bseverns/MOARkNOBS-42/firmware/include/DisplayManager/README.md

# DisplayManager

Part of the firmware `include` jungle. Check the [include README](../README.md) if you get lost in pixels, and the [main firmware README](../../README.md) for the grand tour.

Talks to the SSD1306 OLED and isn't afraid to shout.

## Where it fits

DisplayManager takes button-driven context and splashes it to the SSD1306 over I2C. ConfigManager tells it what to show.

```
[Button ctx] --> DisplayManager --> SSD1306
```

More backstory in the [main firmware README](../../README.md).

## Key Methods

| Call | What it paints |
| ---- | --- |
| `begin()` | Fire up the display hardware |
| `showText(line1, line2, line3)` | Scribble three lines and bail |
| `updateFromContext(ctx)` | Let button events drive the UI |
| `showFilterTuning(labelFreq, freqValue, labelQ, qValue)` | Visualize filter pot tweaks |
| `showArpSettings(lengthTicks, shapeName)` | Keep the arpeggiator honest |
| `showARGInfo(methodName, envA, envB)` | Flash the active ARG combo |

## Typical Use

```cpp
#include "DisplayManager.h"

DisplayManager screen(0x3C, 128, 64);

void setup() {
  screen.begin();
  screen.showText("MN42", "ready");
}

void loop() {
  screen.updateFromContext(ctx);
}
```

For more pixels see [DisplayManager.h](../DisplayManager.h).

## Build Toggle (A/B)

You can force full-frame OLED transfers at compile time:

- Add `-DMN42_OLED_PARTIAL_UPDATES=0` to `build_flags` in `platformio.ini`.
- Omit it (or set to `1`) to keep dirty-region partial updates enabled.
