bseverns/MOARkNOBS-42/docs/examples/max/README.md

# Max Listener Patch

`mn42_listener.maxpat` is a minimal monitor patch for bridge OSC output.

```mermaid
flowchart LR
  MaxPatch[mn42_listener.maxpat]
  Bridge[[MN42 Bridge]]
  Controller((MN42))
  MaxPatch -->|OSC 9000| Bridge
  Bridge -->|serial JSON| Controller
  Controller -->|slot/envelope dump| Bridge --> MaxPatch
```

## Run it

1. Start the bridge:
   ```bash
   node bridge/mn42_bridge.js --osc 9000 --osc-listen 9000
   ```
2. Open `mn42_listener.maxpat` in Max.
3. The patch's `udpreceive 9000` object receives `/mn42/slots` and `/mn42/envelopes`.

Use it as a starting point for mapping, visuals, or DAW control.
