bseverns/MOARkNOBS-42/docs/index.md

---
hide:
  - navigation
  - toc
---

<div class="mn42-landing-hero" markdown="1">

<p class="mn42-eyebrow">Small-batch MIDI/OSC performance instrument</p>

# MOARkNOBS-42

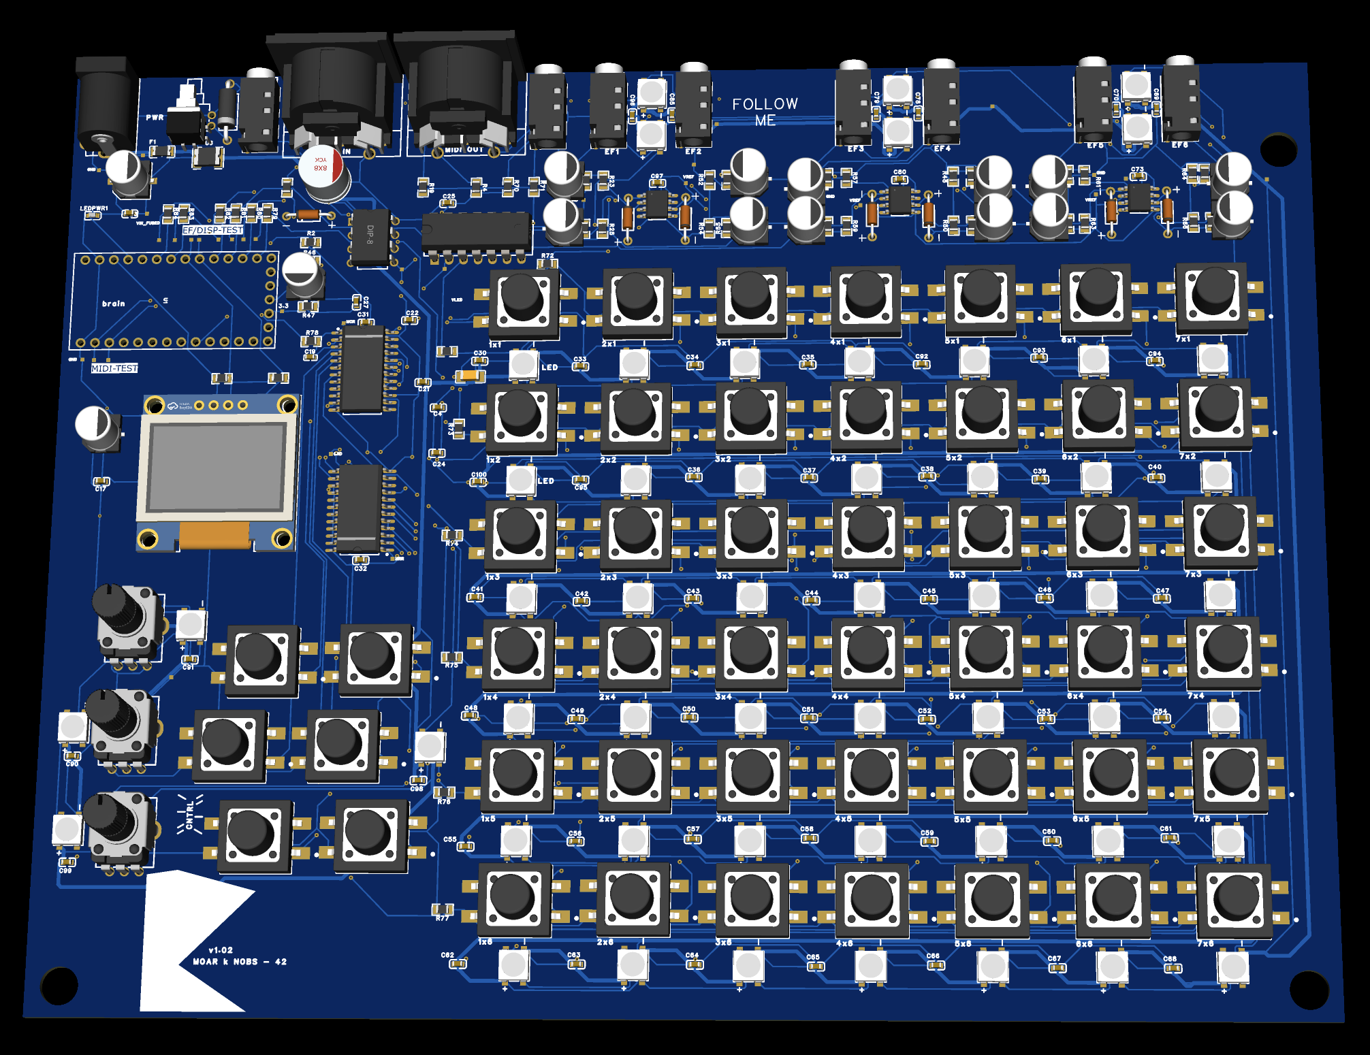
[picture p21: docs/assets/board/moarF.png]
Front view of the MOARkNOBS-42 board showing the full control surface, display area, and hardware layout.


MOARkNOBS-42 is a reactive performance instrument where a hand, a sound, time, or another MIDI device can move a configured destination. The musical work is deciding how those sources cooperate, replace one another, or hand control back to the performer.

Its open hardware, firmware, browser App, profiles, Bridge, and evidence trail keep those unusual relationships visible instead of sealing them inside a preset.

For the whole object-to-software picture in one glance, read the [System Map](getting-started/SystemMap.md).
Teaching a newcomer? Throw them into [Learner Paths](learn/LearnerPaths.md) so they can chase one signal at a time.

<div class="mn42-cta-row">
  <a class="md-button md-button--primary" href="https://bseverns.github.io/MN42/">Try the configurator</a>
  <a class="md-button" href="project/PilotRun/">Read pilot-run framing</a>
  <a class="md-button" href="#core-features">See features</a>
  <a class="md-button" href="getting-started/StartHere/">Start here / learn how it works</a>
</div>

</div>

## Control is the instrument

A knob can establish a baseline. Envelope followers and ARG can let the environment shape a reactive slot. An LFO can add time. On eligible direct CC slots, incoming MIDI can establish a remote value and soft pickup lets the performer physically cross it to take control back without a jump.

These are explicit, bounded behaviors rather than one vague “modulation” feature. [Who Controls This Slot?](learn/OneSignalPath.md) shows the reactive-composition and external-takeover paths side by side. [Why MN42](getting-started/WhyMN42.md) explains why that model matters musically.

## Validated host surfaces

<div class="mn42-callout mn42-callout-support" markdown="1">

The broad workflow story is real, but the compatibility claim should be read conservatively.

- strongest direct-browser evidence in this repo: Chromium-based configurator over WebSerial
- strongest desktop host evidence in this repo: Node 24 bridge with the browser console and `/app/` configurator path
- documented but still setup-specific: OSC hosts and DAW virtual MIDI workflows
- not claimed here as a verified production path: Firefox/Safari WebSerial and signed one-click bridge installers

See [Host Compatibility](reference/HostCompatibility.md) and [Connectivity Guide](getting-started/ConnectivityGuide.md) before treating the project like a universal host/browser promise.

If you want the repo's document tie-break rules before you go deeper, read [Documentation Truth Map](reference/DocumentationTruthMap.md).

</div>

## What it is

MOARkNOBS-42 is a small-batch MIDI/OSC performance instrument with a surrounding ecosystem, not just a bare controller board.

The object in your hands is only part of the story.

<div class="grid cards mn42-card-grid" markdown="1">

- **Surface**

  The hardware is a real performance surface with documented signal flow, MIDI I/O, reactive inputs, and a control layout meant to stay legible.

- **Configurator**

  The browser configurator handles setup, monitoring, staged edits, and profile management without hiding the device contract behind mystery software.

- **Bridge**

  The bridge path opens documented OSC and virtual MIDI workflows when direct browser connection is not the right fit for the host setup.

</div>

If you want the short outsider-friendly version first, read [Why MN42](getting-started/WhyMN42.md).

## Why it feels different

Many controllers are designed to disappear behind presets, hidden mappings, or sealed software stacks. MOARkNOBS-42 goes the other direction: it makes value ownership and contribution part of the performance.

- A physical baseline can be shaped by sound and time through documented route modes.
- Profile-owned incoming MIDI can control eligible destinations without the App or Bridge attached.
- Soft pickup lets the performer's hand resume control without snapping the value.
- The hardware, firmware, configurator, and bridge are documented as one legible system.
- The instrument is open enough to rebuild, audit, and remix rather than merely consume.
- The docs are part of the instrument, not a last-minute appendix.
- Validation, support boundaries, and unverified areas are called out directly instead of buried under marketing language.

The goal is not mass-market smoothness. The goal is an instrument whose control logic stays visible.

## Core features

<div class="grid cards mn42-card-grid" markdown="1">

- **42 virtual slots**

  The instrument centers around 42 virtual slots that can be mapped, recalled, and watched as part of the same runtime system.

- **Six envelope followers**

  Six reactive inputs let the rig respond to real signal activity instead of only static knob gestures.

- **Browser configurator**

  The configurator handles setup, monitoring, staged edits, and profile work in plain language over the documented device contract.

- **Profiles and recall**

  Profile slots `A` through `D` preserve working states, including reactive behavior and incoming MIDI bindings, instead of requiring a live rebuild.

- **Incoming MIDI takeover**

  Firmware-owned CC routes let other machines control supported destinations, with Continuous, Momentary, Toggle, range, and takeover behavior stored in the profile.

- **OSC / virtual MIDI bridge**

  The bridge exposes documented OSC and virtual MIDI paths, and now includes a browser-driven local console.

- **Dual MIDI hardware formats**

  Current repo docs describe both 5-pin DIN and 1/8" TRS Type-A MIDI hardware support.

</div>

## Who it's for

<div class="grid cards mn42-card-grid" markdown="1">

- **Experimental musicians**

  For performers who want the controller to be part of the instrument, not just a utility layer.

- **Sound and media artists**

  For people working across browser tools, OSC hosts, DAWs, installation contexts, or custom performance setups.

- **Advanced builders**

  For people comfortable with hardware reference files, flashing firmware, and validating real hardware behavior on the bench.

- **Educators and instrument hackers**

  For workshops, studios, and classrooms where openness, legibility, and rebuildability matter as much as the final sound.

</div>

This is best suited to people who are comfortable exploring systems rather than expecting every edge case to be hidden behind a wizard.

## Pilot Run / Artist Edition

The right frame for a first small-batch release is a pilot run: an artist-run instrument release with a documented ecosystem around it, not a generic consumer launch.

What that currently means in this project:

- the instrument hardware itself
- the current firmware and its documented behavior
- the browser configurator workflow
- the OSC / virtual MIDI bridge workflow
- the builder, performer, validation, and troubleshooting docs that explain how to use and verify it

What it does not mean:

- implied mass-market support coverage
- undocumented host compatibility guarantees
- invented timelines, pricing, or bundle promises that are not yet published

See [Pilot Run / Artist Edition](project/PilotRun.md) for the project-specific explanation.

## What it is not

<div class="mn42-callout mn42-callout-not" markdown="1">

This is not a generic plug-and-play controller for everyone.

It is not framed here as a sealed appliance, a beginner-friendly consumer gadget, or a promise that every host/workflow has already been validated. It is a particular kind of open, teachable performance instrument for people who value legibility, modification, and documented behavior.

</div>

## Support boundary

<div class="mn42-callout mn42-callout-support" markdown="1">

Support here is docs-first and artist-run.

The repo publishes workflows, validation guidance, and support boundaries clearly, but it does not promise consumer-style warranty handling, substitute-part approval, or universal one-on-one setup support. The practical boundary is described in [License and Support](project/LicenseAndSupport.md).

</div>

## Interested in the first batch?

<div class="mn42-callout mn42-callout-pilot" markdown="1">

If the instrument makes sense for your setup, the next useful step is not a vague preorder mindset. It is reading the pilot-run framing, checking the support boundary, and choosing the workflow path that matches how you actually work.

<div class="mn42-cta-row">
  <a class="md-button md-button--primary" href="project/PilotRun/">Read pilot run details</a>
  <a class="md-button" href="project/LicenseAndSupport/">Read support boundary</a>
  <a class="md-button" href="getting-started/QuickstartForPerformers/">See performer workflow</a>
</div>

</div>

## Choose your next step

<div class="grid cards mn42-card-grid" markdown="1">

- **Quickstart for Builders**

  Ordering parts, flashing firmware, and first bring-up: [Quickstart for Builders](getting-started/QuickstartForBuilders.md)

- **Quickstart for Performers**

  Connect the board, use the configurator, and work with profiles: [Quickstart for Performers](getting-started/QuickstartForPerformers.md)

- **Connectivity Guide**

  Decide between direct WebSerial and the bridge path: [Connectivity Guide](getting-started/ConnectivityGuide.md)

- **Validation Flow**

  Use the conservative go/no-go path from bring-up to demo-ready: [Validation Flow](validation/ValidationFlow.md)

- **Documentation Truth Map**

  See which pages define current truth versus plans, evidence, or historical context: [Documentation Truth Map](reference/DocumentationTruthMap.md)

- **Demo Test Punch List**

  Run a real-world prototype or rehearsal pass: [Demo Test Punch List](validation/DemoTestPunchList.md)

- **Guided Routes and deep docs**

  Choose a learning path or dive into the dense technical library: [Guided Routes](getting-started/GuidedRoutes.md) and [Docs Guide](project/DocsGuide.md)

</div>

## FAQ

<details markdown="1">
  <summary>Do I need to code?</summary>

Not necessarily. A performer can use the configurator and profile workflow without changing firmware. A builder or remixer will get much more out of the project if they are comfortable reading docs, flashing firmware, and following validation steps.

</details>

<details markdown="1">
  <summary>Is it open source?</summary>

Yes. The repo publishes firmware, software, hardware documentation, and supporting docs under the licenses described in [License and Support](project/LicenseAndSupport.md).

</details>

<details markdown="1">
  <summary>Is this a finished consumer product?</summary>

Not in the sense of a mass-market plug-and-play device with universal compatibility claims. The project is documented, real, and usable, but it is still framed honestly as a small-batch, artist-run instrument ecosystem with explicit validation and support boundaries.

</details>

<details markdown="1">
  <summary>What does the configurator do?</summary>

The browser configurator is the main setup and monitoring surface. It loads manifest/config data, stages edits safely, applies changes, and handles profile save/load workflows over the documented device contract.

</details>

<details markdown="1">
  <summary>What support is included?</summary>

The main support surface is the documentation itself: quickstarts, connectivity guidance, validation flow, troubleshooting, and license/support boundaries. Use [GitHub Issues](https://github.com/bseverns/MOARkNOBS-42/issues) for public questions or reproducible bugs. See [License and Support](project/LicenseAndSupport.md) and [Pilot Run](project/PilotRun.md) for the practical limits and private contact path.

</details>

<details markdown="1">
  <summary>Why would I choose this instead of a generic MIDI controller?</summary>

Because the value here is not just the control surface. It is the combination of hardware, firmware, configurator, bridge, and unusually explicit documentation. If that matters to you, read [Why MN42](getting-started/WhyMN42.md).

</details>
