bseverns/MOARkNOBS-42/wiki/Firmware.md

# Firmware

Firmware lives under `firmware/` and targets Teensy 4.0.
Canonical source: `firmware/README.md`

## Build commands

Run from repo root:

```bash
pio run -d firmware -e teensy40_main
pio run -d firmware -e teensy40_main -t upload
```

## Test environments

- `teensy40_full_system`
- `teensy40_unified_test`
- `teensy40_biquad_test`
- `teensy40_eeprom_persistence`
- `teensy40_slot_verify`
- `teensy40_unity` (Unity harness)

## Key modules

- `ButtonManager` - matrix scanning, gesture handling
- `PotentiometerManager` - analog sampling and smoothing
- `EnvelopeFollower` - modulation extraction and filter modes
- `MIDIHandler` - USB/DIN/TRS message handling
- `ConfigManager` - generation-backed LittleFS persistence, validation, and
  recovery
- `LEDManager` + `LedAnimator` - visual state
- `Arpeggiator`, `LFOManager`, `ARGMixer` - modulation engines

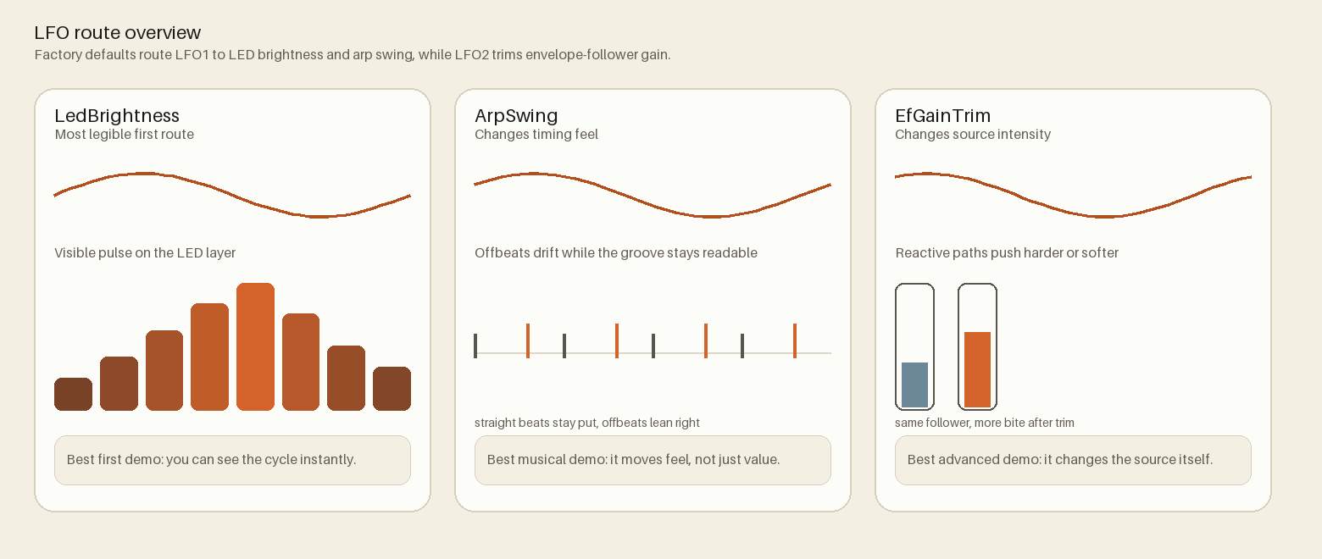
[picture p23: wiki/assets/signal-shapes/lfo-route-overview.png]
LFO routing overview showing two low-frequency oscillators feeding internal targets, MIDI CC and NRPN outputs, slot values, envelope gain trim, and LED brightness.


## Runtime and protocol highlights

- Command dispatch and queue processing are split for clearer ownership.
- JSON manifest/config handshake drives host UI compatibility.
- Scheduler separates high/mid/low priority tasks.

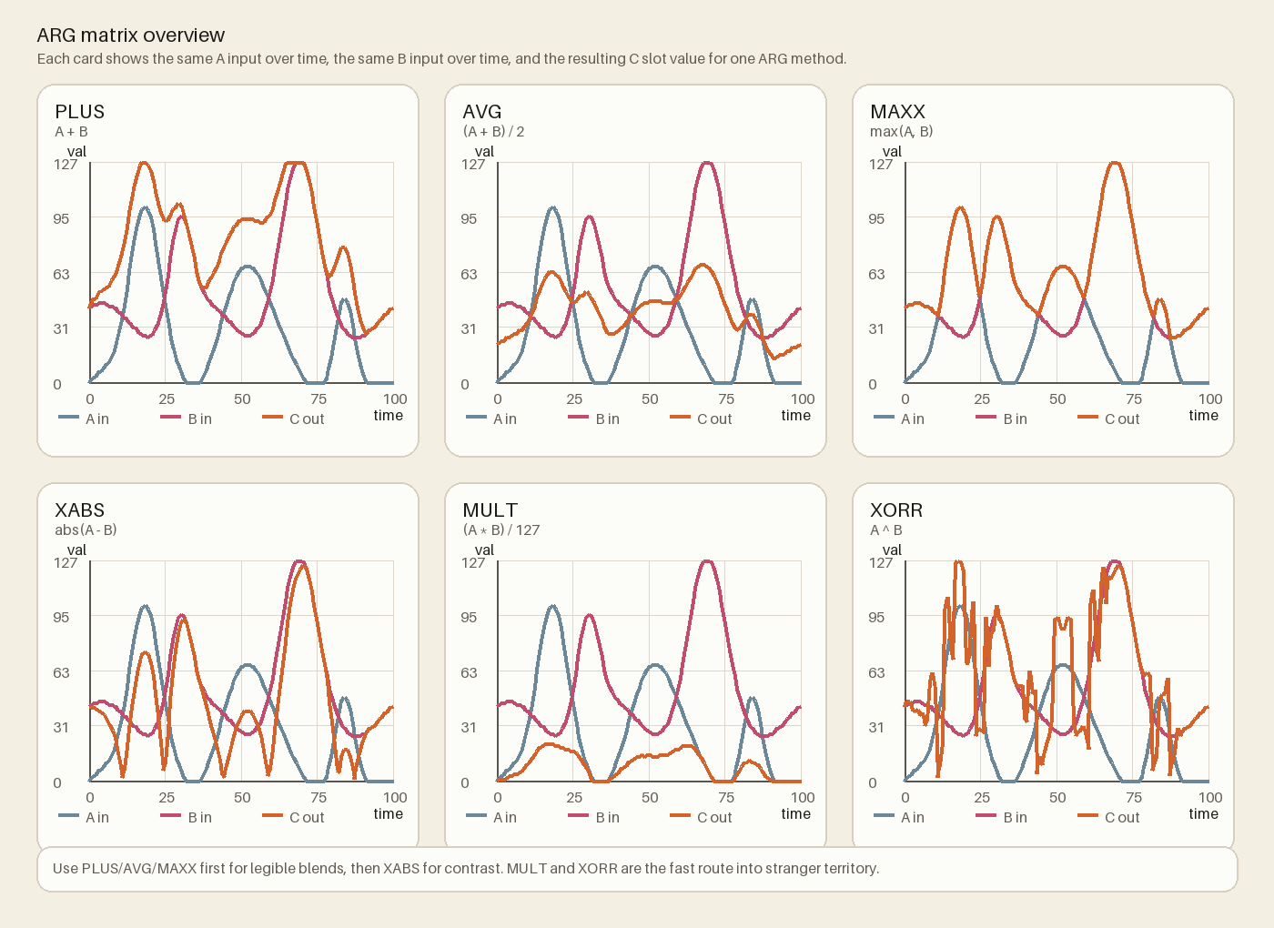
[picture p24: wiki/assets/signal-shapes/arg-matrix-overview.png]
ARG overview comparing two input envelopes with the resulting output for PLUS, average, maximum, absolute difference, multiplication, and XOR-style methods.


## Envelope shape quick look

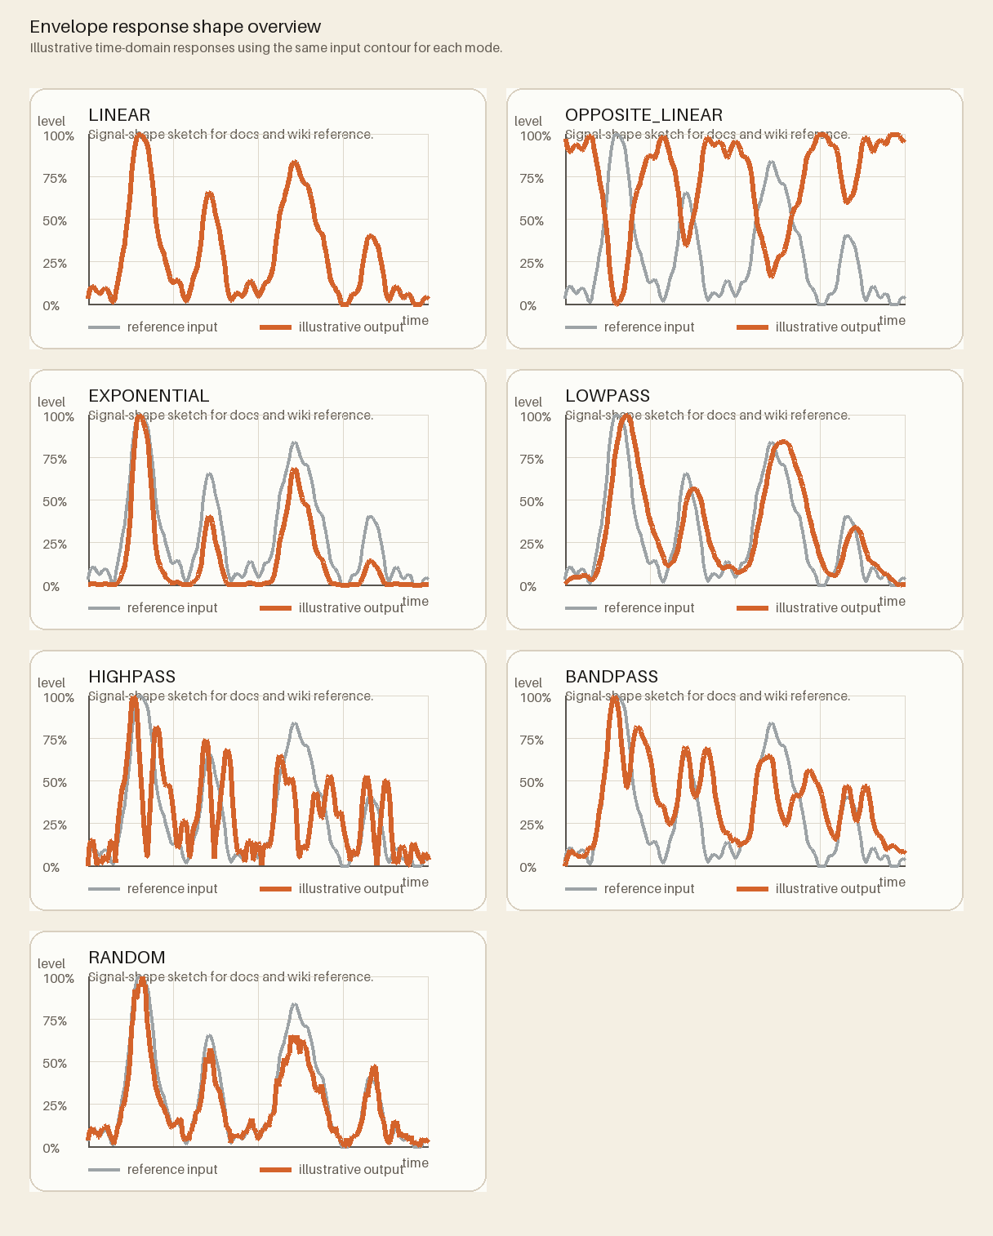
[picture p25: wiki/assets/signal-shapes/filter-shapes-overview.png]
Overview chart comparing one reference envelope against LINEAR, OPPOSITE_LINEAR, EXPONENTIAL, LOWPASS, HIGHPASS, BANDPASS, and RANDOM response modes so newcomers can see how the firmware's reactive-control shapes differ.


Use this as a fast visual map only. The deeper learner-facing explanations live in `docs/guides/FilterFeelGuide.md` and `docs/guides/ReactiveControlGuide.md`.

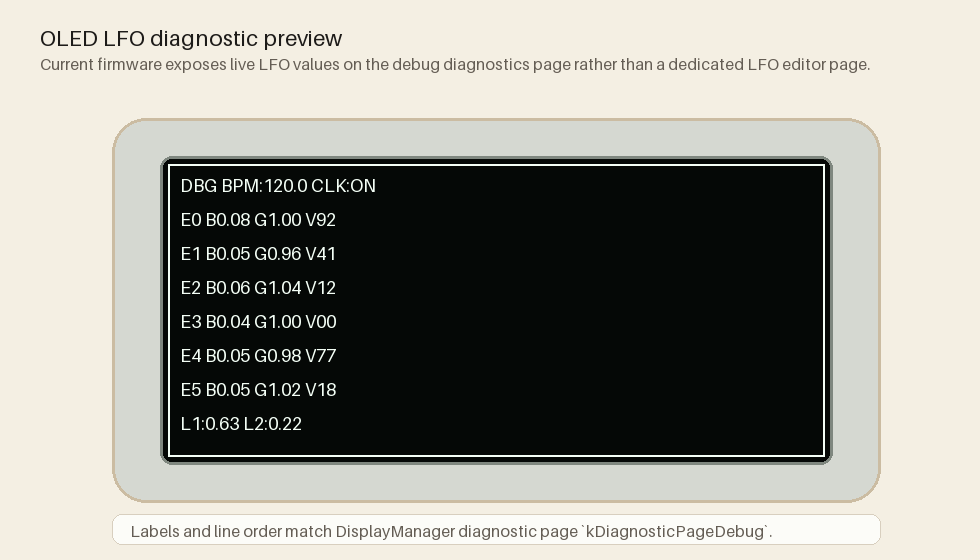
[picture p26: wiki/assets/signal-shapes/lfo-oled-preview.png]
Mock OLED diagnostics view showing BPM and clock status, six envelope baseline-gain-value rows, and two normalized LFO values.


## Reference docs

- `firmware/README.md`
- `firmware/include/*/README.md`
- `docs/guides/WebSerial.md`
- `docs/reference/PinMap.md`
- `docs/reference/PersistenceContract.md`
- `docs/reference/EEPROMLayout.md` (legacy schema-4 layout only)
