bseverns/MOARkNOBS-42/docs/app/AppBehaviorContract.md

# App Behavior Contract

> **Doc class:** Contract. This page defines browser-configurator behavior. The concise [App README](https://github.com/bseverns/MOARkNOBS-42/blob/main/App/README.md) is the operational entry point.

## Runtime ownership

- `App/runtime.js` is the runtime composition root. It wires transport, contract, configuration-session, telemetry, and
  live-control services, but does not define their schema, transaction, or device-policy rules.
- `App/views/benzknobz.js` is the view composition root. It assembles panels/controllers and binds operator controls to
  the public runtime API; device truth and write policy must remain behind those dependencies. `App/views/panels/lab_bench.js`
  owns the Bench's spatial composition and reparenting while preserving the DOM identities owned by its controllers.
- `App/runtime/` owns manifest/schema negotiation, state normalization, validation, staged diffs, checksummed Apply,
  uncertainty/resynchronization, telemetry coalescing, and transport-specific behavior.
- `App/config_schema.json` is the bundled schema 9 fallback. A compatible device-provided schema takes precedence.
- `App/benzknobz.css` defines shared visual tokens and mode presentation.

The view must not invent device truth. Identity, capabilities, configuration, persistence actions, and power-safety
metadata remain manifest-, schema-, command-, or telemetry-backed.

## Transport modes

The App supports direct WebSerial, structured Bridge session, raw Bridge compatibility, and simulator transports. Their
operator labels and truth boundaries are normative in [App Transport Truth Table](AppTransportTruthTable.md).

Direct WebSerial requires a secure context or localhost and a user gesture for port selection. The App may remember
USB identifiers and a staged snapshot, but it must not reopen a serial port without a user gesture.

## Handshake and compatibility

Connect remains busy until transport handlers and runtime subscriptions are bound. A successful device session obtains
identity, manifest, schema, and configuration before enabling authoritative editing. Before that handshake, bundled
fallback data must not be presented as attached-device truth.

A schema mismatch enters `migration-required` and blocks Apply. The App supports export and inspection in that state;
it must not advertise a migration transform until that transform, validation, diff, and operator confirmation flow is
implemented and tested.

## Draft and Apply semantics

The browser maintains live device state separately from a staged candidate. Edits, imported JSON, and recipe actions
update the candidate first. A write occurs only through an explicit action on the relevant write lane.

The primary configuration Apply sends a validated, checksummed candidate. A valid receipt plus authoritative readback
establishes device truth. Missing, malformed, or contradictory receipts enter uncertainty/resynchronization; they do not
prove rollback. The candidate stays visible until readback resolves the outcome.

Profile, scene, macro-recall, and transport actions use their native command paths rather than masquerading as config
diffs. Actions that can replace a dirty configuration draft must be blocked until the operator applies or discards it.
Schema-rendered controls stage browser intent synchronously and debounce only outbound live patches. Destroying or
rebuilding a rendered control must cancel its pending transmission without discarding the staged edit. Removing an
array item remains authoritative over timers owned by that item's former controls.

The complete state model is [Configuration Transaction Model](../reference/ConfigurationTransactionModel.md).

## UI modes

- **Stage** is the performance surface: connection, live profile/scene recall, power safety, slot activity, envelope
  levels, motion, and panic help.
- **Configure** is the default selected-slot workspace: Mapping, one Reactive path (EF source, ARG relationship, then EF character), and Motion/fixed LFO lanes. ARG constructs the Reactive input before EF shaping; it is not a peer output stage. Motion shows each shared generator’s shape and rate while generator edits remain in Lab.
  The signal strip displays device observations separately from staged settings.
- **Lab** exposes complete EF, ARG, fixed-LFO, filter, LED, scope, MIDI-monitor, import/export, and diagnostic controls.
  Every device-schema configuration root must have a marked Lab surface, and the hand-built selected-slot editor must
  account for every slot-schema leaf. Its full-width Bench separates Instrument, Profile, Observe, and Evidence
  workspaces while keeping each room's major tools named in the Bench navigation. Scope, MIDI Monitor, Device Monitor,
  Modulation Matrix, Staged Diff, Slot Inspector, and Debug Log must remain discoverable even when their room is closed.
  Instrument visually separates staged **Machine configuration** (Apply required) from immediate **Live device controls**
  (writes now), without splitting either into a separate Lab room. Lab uses a compact, consistent set of inline SVG
  landmarks for rooms and major tools: faders for Instrument, a saved card for Profile, a scope for Observe, and a
  document lens for Evidence. Major cards repeat their room's visual language or use a specific musical/control
  metaphor. The SVGs remain decorative and text labels remain authoritative; dense telemetry cells stay icon-free.

Lab presents profile-owned incoming MIDI routes as the **Incoming MIDI** tab in **Profile Performance**, beside the
profile arpeggiator and LFO/routes tabs. It must not place those routes inside **Selected Slot**: a route can target any
slot or a machine-level performance parameter and travels with its profile.

The selected-slot Mapping tab names `data1` according to the chosen outgoing message: **CC number**, **Note number**,
**Program number**, **NRPN parameter**, or **RPN parameter**. It omits that control for OFF, Pitch Bend, Aftertouch,
Mod Wheel, and SysEx; SysEx exposes its template instead. Hiding the control does not clear the staged `data1` value.

Envelope detection mode is slot-owned (`slots[].ef.mode`). Two slots may share one physical follower assignment while
keeping different Peak, RMS, Gate, or Follower settings. The top-level `envelopeMode` value is a legacy
compatibility/OLED label; changing it must not rewrite any slot's detector mode.

The persisted compatibility values remain `stage`, `basic`, and `advanced`. A mode may hide complexity, but it must not
change the authority or write semantics of the underlying state.

The State drawer groups presets, profile persistence, and file backups without merging their authority. Selected-slot
markers reflect exact staged diffs. Review focuses the matching Lab field; Customize/Return preserve slot and lane.
Continuous Lab slot controls support sliders and reset-to-confirmed staging, with logarithmic millisecond travel.
Signal contribution graphics require a coherent, recent measured snapshot; missing components remain unreported.

## Device-backed and browser-local state

Device-backed controls must be advertised by the manifest/schema or a documented live protocol lane. Browser-only slot
labels remain local metadata and must not be serialized as device configuration. Legacy browser-local MIDI-badge
metadata may still be read, but Configure does not expose it as instrument behavior. Optional display metadata sent to
the Bridge remains advisory and cannot affect routing authority.

Import stages configuration locally. Export saves the current candidate, including unsent edits. Profile A–D actions,
scene actions, macro actions, and live controls remain capability-gated so older firmware fails closed.

## Telemetry and visualization

The runtime coalesces telemetry into approximately 50 ms paint frames. Scope time is host-observed arrival time, not
firmware-source time or round-trip latency. EF and LFO traces, activity holds, and simulator traces are musical/operator
visualization; latency-grade claims require the [bench latency method](../bench/latency/method.md).

The simulator uses the same runtime API and deterministic synthetic telemetry. **Start Simulator** opens the
firmware-canonical reset fixture: Profile A, channel 1 / CC 0 pots, default EF payloads, disabled slots and ARG, and
no LFO routes. **Load Demo Rig** is an explicit simulator-only fixture with illustrative mappings, EF/ARG examples,
and active LFO routes. Session names the active fixture, and loading a fixture replaces the simulator's authoritative
configuration rather than staging browser intent. Its selected-slot contribution frames and Mod Matrix consume the same
active-profile LFO routing graph, including the firmware compatibility rule that a fixed slot lane shadows an older
SlotValue route for the same slot/LFO pair. Contribution frames honor confirmed ARG sources/methods and each fixed LFO
lane's enabled, amount, and combine settings so the causal signal strip can rehearse the device resolver accurately.
It is suitable for UI behavior, automation, screenshots, schema/migration rehearsal, and staged-transaction tests. It
is not analog calibration, electrical, physical-control, transport-latency, or hardware-validation evidence.

## Accessibility and input

Controls require visible labels, keyboard operation, logical focus order, and non-color status cues. The selected-slot
surface supports arrow-key navigation and documented coarse/fine adjustment. Dialogs and status announcements must
remain usable without relying on pointer interaction or color alone.

Because the current incoming route schema supports only 7-bit Control Change, the route editor labels the source group
**Incoming CC** and does not render a one-option message-type selector. If the negotiated schema advertises multiple
message types, that field becomes a selector. Takeover remains stored for each route but is disabled and unfocusable
unless Interaction is Continuous, because it has no runtime effect for Momentary or Toggle routes.

## Verification

Run:

```bash
npm --prefix App test
npm --prefix App run test:architecture
```

Playwright exercises the real runtime/view modules through the stable `benzknobz.html` harness, including simulator,
schema validation, staged diff, Apply/receipt failures, uncertainty recovery, migration blocking, profiles, and the
mode surfaces. A small approved snapshot set protects the top-level Configure, Lab, Stage, and open Incoming MIDI
hierarchies. Because the App deliberately uses native system UI and monospace font stacks, those approved images run on
the canonical macOS + pinned Playwright Chromium CI lane; other platforms skip only these four pixel assertions and
still run the remaining App suite. Routine screenshot artifacts remain diagnostic rather than approved baselines. `lab_config_coverage.spec.js`
derives its expected roots and slot leaves from the canonical schema, then checks that Lab marks every one and preserves
independent slot EF modes through Apply/readback. The architecture guard
rejects coordinator imports that bypass the public layers and policy-shaped code that would pull schema constraints,
transaction semantics, or device capability decisions back into the two composition roots. Operator-facing hardware
claims additionally require receipts under `docs/bench/app/`.
