bseverns/MOARkNOBS-42/docs/bridge/BridgeConsoleTour.md

# Bridge Console Tour

The Bridge console is the operator-facing desktop view for `MN42 Bridge`. Use it when you need desktop OSC/MIDI routing, a cached device session, or an App-over-bridge path that does not depend on browser WebSerial support.

For the full Bridge doc split, see [Bridge Docs Map](BridgeDocsMap.md).
For transport and support-boundary tie-breaks, see [Bridge README](https://github.com/bseverns/MOARkNOBS-42/blob/main/bridge/README.md), [Bridge Transport Contract](./BridgeTransportContract.md), and [Bridge Write Lanes](./BridgeWriteLanes.md).

## Before You Start

- Start the console with `npm --prefix bridge start`.
- Open `http://127.0.0.1:8787/`.
- Use Node `24.x` only; the Bridge package still pins `>=24 <25`.

Screenshot note: the images below were captured on 2026-08-03 from the local Bridge console against the repository's MN42 device simulator. They preserve a complete cached-session example but predate the visible label change from `Mappings / Stage / Advanced` to `Routing / Monitor / Diagnostics`; they also predate the September patchbay redesign. They are historical UI documentation, not hardware validation evidence.

Simulator session example from this capture:

- serial path: `/dev/simulated-mn42`
- firmware identity: `MOARkNOBS-42` / schema `8` / git `simulated`
- power boundary: `POWER_CHOKED_V1`
- LED cap: `26`
- rail state: `unverified`

## Setup Mode

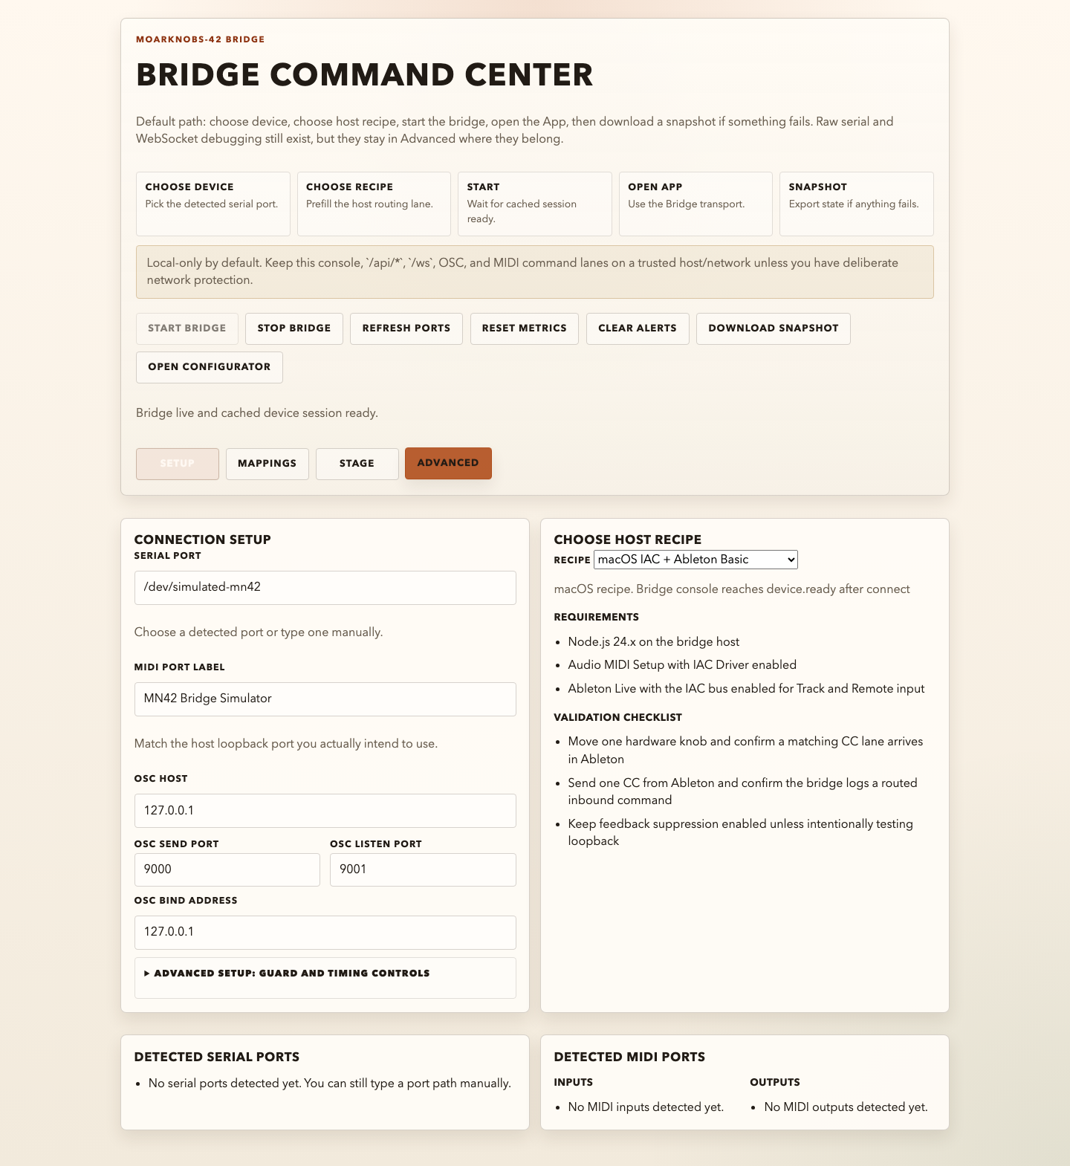
[picture p27: docs/images/bridge-setup-mode.png]
Bridge console Setup mode with serial port entry, recipe picker, and start controls


Setup mode is where a non-developer operator should start.

This capture shows a complete setup path, including the simulator serial path, a simulator MIDI label, and the top-line `Bridge live and cached device session ready.` status after the operator has started the Bridge.

- `Serial port` is the firmware USB path. Pick a detected entry from the list or type it manually if the detector missed it.
- `Host recipe` prefills documented host settings and shows the resolved MIDI and OSC destinations. It is the fastest safe path for an operator who is not debugging custom routing.
- `Edit routing details` reveals the MIDI port and raw OSC address/port fields when this computer differs from the recipe. Its nested guard and timing controls should stay at their defaults unless a host recipe or bench note says otherwise.
- `My Performance Setups` saves named copies of computer/rig routing, destination names, routes, optional notes, and an advisory MN42 profile in this browser. Loading a setup only fills the form; it never starts or restarts routing or changes firmware state. Use JSON export/import to back up the collection or move it to another browser.
- `Start current setup` launches the desktop runtime from the manual workbench. `Stop bridge` remains available in every mode, is visually marked as destructive, and asks for confirmation before disconnecting the serial/MIDI/OSC runtime. `Refresh ports` rescans serial and MIDI devices.

When saved setups exist, Setup leads with a rig recall card showing exact ports, destination names, the advisory profile, notes, and last-used time. **Start this setup** explicitly loads and starts that saved host configuration, preserving its ports even if another device is detected. It is disabled while routing runs. **Edit** and **New setup** reveal the collapsed manual workbench; Edit loads the selected rig into its editor. Last-used time is recorded after a successful start and survives JSON export/import; older version 1 files remain compatible.

Performance Setups are personal operator convenience, not known-good recipes or host-validation evidence. When routing is already running, stop and start the Bridge deliberately after loading a setup whose MIDI or OSC transport values should take effect.

### Serial Port Selection

The serial chooser is intentionally simple:

- Prefer the detected list first.
- If the board appears as `/dev/tty.*` on macOS, the console will prefer the matching `/dev/cu.*` path for you.
- If nothing is detected, you can still type the port path manually and start the Bridge.

## Routing Mode

Routing mode provides a guided, passive MIDI-learn path for custom MIDI CC → OSC routing:

1. Start the Bridge and select `Listen for MIDI CC`.
2. Move one knob, fader, or pedal. The console captures its channel and CC number from the inbound route trace; feedback-suppressed echoes are ignored.
3. Choose a recently observed custom outbound OSC address or type the destination required by your host patch. The learner excludes the reserved `/mn42/*` namespace because those addresses have documented payload contracts.
4. Review the inline route summary and select `Confirm and add route`.

Learning does not emit MIDI, OSC, or device writes. The **Live now** badge marks MIDI → OSC custom routes because adding or removing a confirmed route updates live Bridge routing without restarting transports. Routes loaded into the Setup form from a Performance Setup are pending setup changes until the Bridge is deliberately started with that setup. A custom route is additive: its inbound CC still follows the existing typed OSC and device-control lanes. Custom routes remain intentionally limited to MIDI CC input and OSC output; use the Diagnostics route trace when you need to verify a more complex typed-event path.

### Device telemetry → MIDI

The **Next start** badge marks Device → MIDI routes. Add a route by choosing Slot or EF, a source number starting at 1, MIDI CC 0–127, and channel 1–16. Cards show pending routes and offer Remove. Sources absent from telemetry produce no output. Choose **Configured routes** to use the cards on the next Bridge start; legacy mode retains automatic CC assignments. These changes do not update running transports.

**Advanced / Edit raw route definition** retains JSON access with zero-based source indices. Invalid JSON, invalid entries, duplicate IDs, and more than 128 routes are rejected; correct the definition before starting or saving a setup.

## Monitor Mode

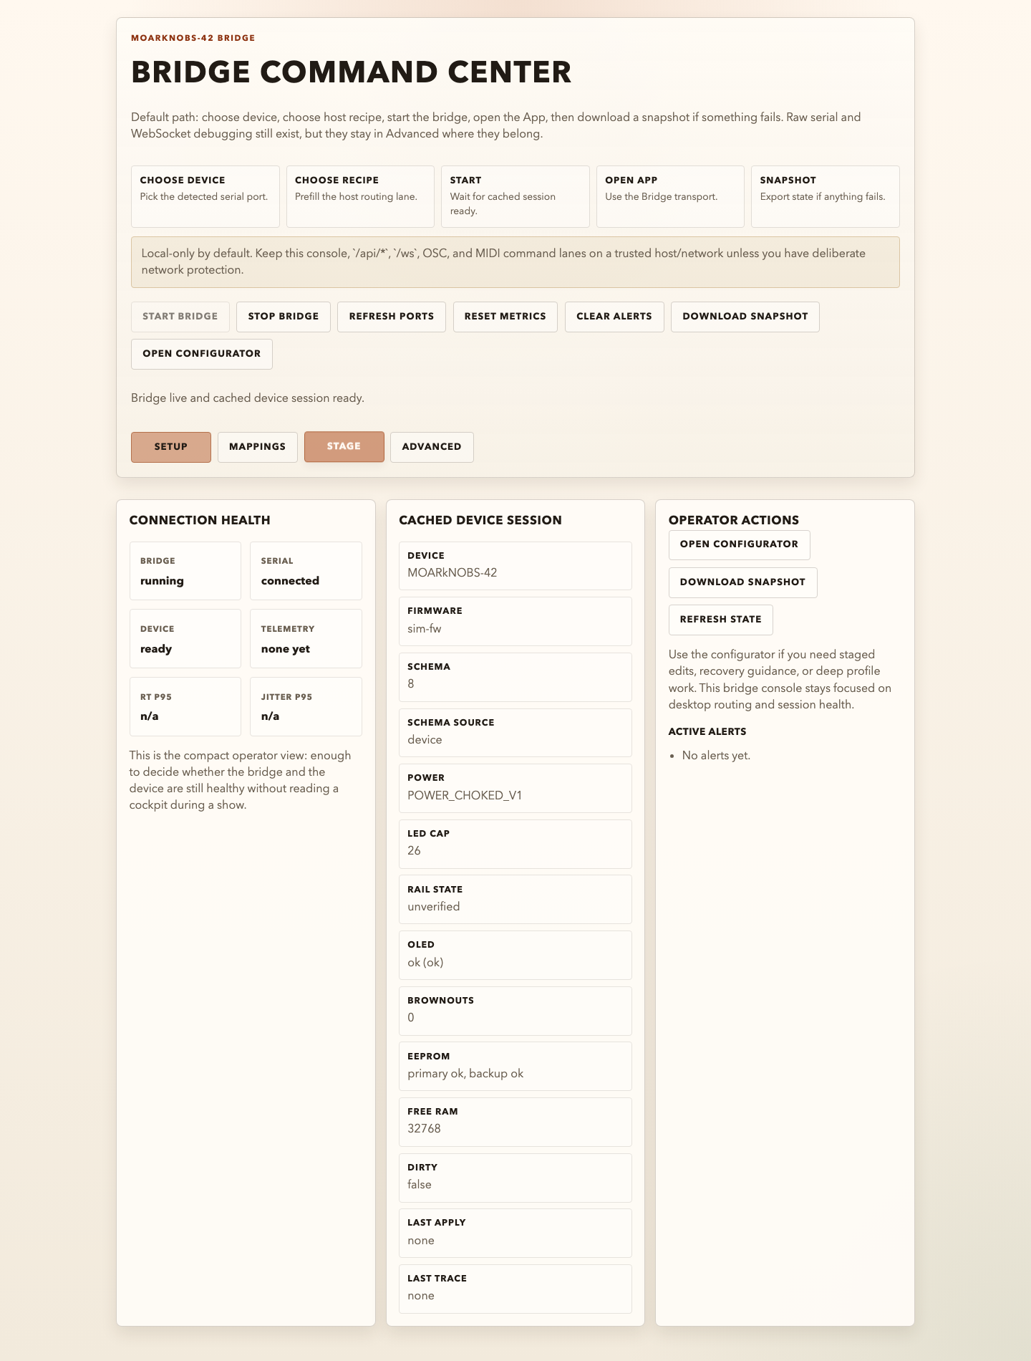
[picture p28: docs/images/bridge-stage-mode.png]
Bridge console Monitor mode with connection-health cards, cached device session, and operator actions


Monitor is the compact operator view. It is meant to answer “is the Bridge healthy?” without exposing raw debugging detail.

In the screenshot above, the simulated device is connected, `Device` is `ready`, and the cached session shows the simulator's `POWER_CHOKED_V1` boundary with `LED cap 26` and `rail state unverified`.

- `Bridge`, `Serial`, and `Device` show whether the desktop runtime is running, whether the serial link is up, and whether the device session is actually ready.
- `Telemetry` reports `live`, `delayed`, `stale`, or the relevant stopped/disconnected state instead of presenting an old timestamp as current activity. `RT p95` and `Jitter p95` summarize whether round-trip timing is staying inside configured targets.
- **Live patchbay** connects MN42, USB, Bridge, and the Device → OSC, Device → MIDI, OSC → Device, and MIDI → Device lanes. Destination labels describe configured intent; lane text and line styling show observed activity. Older traffic stays neutral, and dropped routes do not light a successful path. USB loss is explicit. Host application receipt is not confirmed.
- **Device verdict** keeps readiness, configuration attention, and the reported power profile visible. **Device details** discloses firmware identity, schema version/source, LED cap, rail state, config-export validation, device truth, draft state, and last apply result. A reported power profile is not a blanket safety verdict.
- `Operator actions` keeps only the show-safe actions visible:
  - `Open configurator`
  - `Download snapshot`
  - `Refresh state`

When validation fails, a device configuration draft is staged, or device authority differs from the candidate, Monitor changes the App action to `Open App to resolve` and explains why the cached state needs attention. This `Draft state` is intentional: unlike host-route form changes, it represents the real staged device-configuration lane shared with the App.

### Passive Soundcheck

`Start passive soundcheck` is write-free. It captures a live slot-telemetry baseline, asks the performer to move one stable, unmodulated hardware control, detects the next slot-value change, and checks for Bridge output traces alongside that movement. OSC is expected; MIDI is expected in legacy mode or when a configured MIDI slot route matches a changed slot. EF-only mappings do not require MIDI output during this slot check. Trace IDs correlate telemetry when available; otherwise the check uses a short time window, which cannot establish control-specific delivery. It does not generate MIDI notes, OSC commands, slot writes, or synthetic device movement. LFO or envelope modulation can also change slot telemetry, so use a stable slot when you want the result to correspond to a deliberate physical move.

The result reports OSC and MIDI independently and marks unmatched MIDI slots as not configured. A connection or routing change interrupts the check. The performer must confirm sound or visuals in the destination app; Bridge output is not a delivery acknowledgement. A missing lane means only that the Bridge did not observe that route during the check; confirm the selected host recipe, destination availability, and Diagnostics route trace before treating it as a hardware fault.

Alerts link to the relevant runtime, serial, or route evidence. Diagnostics also provides Problems, Routes, Serial, Logs, and Raw state navigation with keyboard focus at the destination.

### What “Session Ready” Means

The console reports the session as ready only after the Bridge has cached all of the following:

- `HELLO`
- `GET_MANIFEST`
- `GET_SCHEMA`
- `GET_CONFIG`

Until then, Monitor may show `awaiting HELLO`, `awaiting handshake`, or empty cached-session fields. That is expected during startup or after a reconnect.

In the screenshots for this tour, `ready` means the Bridge has already cached device identity, schema authority, a live config snapshot, and conservative power-boundary fields. Confirm those values on attached hardware before relying on them for a release or performance decision.

### App Launch

`Open configurator` launches `/app/` through the Bridge server, not through direct browser WebSerial.

That means:

- the App prefers the structured Bridge session when available
- the App can still fall back to raw Bridge `/ws` compatibility if structured session setup fails
- desktop OSC/MIDI routing can stay active while the operator uses the configurator

## Diagnostics Mode

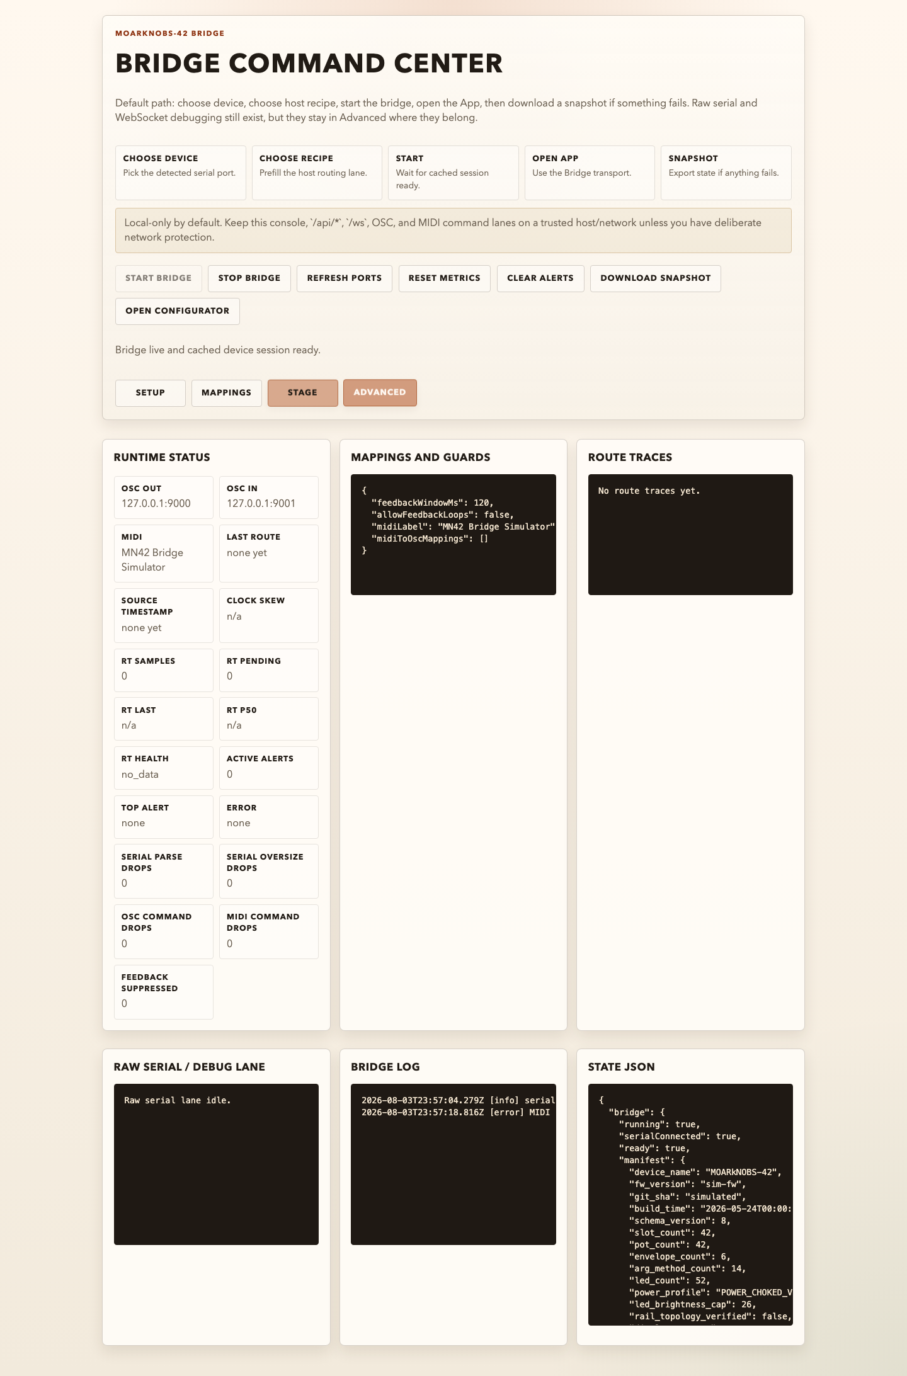
[picture p29: docs/images/bridge-advanced-mode.png]
Bridge console Diagnostics mode with runtime status, raw serial output, logs, route traces, and state JSON


Diagnostics is the evidence view. It is still operator-usable, but it assumes you need traces and details rather than a quiet status board.

This simulator capture shows three useful student-facing examples at once:

- the runtime and cached session are present
- the raw serial/debug lane and route trace surfaces are available for diagnosis
- the state JSON includes the same cached power and firmware identity fields shown in Monitor

- `Runtime status` expands the performance and error counters: OSC/MIDI endpoints, last route, source timestamp/skew, round-trip samples, parse drops, command drops, and feedback suppression counts.
- `Active routes and guards` shows the active MIDI-to-OSC route snapshot and guard settings.
- `Route traces` shows recent routed events at a human-readable level.
- `Raw serial / debug lane` is the direct line-oriented device feed. Use it only when you need to confirm exactly what the firmware emitted.
- `Bridge log` is the console/service log stream.
- `State JSON` is the most complete machine-readable snapshot of what the Bridge currently believes.

## Student Demo Path

For a classroom walk-through, use the same order the console uses:

1. Start in `Setup` and point out the exact serial port and MIDI label the host will use.
2. Switch to `Monitor` and wait for `Device` to become `ready`.
3. Call out the cached session facts that matter most:
   - firmware identity
   - schema version/source
   - power profile / LED cap / rail state
   - dirty state and last apply result
4. Open `Diagnostics` only after the students understand that `Monitor` is the operator truth surface and `Diagnostics` is the evidence/debug surface.

That sequence keeps the lesson anchored on operator decisions first, then on lower-level traces.

## Warnings And Alerts

Warnings surface in two places:

- the top summary line and status cards
- the `Active alerts` list in Monitor, which contains only unresolved alerts rather than cleared alert history

Use Diagnostics' `Clear alerts` when you intentionally want a fresh operator slate after acknowledging an issue. It asks for confirmation and warns that unresolved conditions may raise again. Do not clear alerts just to hide an unresolved fault.

Typical meanings:

- `awaiting handshake` or `awaiting HELLO`: serial link exists, but the device session is not ready yet
- `Draft state: draft staged`: staged Bridge config differs from live config and has not been promoted by a verified ACK
- `Config export: invalid`: the normalized device export failed the bundled App schema and was not accepted as live truth
- `Device truth: device differs from draft` or `apply outcome uncertain`: the operator must not infer that the candidate became live state
- `RT health` degraded or alert count rising: route timing or command health is outside the configured target window

## Snapshot, Disconnect, And Recovery Actions

The Bridge console exposes these operator actions today:

- `Stop bridge`: the practical disconnect action for the desktop runtime; it remains visible in all modes and requires confirmation
- `Download snapshot`: saves the current Bridge/session state for evidence or support review; Monitor provides its own contextual copy
- `Refresh state`: re-reads current Bridge state into the console
- `Reset metrics`: a Diagnostics-only action that clears accumulated round-trip metrics so you can measure a fresh run
- `Clear alerts`: a Diagnostics-only acknowledgement action that requires confirmation

There is no dedicated Bridge-console `panic` button today. If you need deeper recovery guidance or staged-config recovery tools, use `Open configurator` and work from the App’s recovery surfaces.

## Raw Serial / Debug Lane Boundary

The raw serial pane is useful, but it is not the primary operator lane.

- Use `Monitor` first for health decisions.
- Use `Diagnostics` only when you need evidence, traces, or direct line-level confirmation.
- Do not infer staged-config success from raw lines alone when the cached session/apply state is available; the Bridge’s structured session is the authoritative operator surface for staged/live/apply state.
