bseverns/MOARkNOBS-42/docs/bridge/BridgeTransportContract.md

# Bridge Transport Contract

> **Doc class:** Contract doc. This page defines the Bridge HTTP/WebSocket surfaces and App-facing session transport behavior.

This document describes the desktop-side transport surfaces exposed by `bridge/` after the bridge runtime upgrade. It is intentionally conservative: it documents what the repo now exposes, not a promise that every external tool should depend on every field forever.

## Surfaces

- `Contract negotiation`
  `/api/contract`
  Version and capability metadata for every structured HTTP and event client.
- `Raw debug transport`
  `/ws`
  Newline-delimited firmware lines. This is the compatibility/debug lane and the fallback App-over-bridge path.
- `Structured event transport`
  `/ws/events`
  Newline-delimited JSON event envelopes for session-aware consumers.
- `Structured device/session API`
  `/api/device/session`
  Cached session snapshot.
- `Structured staged-config API`
  `/api/device/stage`, `/api/device/apply`, `/api/device/rollback`
  Bridge-side staging, validation, apply, and rollback discipline.

The App now prefers `/api/device/session` plus `/ws/events` when it is opened from the bridge. Raw `/ws` remains available both for compatibility and for the current live-control RPC lane.
For the App-side meaning of `Direct USB`, `Bridge session`, `Bridge raw`, and `Simulator`, see [App Transport Truth Table](../app/AppTransportTruthTable.md).

## Contract negotiation

Clients must read `GET /api/contract` before using the structured session API
or `/ws/events`. The current response is:

```json
{
  "contract": {
    "bridge_api_version": 1,
    "event_contract_version": 1,
    "bridge_version": "1.0.0",
    "bridge_source_sha": null,
    "supported_schema_versions": [9],
    "verified_apply": true,
    "structured_session": true
  }
}
```

`bridge_source_sha` comes from `MN42_BRIDGE_SOURCE_SHA` or `GITHUB_SHA` when
the launch/build environment supplies one; otherwise it is `null` rather than
claiming unknown provenance. The App accepts only API/event version `1`,
requires its current schema version to appear in `supported_schema_versions`,
and requires both advertised capabilities. A failed negotiation disables the
structured session lane; the existing raw Bridge transport remains the
compatibility fallback.

The unprefixed HTTP routes are the version-1 compatibility routes. A future
major contract may add version-prefixed routes, but version negotiation does
not require renaming the current surface. `/api/state`, `/api/device/session`,
and downloadable state snapshots also carry the same contract metadata so
diagnostics remain self-identifying.

## Structured event envelope

Every `/ws/events` frame is one JSON object with this shape:

```json
{
  "version": 1,
  "event": "device.ready",
  "at": "2026-05-24T12:00:00.000Z",
  "payload": {}
}
```

Rules:

- `version`
  Integer. Current value is `1`.
- `event`
  Stable event name string.
- `at`
  ISO-8601 timestamp generated by the bridge host.
- `payload`
  Object. Event-specific body.

## Event names

### `device.ready`

Emitted when the bridge has a complete cached device session: `HELLO`, manifest, schema, and config.

Payload:

```json
{
  "manifest": {},
  "schemaSource": "device",
  "firmwareIdentity": {},
  "powerSafety": {},
  "hardwareHealth": {}
}
```

### `device.telemetry`

Emitted when the bridge sees telemetry-like device frames.

Payload:

```json
{
  "telemetry": {},
  "traceId": "serial-abc",
  "hostTimestampMs": 123456,
  "sourceTimestampMs": 123455
}
```

`hostTimestampMs` is the Bridge's receipt time for the device frame. The App
propagates it as `observedTimestampMs` and uses the assembled frame's
`receivedAt` for musical visualization. It is host-observed arrival time, not
firmware-source time and not a latency-grade measurement.

### `device.config.live`

Payload:

```json
{
  "config": {},
  "deviceAuthority": "verified",
  "draftState": "clean",
  "clientApplyId": "browser-attempt-id",
  "stagedRevision": 12,
  "stagedDigest": "sha256...",
  "lastApplyResult": {}
}
```

### `device.config.staged`

Payload:

```json
{
  "config": {},
  "deviceAuthority": "verified",
  "draftState": "clean",
  "clientApplyId": "browser-attempt-id",
  "stagedRevision": 12,
  "stagedDigest": "sha256..."
}
```

### `device.config.dirty`

Payload:

```json
{
  "dirty": true,
  "deviceAuthority": "verified",
  "draftState": "dirty",
  "clientApplyId": "browser-attempt-id",
  "stagedRevision": 12,
  "stagedDigest": "sha256..."
}
```

### `device.apply.ack`

Payload:

```json
{
  "checksum": "sha256...",
  "seq": 7,
  "clientApplyId": "browser-attempt-id",
  "stagedRevision": 12,
  "stagedDigest": "sha256...",
  "appliedAt": "2026-05-24T12:00:01.000Z"
}
```

### `device.apply.pending`

Emitted when the dedicated serial Apply writer takes ownership, immediately
before it begins writing the captured candidate. This is the boundary between
App `preflighting` and `applying`.

Payload:

```json
{
  "checksum": "sha256...",
  "seq": 7,
  "clientApplyId": "browser-attempt-id",
  "stagedRevision": 12,
  "stagedDigest": "sha256...",
  "lastApplyResult": {
    "status": "pending"
  }
}
```

### `device.apply.rollback`

Payload:

```json
{
  "reason": "device_error",
  "lastApplyResult": {
    "status": "rollback",
    "reason": "device_error",
    "clientApplyId": "browser-attempt-id",
    "stagedRevision": 12,
    "stagedDigest": "sha256...",
    "deviceError": {}
  }
}
```

Receipt corruption such as `checksum_mismatch` does not prove rollback. It
enters `uncertain` and is resolved by authoritative readback.

### `bridge.alert`

Machine-readable warning/error surfaced by the bridge runtime itself.

Payload:

```json
{
  "code": "malformed_device_response",
  "severity": "warn",
  "message": "Device returned malformed JSON",
  "details": {}
}
```

### `bridge.performance`

Payload:

```json
{
  "performance": {}
}
```

## Session API

### Device config hydration and readback

The Bridge uses the bounded single-line `GET_CONFIG` response for initial
session hydration, authoritative Apply readback, and uncertain-outcome
resynchronization. It does not automatically select `GET_CONFIG_CHUNKED` from
the device capability flag: a live device may advertise that capability while
an incomplete chunk stream is still capable of occupying the serial lane and
hiding a later Apply ACK.

Chunked config reads remain an explicit device-session opt-in. When enabled,
an incomplete `GET_CONFIG_CHUNKED` handshake falls back once to `GET_CONFIG`
and emits a `bridge.alert` with code `chunked_config_fallback`. The normal
Bridge service keeps the opt-in disabled until the chunk stream is separately
verified on the target firmware and hardware.

### `GET /api/device/session`

Response:

```json
{
  "session": {
    "connected": true,
    "helloSeen": true,
    "ready": true,
    "schemaSource": "device",
    "manifest": {},
    "schema": {},
    "liveConfig": {},
    "stagedConfig": {},
    "dirty": false,
    "deviceAuthority": "verified",
    "draftState": "clean",
    "clientApplyId": "browser-attempt-id",
    "stagedRevision": 12,
    "stagedDigest": "sha256...",
    "sessionRevision": 34,
    "lastApplyResult": {},
    "powerSafety": {},
    "hardwareHealth": {},
    "firmwareIdentity": {},
    "lastError": null
  }
}
```

`hardwareHealth` mirrors the manifest-backed physical-board health fields when the firmware reports them: OLED presence
and driver status, brownout count, EEPROM primary/backup validity, last EEPROM load source, and memory headroom. Unknown
fields remain `null`; display degraded mode is not treated as a bridge-transport failure by itself.

`GET /api/device/session?warm=1` may be used before a device is connected to load the Bridge's bundled App schema
authority. That response reports `schemaSource: "bundled"` and supplies the schema, but does not invent a manifest, live
configuration, firmware identity, or `ready` session. Packaged-artifact smoke coverage uses this path to prove that every
App runtime dependency required for schema validation is self-contained; it is independent of a firmware build SHA.

### `POST /api/device/stage`

Request body:

```json
{
  "config": {},
  "expectedSessionRevision": 33,
  "clientApplyId": "browser-attempt-id",
  "stagedRevision": 12,
  "stagedDigest": "sha256..."
}
```

Success response:

```json
{
  "result": {
    "staged": {},
    "dirty": true,
    "sessionRevision": 34,
    "clientApplyId": "browser-attempt-id",
    "stagedRevision": 12,
    "stagedDigest": "sha256..."
  },
  "state": {}
}
```

Validation failure response:

```json
{
  "error": {
    "code": "schema_validation_failed",
    "message": "Staged config failed schema validation",
    "failureClass": "preflight-rejected",
    "details": {
      "errors": []
    }
  },
  "state": {}
}
```

### `POST /api/device/apply`

Request body:

```json
{
  "expectedSessionRevision": 34,
  "clientApplyId": "browser-attempt-id",
  "stagedRevision": 12,
  "stagedDigest": "sha256..."
}
```

Success response:

```json
{
  "result": {
    "applied": true,
    "checksum": "sha256...",
    "seq": 7
  },
  "state": {}
}
```

Possible error codes:

- `stale_session_revision`
- `staged_apply_identity_mismatch`
- `staged_digest_mismatch`
- `apply_in_progress`
- `device_not_connected`
- `device_not_ready`
- `schema_validation_failed`
- `apply_timeout`
- `apply_checksum_mismatch`
- `apply_transport_error`
- `device_<firmware error code>`

Structured stage/apply error bodies include a server-owned `failureClass`:

- `preflight-rejected`: serial Apply transmission did not begin; device
  authority remains verified and the browser draft may be corrected and retried.
- `device-rejected-before-commit`: firmware definitively rejected the correlated
  candidate and kept the previous device configuration.
- `transmission-unknown`: transmission may have begun, so the result must be
  treated as uncertain until authoritative readback resolves it.

Clients may infer a class from legacy error codes only when talking to an older
Bridge that omits `failureClass`.

### `POST /api/device/rollback`

Request body:

```json
{
  "reason": "operator_request"
}
```

Success response:

```json
{
  "result": {
    "rolledBack": true,
    "reason": "operator_request",
    "state": {}
  },
  "state": {}
}
```

## OSC telemetry mirrors

The bridge forwards firmware telemetry to OSC using stable legacy addresses plus richer scoped addresses for current
firmware packets.

| Firmware field / scope | OSC address |
| --- | --- |
| Slot values from `state_slots` or legacy `slots` | `/mn42/slots`, `/mn42/telemetry/slots` |
| Current slot from `state_slots` | `/mn42/current-slot`, `/mn42/telemetry/current-slot` |
| Envelope levels from `state_envelopes`, `scope_envelopes`, or legacy `envelopes` | `/mn42/envelopes`, `/mn42/telemetry/envelopes` |
| LFO values | `/mn42/lfos`, `/mn42/telemetry/lfos` |
| EF active flags | `/mn42/ef/status`, `/mn42/telemetry/ef-status` |
| LFO config array | `/mn42/lfo/config`, `/mn42/telemetry/lfo-config` as JSON string |
| ARG slot chunks | `/mn42/arg/slots`, `/mn42/telemetry/slot-args` as JSON string |
| Global ARG pair / enable / method | `/mn42/arg/pair`, `/mn42/arg/enabled`, `/mn42/arg/method` |
| Active profile | `/mn42/profile/active`, `/mn42/telemetry/active-profile` |
| Runtime diagnostics | `/mn42/diagnostics`, `/mn42/telemetry/diagnostics` as JSON string |
| Clock state | `/mn42/clock`, `/mn42/telemetry/clock` as JSON string |
| Note dynamics and jitter | `/mn42/note-dynamics`, `/mn42/jitter` as JSON string |

MIDI telemetry remains intentionally narrow: slot values are mirrored as channel 1 CCs and envelope values as channel 2
CCs. Richer machine state stays on OSC and the structured bridge event/session surfaces.

## Compatibility note

The raw `/ws` line transport remains intentionally unchanged for back-compat and deep debugging. The App-over-bridge path now prefers the structured session surfaces (`/api/device/*` plus `/ws/events`) and keeps raw `/ws` as a compatibility fallback plus the current live-control lane.
