bseverns/MOARkNOBS-42/docs/reference/SerialProtocol.md

# MN42 Line Protocol

> **Doc class:** Contract doc. This page mirrors the host-facing serial command and response contract for firmware.

This is the host-facing serial contract for MOARkNOBS-42 firmware. The transport is newline-delimited UTF-8 text over USB serial at `115200` baud. Commands are one line each. Responses are one JSON object per line unless the command is explicitly documented as a legacy text diagnostic.

## Transport Rules

| Rule | Contract |
| --- | --- |
| Line ending | Host sends `\n`; firmware trims whitespace before dispatch. |
| Command buffer  | Non-bulk command lines must fit `SERIAL_BUFFER_SIZE = 128` bytes including terminator. |
| Parser cadence  | Serial input polling and command queue dispatch run every `10 ms` by default from the mid-priority scheduler. |
| Hot-path policy | Timer ISR only drops a MIDI service token. JSON parsing, command dispatch, EEPROM writes, profile loads, and telemetry emission stay out of interrupt context. |
| Streaming gate  | Telemetry and config patch events are silent until `HELLO` sets `webSerialStreaming = true`. |
| Response format | Current commands return JSON. Deprecated commands may return `{"type":"response","message":"... deprecated"}` or no payload when logging is disabled. |
| Error format | Most validation errors return `{"type":"response","status":"error"}`. Bulk and JSON commands return `{"type":"error","code":"..."}`. Unknown commands log `Unknown command: <line>`. |

## Host Timeouts

These are host-side support boundaries used by the App runtime.

| Flow | Timeout |
| --- | ---: |
| Standard RPC, including `HELLO`, `GET_MANIFEST`, `GET_CONFIG`, `GET_SCHEMA` | `3000 ms` |
| Full apply via chunked `SET_ALL` | `30000 ms` |
| Profile macro commands | `6000 ms` |
| Scene commands | `6000 ms` |
| Native `SET_ALL` line pacing | `4 ms` between chunks |

## Chunking Rules

`SET_ALL` is the only intentionally chunked command. The App sends the final JSON frame in repeated lines:

```text
SET_ALL <chunk>
SET_ALL <chunk>
...
```

Firmware strips the `SET_ALL ` prefix and appends each chunk to `Utility::BulkConfigAssembler`.
An incomplete frame expires after five seconds even if no later command arrives. A host that
abandons an upload may release it immediately with `ABORT_SET_ALL`.

| Limit | Value |
| --- | ---: |
| App chunk payload | `96` bytes after `SET_ALL ` |
| Firmware bulk payload cap | `32768` bytes |
| Firmware completion rule  | One balanced top-level JSON object, respecting strings and escapes |
| Required bulk identity | `config_id` or `checksum` in the top-level frame |
| Incomplete-frame timeout  | `5000 ms` |
| Idempotency key |  `seq` plus `config_id`/`checksum`; duplicate last ACK is replayed |

Bulk frame shape:

```json
{
  "seq": 7,
  "config_id": "sha256-or-build-id",
  "config": {
    "slots": []
  }
}
```

Successful ACK:

```json
{
  "type": "ack",
  "checksum": "sha256-or-build-id",
  "seq": 7,
  "applied_checksum": "device-state-fnv1a",
  "storage_generation": 12
}
```

`applied_checksum` covers the applied semantic configuration, including each slot's ARG settings and both fixed LFO lanes. It changes when an LFO lane's enable state, mode, or signed amount changes; storage CRC fields and compiler padding are not part of the digest.

Bulk errors include `overflow`, `orphan`, `timeout`, `ingest`, `parse`, `checksum`, `config_missing`, `slots_missing`, `slots_size`, `slot_null`, `slot_type`, and `sysex_template`.

## Commands

| Command | Request | Response | Notes |
| --- | --- | --- | --- |
| `HELLO` | `HELLO` | `{"hello":"mn42"}` | Enables telemetry/config patch streaming. |
| `GET_MANIFEST` | `GET_MANIFEST` | Manifest JSON | See [Manifest Contract](ManifestContract.md). |
| `GET_DIAGNOSTICS` | `GET_DIAGNOSTICS` | Persistent or volatile diagnostics JSON | Black-box style boot/apply/error summary. Unknown fields must be tolerated. |
| `GET_SCHEMA` | `GET_SCHEMA` | JSON schema | Built by the protocol-owned `ConfigSchema` module. |
| `GET_CONFIG` | `GET_CONFIG` | Full config JSON | Includes pots, slots, EF routing, ARG, filter, LED state. |
| `GET_MOD_MATRIX` | `GET_MOD_MATRIX` | Current modulation routes and conflicts | Fixed-lane `last_value` follows the lane mode's polarity and scaling semantics.  |
| `GET_ARP` | `GET_ARP` | Live arpeggiator JSON | Includes the persisted `pattern_length` value. |
| `SET_ARP` | `SET_ARP,<ticks>,<shape>,<swing>,<gate>,<octave>[,<pattern>]` | Live arpeggiator JSON | Optional pattern length is clamped to `2..16`; five-value requests remain valid. |
| `GET_PROFILE` | `GET_PROFILE` or `GET_PROFILE,<id>` | Profile JSON | `id` is `0..3`; profile arp includes zero-based `assigned_slots`. |
| `SET_PROFILE` | `SET_PROFILE,<id>,<json>` | `{"type":"response","status":"ok"}` | Sparse profile patch; `arp.assigned_slots` replaces the hardware-toggle assignment set. Recall arms assignments but never starts notes. |
| `SAVE_PROFILE` | `SAVE_PROFILE,<id>` | `{"profile":<id>,"profile_saved":true}` | Saves live deck to profile `0..3`. |
| `LOAD_PROFILE` | `LOAD_PROFILE,<id>` | `{"profile":<id>,"profile_loaded":true}` | Loads profile `0..3`. Empty profiles get baseline defaults. |
| `RESET_PROFILE` | `RESET_PROFILE,<id>` | `{"profile":<id>,"profile_reset":true}` | Resets profile `0..3` to baseline. |
| `SAVE_MACRO_SLOT` | `SAVE_MACRO_SLOT` | `{"macro_saved":true,"macro_available":true}` | Stores current macro snapshot. |
| `RECALL_MACRO_SLOT` | `RECALL_MACRO_SLOT` | `{"macro_recalled":true,"macro_available":true}` | Restores stored macro snapshot. |
| `SET_ALL` | Chunked bulk JSON | ACK or bulk error | See chunking rules above. |
| `ABORT_SET_ALL` | `ABORT_SET_ALL` | `{"type":"response","status":"ok","command":"ABORT_SET_ALL","aborted":<bool>}` | Discards an incomplete bulk frame; safe and idempotent when no frame is active.  |
| `SET_SLOT_VALUE` | `SET_SLOT_VALUE,<slot>,<value>` | `{"type":"response","status":"ok"}` | Injects MIDI value `0..127` for slot `0..41`. |
| `SET_POT` | `SET_POT,<pot>,<channel>,<cc>` | OK or error JSON | `pot 0..41`, `channel 1..16`, `cc 0..127`. |
| `SET_LED` | `SET_LED,<brightness>,<r>,<g>,<b>` | OK or error JSON | Firmware clamps brightness to board profile cap. RGB fields are `0..255`. |
| `SET_EF` | `SET_EF,<slot>,<ef>` | OK or error JSON | Assigns slot to envelope follower. |
| `SET_EF_IDLE_FLOOR` | `SET_EF_IDLE_FLOOR,<value>` | `{"type":"response","status":"ok","command":"SET_EF_IDLE_FLOOR","idle_floor":<value>}` | Clamped `0..127`. |
| `SET_ARGMETHOD` | `SET_ARGMETHOD<method>` | OK or error JSON | Legacy parser reads from character offset 14; prefer bulk config for new tools.  |

| `ENTER_CONFIG_MODE` | `ENTER_CONFIG_MODE`                                           | `{"type":"response","status":"ok","command":"ENTER_CONFIG_MODE","rebooting":true}`     | Requests one-shot USB configurator boot then reboots outside unit tests.         |
| JSON `GET_SCENES`   | `{"cmd":"GET_SCENES"}`                                        | `{"cmd":"GET_SCENES","scenes":[...]}`                                                  | JSON scene commands short-circuit before legacy dispatch.                        |
| JSON `SAVE_SCENE`   | `{"cmd":"SAVE_SCENE","slot":0,"name":"Verse"}`                | Scene result JSON                                                                      | Scene slot range is firmware-defined by `SceneStorage::kSceneSlotCount`.         |
| JSON `RECALL_SCENE` | `{"cmd":"RECALL_SCENE","slot":0}`                             | Scene result JSON                                                                      | Applies stored scene if available.                                               |

In `GET_MOD_MATRIX`, an unshadowed persisted global `SlotValue` route reports
`mode: "legacy_replace"`: its mapped `0..127` result is the complete slot
output, independent of the physical pot baseline. A corresponding enabled
fixed lane reports that global route as `legacy_shadowed`.

The response also includes a `transport` object describing aggregate slot
admission: a `slot_token_bucket` with a 3-byte/ms DIN-derived refill, 15
initial and 64 maximum bytes, Note On priority, and `latest_per_slot`
continuous-value coalescing. Note Offs remain on their independent
high-priority release queue.

## Deprecated Commands

These remain accepted for older tools but should not be used for new App or Bridge work.

| Command | Current behavior |
| --- | --- |
| `GET_ALL` | Logs `GET_ALL deprecated, use GET_CONFIG` when serial logging is enabled. |
| `GET_ARGMETHOD` | Logs `get_arg_method deprecated`. |
| `GET_BROWNOUTS` | Logs `get_brownouts deprecated`. |
| `GET_EF` | Logs `get_ef deprecated` or error for invalid slot. |
| `GET_LED` | Logs `get_led deprecated` when serial logging is enabled. |
| `CAL_ENVS` | Calibrates all envelope followers and returns OK. |
| `GET_FILTER` | Logs `GET_FILTER deprecated`. |
| `SET_FILTER` | Seeds slot envelope payloads and returns OK. Prefer `SET_ALL`. |
| `GET_SLOT_FILTER` | Logs `GET_SLOT_FILTER deprecated` or error for invalid slot. |
| `SET_SLOT_FILTER` | Updates one slot filter payload and returns OK. Prefer `SET_ALL`. |
| `GET_ARGPAIR` | Logs `GET_ARGPAIR deprecated`. |
| `SET_ARGPAIR` | Updates global ARG enable/source pair and every slot ARG source. Prefer `SET_ALL`. |

## Telemetry

Telemetry starts after `HELLO` and runs from the low-priority scheduler while streaming is enabled. Scope frames run every `50 ms`; the larger state snapshot runs every `500 ms`.

Each state snapshot uses one shared `timestamp`, `timestampMs`, and `traceId`, then emits nine JSON lines:

| Scope | Contents | JSON document capacity |
| --- | --- | ---: |
| `state_slots` | 42 raw `slots`, 42 resolved `slotOutputs`, and `currentSlot` | `2048` bytes |
| `state_modulation_0_13` | Applied resolver contributions for slots 0-13 | `3072` bytes |
| `state_modulation_14_27` | Applied resolver contributions for slots 14-27 | `3072` bytes |
| `state_modulation_28_41` | Applied resolver contributions for slots 28-41 | `3072` bytes |
| `state_args_0_13` | ARG config for slots 0-13 | `2048` bytes |
| `state_args_14_27` | ARG config for slots 14-27 | `2048` bytes |
| `state_args_28_41` | ARG config for slots 28-41 | `2048` bytes |
| `state_diagnostics` | Global ARG settings and diagnostic counters | `768` bytes |
| `state_envelopes` | Six EF levels, two LFO values, EF active flags | `1024` bytes |

`slotContributions` contains only slots whose EF or LFO lane was applied in that control-rate frame. Each record is `{index, baseline, ef, lfos:[lfo1,lfo2], output, activeMask}`. Mask bits `1`, `2`, and `4` mean EF, LFO1, and LFO2 respectively. Deltas are measured after each ordered operation and clamp, so this invariant also holds for replace, scale, centered, and clipped modes:

```text
baseline + ef + lfos[0] + lfos[1] == output
```

These values describe the resolver result before MIDI transport token admission and coalescing. They are exact modulation-stage attribution, not a claim that every resolved sample was emitted on the wire. `slots` remains the raw mapped-pot baseline for compatibility; consumers that display the performed value should prefer `slotOutputs`.

Worst-case scheduled flow is two nine-line state snapshots plus twenty one-line scope snapshots per second. By JSON document capacity that is `38` lines/s and `64000` serialized bytes/s before USB framing. Typical payloads—especially sparse contribution chunks—are smaller.

Patch events are event-driven and separate from the 100 ms telemetry stream:

| Event | Trigger | Notes |
| --- | --- | --- |
| `slot_patch` plus legacy `config-patch` | Slot edit from hardware UI | Modern payload max document is `896` bytes. |
| `envelope_assignment` plus legacy `config-patch` | EF assignment changes | Compact assignment payload. |
| `filter_patch` plus legacy `config-patch` | Filter tuning changes | Compact filter payload. |
| `arg_patch` plus legacy `config-patch` | ARG method/source changes  | Compact ARG payload. |

## Examples

Handshake and manifest:

```text
> HELLO
< {"hello":"mn42"}
> GET_MANIFEST
< {"device_name":"MOARkNOBS-42","schema_version":9,"slot_count":42,"pot_count":42,"envelope_count":6,"arg_method_count":14,"led_count":52,"power_profile":"POWER_CHOKED_V1","led_brightness_cap":26,"rail_topology_verified":false}
```

Set one live value:

```text
> SET_SLOT_VALUE,2,77
< {"type":"response","status":"ok"}
```

Set LED color under the active board cap:

```text
> SET_LED,26,0,255,128
< {"type":"response","status":"ok"}
```

Save and recall a scene:

```text
> {"cmd":"SAVE_SCENE","slot":0,"name":"Verse"}
< {"cmd":"SAVE_SCENE","scene_saved":true,"scene_slot":0,"scene_name":"Verse","scene_available":true}
> {"cmd":"RECALL_SCENE","slot":0}
< {"cmd":"RECALL_SCENE","scene_slot":0,"scene_name":"Verse","scene_available":true,"scene_recalled":true}
```

Diagnostics snapshot:

```text
> GET_DIAGNOSTICS
< {"type":"diagnostics","storage_mode":"persistent","last_reset_reason_raw":3,"last_reset_reason_hex":"0x00000003","last_boot_mode":"standalone_runtime","last_config_load_source":"primary","last_config_apply_status":"acked","last_config_apply_checksum":"abc123","last_protocol_error_code":"checksum","brownout_count":0,"display_init_failures":1,"max_loop_overrun_us":3100,"watchdog_reset_marker_available":false}
```

`GET_DIAGNOSTICS` is intentionally additive. Bridge/App consumers should ignore unknown fields until they explicitly adopt a richer diagnostics UI.
