bseverns/MOARkNOBS-42/docs/project/lineage.md

# Lineage: Computer-Vision & Control Sketches → MOARkNOBS-42

- 2019–2021 — Attention & parallax tests (rolling shutter, wheel-mount; DS200801).
- 2021 — Signal/noise overlays (ds10.mov series).
- 2022 — Interface and kiosk UX prototypes (consent gates, overlay UX).
- 2023–2024 — Arduino/MCU controller studies; mapping curves and rate-limit patterns.
- 2025 — **MOARkNOBS-42**: critical instrument; reproducible hardware + firmware; parameter-map formalized.

Each step logs apparatus, thresholds, failure cases, and “what changed.”
