bseverns/MOARkNOBS-42/docs/sketchbook/index.md

# Sketchbook Index

This folder aggregates notes, scans, and short clips that informed **MOARkNOBS-42**.

- **2025-09-13** — Placeholder: add latest bench notes, wiring tweaks, and mapping decisions.
- 2025-09-05 — Backlight miss & overlay latency (faceTimes lineage).
- 2024-05-03 — Encoder acceleration experiments.
- 2023-11-12 — Accidental parallax and rolling-shutter tests.

> Tip: keep one entry per change with apparatus, variables, observation, decision, and assets.
