bseverns/MOARkNOBS-42/docs/bench/firmware/TEMPLATE_modulation-matrix-summary.md

# Modulation Matrix Bench Summary

- Date:
- Commit:
- Firmware env:
- Board revision:
- Serial port:

## GET_MOD_MATRIX Result

- Command/type observed:
- Contract version:
- Sources reported:
- Limits reported:
- JSON parse status:

## Route Fixture Used

- Active slots:
- EF mappings:
- LFO routes:
- Expected destinations:

## Conflict Cases Tested

- Shared MIDI CC writers:
- Shared slot-value writers:
- Other collisions checked:

## App And Bridge Compatibility Notes

- Configurator App behavior:
- Bridge behavior:
- Any contract mismatches:

## Caveats

- Hardware anomalies:
- Truncation or overflow notes:
- Follow-up evidence needed:
