bseverns/MOARkNOBS-42/docs/bench/bridge/TEMPLATE_bridge-session-summary.md

# Bridge Bench Summary: Structured Session

Date: unknown/not captured
Commit: unknown/not captured
Firmware git_sha: unknown/not captured
Firmware version: unknown/not captured
Schema version: unknown/not captured
Board revision: unknown/not captured
Board rework state: unknown/not captured
Serial port: unknown/not captured
Host: unknown/not captured
Node: unknown/not captured
Bridge mode: source
Firmware env: unknown/not captured
Runner: firmware/system_test/mn42_bridge_session_runner.js
Artifact / report path: unknown/not captured

## Result

PASS or FAIL

## Proven

- Replace with the exact hardware/runtime facts this run proved.

## Caveats

- Replace with any board, host, packaging, or evidence limits that still apply.

## PASS output

```text
Paste the exact runner output here.
```
