bseverns/MOARkNOBS-42/docs/bench/bridge/TEMPLATE_packaged-console-hil-summary.md

# Bridge Bench Summary: Packaged Console HIL

Date: unknown/not captured
Commit: unknown/not captured
Firmware git_sha: unknown/not captured
Firmware version: unknown/not captured
Schema version: unknown/not captured
Board revision: unknown/not captured
Board rework state: unknown/not captured
Serial port: unknown/not captured
Host: unknown/not captured
Node: unknown/not captured
Bridge mode: packaged
Packaged artifact: unknown/not captured
Package platform: unknown/not captured
Signing state: unknown/not captured
Firmware env: unknown/not captured
Runner: unknown/not captured
Artifact / report path: unknown/not captured

## Result

PASS or FAIL

## Proven

- Replace with the exact packaged-console behavior this run proved.

## Caveats

- State whether the artifact was unsigned and do not imply public-installer readiness without separate evidence.
- Replace with any board, host, or runtime limits that still apply.

## PASS output

```text
Paste the exact runner output here.
```
