bseverns/MOARkNOBS-42/docs/bench/firmware/0526_boot-contract-summary.md

## Result

PASS with hardware caveats.

Historical note: this receipt predates the newer structured display diagnostics now exposed by `GET_MANIFEST` and WebSerial telemetry. The raw boot output below is preserved as captured.

## Proven

- Production firmware starts in standalone_runtime.
- ENTER_CONFIG_MODE command is accepted.
- Device reboots into usb_configurator.
- HELLO, GET_MANIFEST, GET_SCHEMA, GET_CONFIG succeed.
- SET_ALL chunked apply returns checksum ACK.
- GET_CONFIG readback confirms applied mutation.

## Observed warnings

- Historical standalone-boot warning: `{"warning":"display_init_failed"}`.

## Caveats

- Manifest reported SPLIT_RAIL_REWORK / rail_topology_verified=true, but current Rev A hardware inspection suggests the LED fuse branch is downstream of the 0.5 A fuse.
- Current firmware now reports display degraded mode with explicit `display_present`, `display_ok`, `display_init_failures`, and `display_status` fields. This historical receipt does not include those manifest fields because it was captured before that contract update.
- Existing config contained UNKNOWN/255 slot values before apply; SET_ALL path normalized many of these to OFF/channel 16/data1 127.

[boot-contract:host] HELLO
[boot-contract:serial] 0729D7500100B200420002
[boot-contract:serial] Reset 0x00000001 Brownouts 0
[boot-contract:serial] {"type":"boot*mode","mode":"standalone_runtime"}
[boot-contract:serial] {"warning":"display_init_failed"}
[boot-contract:serial] {"type":"info","message":"Loading potentiometer settings from EEPROM..."}
[boot-contract:serial] {"hello":"mn42"}
[boot-contract:host] ENTER_CONFIG_MODE
[boot-contract:serial] {"type":"response","status":"ok","command":"ENTER_CONFIG_MODE","rebooting":true}
[boot-contract:serial] MN42 FW 0.0.0 8113ff6
[boot-contract:serial] MN42 FW 0.0.0 schema 0006 UID 6D5C45542C0729D7500100B200420002
[boot-contract:serial] Reset 0x00000003 Brownouts 0
[boot-contract:serial] {"type":"boot_mode","mode":"usb_configurator"}
[boot-contract:host] HELLO
[boot-contract:serial] {"hello":"mn42"}
[boot-contract:host] GET_MANIFEST
[boot-contract:serial] {"device_name":"MOARkNOBS-42","fw_version":"0.0.0","git_sha":"8113ff6","build_time":"May 25 2026 18:06:23","schema_version":6,"slot_count":42,"pot_count":42,"envelope_count":6,"arg_method_count":14,"led_count":52,"power_profile":"SPLIT_RAIL_REWORK","led_brightness_cap":255,"rail_topology_verified":true,"free_ram":17212,"free_flash":1660928,"brownout_count":0,"eeprom_primary_valid":true,"eeprom_backup_valid":true,"eeprom_last_load":"unknown","capabilities":{"profile_save":true,"profile_load":true,"profile_reset":true,"macro_snapshot":true,"scenes":true,"clock_live":true,"note_dynamics_live":true,"jitter_live":true,"usb_midi_toggle":true,"device_schema":true,"bulk_config":true,"one_shot_config_boot":true},"host_roles":{"configurator":"convenience","bridge":"transport_required"}}
[boot-contract:host] GET_SCHEMA
[boot-contract:serial] {"$schema":"https://json-schema.org/draft/2020-12/schema","schema_version":6,"title":"MOARkNOBS Runtime Configuration","type":"object","x_mn42":{"authority":"device","configurator":"convenience editor for staged user input","bridge":"required when USB/WebSerial transport is unavailable or host integration needs it"},"required":["slots","efSlots","filter","arg","led"],"properties":{"slots":{"type":"array","title":"Slot Configuration","description":"Primary knob-to-MIDI mapping for each slot.","minItems":42,"maxItems":42,"items":{"type":"object","required":["type","midiChannel","data1","efIndex","active"],"properties":{"type":{"type":"string","title":"Knob -> MIDI message","enum":["OFF","CC","Note","PitchBend","ProgramChange","Aftertouch","ModWheel","NRPN","RPN","SysEx"]},"midiChannel":{"type":"integer","title":"MIDI channel","minimum":1,"maximum":16},"data1":{"type":"integer","title":"CC/Note number","minimum":0,"maximum":127},"arpNote":{"type":"integer","title":"Arp root note","minimum":0,"maximum":127},"efIndex":{"type":"integer","title":"Envelope follower index","minimum":-1,"maximum":5},"ef":{"type":"object","title":"Envelope Follower (EF)","required":["index","filter_index","filter_name","frequency","q","oversample","smoothing","baseline","gain"],"properties":{"index":{"type":"integer","minimum":-1,"maximum":5},"filter_index":{"type":"integer","minimum":0,"maximum":6},"filter_name":{"type":"string","enum":["LINEAR","OPPOSITE_LINEAR","EXPONENTIAL","RANDOM","LOWPASS","HIGHPASS","BANDPASS"]},"frequency":{"type":"number","minimum":20.0,"maximum":5000.0},"q":{"type":"number","minimum":0.50,"maximum":4.0},"oversample":{"type":"integer","minimum":1,"maximum":32},"smoothing":{"type":"number","minimum":0,"maximum":1},"baseline":{"type":"number"},"gain":{"type":"number"},"mode":{"type":"integer","minimum":0,"maximum":3},"autoBaseline":{"type":"boolean"},"autoGain":{"type":"boolean"},"attackMs":{"type":"integer","minimum":1,"maximum":60000},"releaseMs":{"type":"integer","minimum":1,"maximum":60000},"rmsWindowMs":{"type":"integer","minimum":1,"maximum":60000},"baselineTauMs":{"type":"integer","minimum":1,"maximum":60000},"gainTauMs":{"type":"integer","minimum":1,"maximum":60000},"gateThreshold":{"type":"integer","minimum":0,"maximum":127},"gateHysteresis":{"type":"integer","minimum":0,"maximum":127},"activityThreshold":{"type":"integer","minimum":0,"maximum":127},"gainTarget":{"type":"integer","minimum":0,"maximum":127}},"additionalProperties":false},"active":{"type":"boolean","title":"Enabled"},"sysexTemplate":{"type":"string","title":"SysEx template","maxLength":128},"arg":{"type":"object","title":"Follower Combiner (ARG)","required":["enabled","method","method_name","sourceA","sourceB"],"properties":{"enabled":{"type":"boolean"},"method":{"type":"integer","minimum":0,"maximum":13},"method_name":{"type":"string","enum":["PLUS","MIN","PECK","SHAV","SQAR","BABS","TABS","MULT","DIVI","AVG","XABS","MAXX","MINN","XORR"]},"sourceA":{"type":"integer","minimum":0,"maximum":5},"sourceB":{"type":"integer","minimum":0,"maximum":5}},"additionalProperties":false}},"additionalProperties":false}},"efSlots":{"type":"array","title":"Envelope Assignments","minItems":6,"maxItems":6,"items":{"type":"object","properties":{"slot":{"type":"integer","minimum":-1,"maximum":41},"slots":{"type":"array","items":{"type":"integer","minimum":0,"maximum":41},"uniqueItems":true}},"anyOf":[{"required":["slot"]},{"required":["slots"]}],"additionalProperties":false}},"filter":{"type":"object","title":"Follower Filter","required":["type","freq","q"],"properties":{"type":{"type":"string","enum":["LINEAR","OPPOSITE_LINEAR","EXPONENTIAL","RANDOM","LOWPASS","HIGHPASS","BANDPASS"]},"freq":{"type":"number","minimum":20.0,"maximum":5000.0},"q":{"type":"number","minimum":0.50,"maximum":4.0},"idle_floor":{"type":"integer","title":"EF idle floor","description":"Envelope levels at or below this MIDI value are clamped to zero.","minimum":0,"maximum":127,"default":24}},"additionalProperties":false},"arg":{"type":"object","title":"Follower Combiner (ARG)","required":["method","a","b"],"properties":{"method":{"type":"string","enum":["PLUS","MIN","PECK","SHAV","SQAR","BABS","TABS","MULT","DIVI","AVG","XABS","MAXX","MINN","XORR"]},"a":{"type":"number","minimum":0,"maximum":5},"b":{"type":"number","minimum":0,"maximum":5},"enable":{"type":"boolean"}},"additionalProperties":false},"led":{"type":"object","title":"LED Colors","required":["brightness","color"],"properties":{"brightness":{"type":"integer","minimum":0,"maximum":255},"color":{"type":"string","pattern":"^#([0-9a-fA-F]{6})$"},"mode":{"type":"string","enum":["STATIC","PEAK_HOLD","TRAIL","CLOCK_PULSE"],"default":"STATIC"}},"additionalProperties":false},"envelopeMode":{"type":"string","enum":["LINEAR","EXPONENTIAL","LOG"],"default":"LINEAR"}},"additionalProperties":false}
[boot-contract:host] GET_CONFIG
[boot-contract:serial] {"fw_version":"0.0.0","schema_version":6,"pots":[{"index":0,"channel":0,"cc":0},{"index":1,"channel":0,"cc":0},{"index":2,"channel":0,"cc":0},{"index":3,"channel":0,"cc":0},{"index":4,"channel":0,"cc":0},{"index":5,"channel":0,"cc":0},{"index":6,"channel":0,"cc":0},{"index":7,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
[boot-contract:host] SET_ALL {"seq":1,"checksum":"4c7d241eb7217d3c96d25692583cc9ede41cce1577a0118caa46b27688300269","config":
[boot-contract:host] SET_ALL {"slots":[{"type":"OFF","channel":1,"data1":48,"arpNote":87,"active":true,"ef_index":0},{"type":
[boot-contract:host] SET_ALL "CC","channel":2,"data1":3,"arpNote":0,"active":true,"ef_index":1},{"type":"CC","channel":3,"dat
[boot-contract:host] SET_ALL a1":6,"arpNote":0,"active":true,"ef_index":2},{"type":"CC","channel":4,"data1":9,"arpNote":0,"ac
[boot-contract:host] SET_ALL tive":true,"ef_index":3},{"type":"OFF","channel":5,"data1":52,"arpNote":126,"active":true,"ef_in
[boot-contract:host] SET_ALL dex":4},{"type":"CC","channel":1,"data1":15,"arpNote":0,"active":true,"ef_index":5},{"type":"CC"
[boot-contract:host] SET_ALL ,"channel":2,"data1":18,"arpNote":126,"active":true,"ef_index":0},{"type":"CC","channel":3,"data
[boot-contract:host] SET_ALL 1":21,"arpNote":0,"active":true,"ef_index":1},{"type":"OFF","channel":4,"data1":56,"arpNote":56,
[boot-contract:host] SET_ALL "active":true,"ef_index":-1},{"type":"OFF","channel":16,"data1":127,"arpNote":127,"active":true,
[boot-contract:host] SET_ALL "ef_index":-1},{"type":"OFF","channel":16,"data1":127,"arpNote":127,"active":true,"ef_index":-1}
[boot-contract:host] SET_ALL ,{"type":"OFF","channel":16,"data1":127,"arpNote":127,"active":true,"ef_index":-1},{"type":"OFF"
[boot-contract:host] SET_ALL ,"channel":16,"data1":127,"arpNote":127,"active":true,"ef_index":-1},{"type":"OFF","channel":16,
[boot-contract:host] SET_ALL "data1":127,"arpNote":127,"active":true,"ef_index":-1},{"type":"OFF","channel":16,"data1":127,"a
[boot-contract:host] SET_ALL rpNote":127,"active":true,"ef_index":-1},{"type":"OFF","channel":16,"data1":127,"arpNote":127,"a
[boot-contract:host] SET_ALL ctive":true,"ef_index":-1},{"type":"OFF","channel":16,"data1":127,"arpNote":127,"active":true,"e
[boot-contract:host] SET_ALL f_index":-1},{"type":"OFF","channel":16,"data1":127,"arpNote":127,"active":true,"ef_index":-1},{
[boot-contract:host] SET_ALL "type":"OFF","channel":16,"data1":127,"arpNote":127,"active":true,"ef_index":-1},{"type":"OFF","
[boot-contract:host] SET_ALL channel":16,"data1":127,"arpNote":127,"active":true,"ef_index":-1},{"type":"OFF","channel":16,"d
[boot-contract:host] SET_ALL ata1":127,"arpNote":127,"active":true,"ef_index":-1},{"type":"OFF","channel":16,"data1":127,"arp
[boot-contract:host] SET_ALL Note":127,"active":true,"ef_index":-1},{"type":"OFF","channel":16,"data1":127,"arpNote":127,"act
[boot-contract:host] SET_ALL ive":true,"ef_index":-1},{"type":"OFF","channel":16,"data1":127,"arpNote":127,"active":true,"ef*
[boot-contract:host] SET*ALL index":-1},{"type":"OFF","channel":16,"data1":127,"arpNote":127,"active":true,"ef_index":-1},{"t
[boot-contract:host] SET_ALL ype":"OFF","channel":16,"data1":127,"arpNote":127,"active":true,"ef_index":-1},{"type":"OFF","ch
[boot-contract:host] SET_ALL annel":16,"data1":127,"arpNote":127,"active":true,"ef_index":-1},{"type":"OFF","channel":16,"dat
[boot-contract:host] SET_ALL a1":127,"arpNote":127,"active":true,"ef_index":-1},{"type":"OFF","channel":16,"data1":127,"arpNo
[boot-contract:host] SET_ALL te":127,"active":true,"ef_index":-1},{"type":"OFF","channel":16,"data1":127,"arpNote":127,"activ
[boot-contract:host] SET_ALL e":true,"ef_index":-1},{"type":"OFF","channel":16,"data1":127,"arpNote":127,"active":true,"ef_in
[boot-contract:host] SET_ALL dex":-1},{"type":"OFF","channel":16,"data1":127,"arpNote":127,"active":true,"ef_index":-1},{"typ
[boot-contract:host] SET_ALL e":"OFF","channel":16,"data1":127,"arpNote":127,"active":true,"ef_index":-1},{"type":"OFF","chan
[boot-contract:host] SET_ALL nel":16,"data1":127,"arpNote":127,"active":true,"ef_index":-1},{"type":"OFF","channel":16,"data1
[boot-contract:host] SET_ALL ":127,"arpNote":127,"active":true,"ef_index":-1},{"type":"OFF","channel":16,"data1":127,"arpNote
[boot-contract:host] SET_ALL ":127,"active":true,"ef_index":-1},{"type":"OFF","channel":16,"data1":127,"arpNote":127,"active"
[boot-contract:host] SET_ALL :true,"ef_index":-1},{"type":"OFF","channel":16,"data1":127,"arpNote":127,"active":true,"ef_inde
[boot-contract:host] SET_ALL x":-1},{"type":"OFF","channel":16,"data1":127,"arpNote":127,"active":true,"ef_index":-1},{"type"
[boot-contract:host] SET_ALL :"OFF","channel":16,"data1":127,"arpNote":127,"active":true,"ef_index":-1},{"type":"OFF","channe
[boot-contract:host] SET_ALL l":16,"data1":127,"arpNote":127,"active":true,"ef_index":-1},{"type":"OFF","channel":16,"data1":
[boot-contract:host] SET_ALL 127,"arpNote":127,"active":true,"ef_index":-1}],"filter":{"freq":20,"q":0.5,"idle_floor":25,"typ
[boot-contract:host] SET_ALL e":"LINEAR"}}}
[boot-contract:serial] {"type":"ack","seq":1,"checksum":"4c7d241eb7217d3c96d25692583cc9ede41cce1577a0118caa46b27688300269"}
[boot-contract:host] GET_CONFIG
[boot-contract:serial] {"fw_version":"0.0.0","schema_version":6,"pots":[{"index":0,"channel":1,"cc":48},{"index":1,"channel":2,"cc":3},{"index":2,"channel":3,"cc":6},{"index":3,"channel":4,"cc":9},{"index":4,"channel":5,"cc":52},{"index":5,"channel":1,"cc":15},{"index":6,"channel":2,"cc":18},{"index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
[boot-contract:host] SET_ALL {"seq":2,"checksum":"54ec8994d5f543bfc68ed61966c7e8a9328aab0b2bae762d8d5fdf3ecbf3626f","config":
[boot-contract:host] SET_ALL {"slots":[{"type":"OFF","channel":1,"data1":48,"arpNote":87,"active":true,"ef_index":0,"ef":{"in
[boot-contract:host] SET_ALL dex":0,"filter_index":5,"filter_name":"HIGHPASS","frequency":1680,"q":1.100000024,"oversample":4
[boot-contract:host] SET_ALL ,"smoothing":0.200000003,"baseline":0,"gain":8,"mode":0,"autoBaseline":true,"autoGain":true,"att
[boot-contract:host] SET_ALL ackMs":5,"releaseMs":20,"rmsWindowMs":50,"baselineTauMs":2000,"gainTauMs":3000,"gateThreshold":1
[boot-contract:host] SET_ALL 6,"gateHysteresis":4,"activityThreshold":4,"gainTarget":102}},{"type":"CC","channel":2,"data1":3
[boot-contract:host] SET_ALL ,"arpNote":0,"active":true,"ef_index":1,"ef":{"index":1,"filter_index":5,"filter_name":"HIGHPASS
[boot-contract:host] SET_ALL ","frequency":1680,"q":1.100000024,"oversample":4,"smoothing":0.200000003,"baseline":0,"gain":1,
[boot-contract:host] SET_ALL "mode":0,"autoBaseline":true,"autoGain":true,"attackMs":5,"releaseMs":20,"rmsWindowMs":50,"basel
[boot-contract:host] SET_ALL ineTauMs":2000,"gainTauMs":3000,"gateThreshold":16,"gateHysteresis":4,"activityThreshold":4,"gai
[boot-contract:host] SET_ALL nTarget":102}},{"type":"CC","channel":3,"data1":6,"arpNote":0,"active":true,"ef_index":2,"ef":{"
[boot-contract:host] SET_ALL index":2,"filter_index":5,"filter_name":"HIGHPASS","frequency":1680,"q":1.100000024,"oversample"
[boot-contract:host] SET_ALL :4,"smoothing":0.200000003,"baseline":0,"gain":1,"mode":0,"autoBaseline":true,"autoGain":true,"a
[boot-contract:host] SET_ALL ttackMs":5,"releaseMs":20,"rmsWindowMs":50,"baselineTauMs":2000,"gainTauMs":3000,"gateThreshold"
[boot-contract:host] SET_ALL :16,"gateHysteresis":4,"activityThreshold":4,"gainTarget":102}},{"type":"CC","channel":4,"data1"
[boot-contract:host] SET_ALL :9,"arpNote":0,"active":true,"ef_index":3,"ef":{"index":3,"filter_index":5,"filter_name":"HIGHPA
[boot-contract:host] SET_ALL SS","frequency":1680,"q":1.100000024,"oversample":4,"smoothing":0.200000003,"baseline":0,"gain":
[boot-contract:host] SET_ALL 1,"mode":0,"autoBaseline":true,"autoGain":true,"attackMs":5,"releaseMs":20,"rmsWindowMs":50,"bas
[boot-contract:host] SET_ALL elineTauMs":2000,"gainTauMs":3000,"gateThreshold":16,"gateHysteresis":4,"activityThreshold":4,"g
[boot-contract:host] SET_ALL ainTarget":102}},{"type":"OFF","channel":5,"data1":52,"arpNote":126,"active":true,"ef_index":4,"
[boot-contract:host] SET_ALL ef":{"index":4,"filter_index":5,"filter_name":"HIGHPASS","frequency":1680,"q":1.100000024,"overs
[boot-contract:host] SET_ALL ample":4,"smoothing":0.200000003,"baseline":0,"gain":1,"mode":0,"autoBaseline":true,"autoGain":t
[boot-contract:host] SET_ALL rue,"attackMs":5,"releaseMs":20,"rmsWindowMs":50,"baselineTauMs":2000,"gainTauMs":3000,"gateThre
[boot-contract:host] SET_ALL shold":16,"gateHysteresis":4,"activityThreshold":4,"gainTarget":102}},{"type":"CC","channel":1,"
[boot-contract:host] SET_ALL data1":15,"arpNote":0,"active":true,"ef_index":5,"ef":{"index":5,"filter_index":5,"filter_name":
[boot-contract:host] SET_ALL "HIGHPASS","frequency":1680,"q":1.100000024,"oversample":4,"smoothing":0.200000003,"baseline":0,
[boot-contract:host] SET_ALL "gain":1,"mode":0,"autoBaseline":true,"autoGain":true,"attackMs":5,"releaseMs":20,"rmsWindowMs":
[boot-contract:host] SET_ALL 50,"baselineTauMs":2000,"gainTauMs":3000,"gateThreshold":16,"gateHysteresis":4,"activityThreshol
[boot-contract:host] SET_ALL d":4,"gainTarget":102}},{"type":"CC","channel":2,"data1":18,"arpNote":126,"active":true,"ef_inde
[boot-contract:host] SET_ALL x":0,"ef":{"index":0,"filter_index":5,"filter_name":"HIGHPASS","frequency":1680,"q":1.100000024,
[boot-contract:host] SET_ALL "oversample":4,"smoothing":0.200000003,"baseline":0,"gain":1,"mode":0,"autoBaseline":true,"autoG
[boot-contract:host] SET_ALL ain":true,"attackMs":5,"releaseMs":20,"rmsWindowMs":50,"baselineTauMs":2000,"gainTauMs":3000,"ga
[boot-contract:host] SET_ALL teThreshold":16,"gateHysteresis":4,"activityThreshold":4,"gainTarget":102}},{"type":"CC","channe
[boot-contract:host] SET_ALL l":3,"data1":21,"arpNote":0,"active":true,"ef_index":1,"ef":{"index":1,"filter_index":5,"filter*
[boot-contract:host] SET*ALL name":"HIGHPASS","frequency":1680,"q":1.100000024,"oversample":4,"smoothing":0.200000003,"baseli
[boot-contract:host] SET_ALL ne":0,"gain":1,"mode":0,"autoBaseline":true,"autoGain":true,"attackMs":5,"releaseMs":20,"rmsWind
[boot-contract:host] SET_ALL owMs":50,"baselineTauMs":2000,"gainTauMs":3000,"gateThreshold":16,"gateHysteresis":4,"activityTh
[boot-contract:host] SET_ALL reshold":4,"gainTarget":102}},{"type":"OFF","channel":4,"data1":56,"arpNote":56,"active":true,"e
[boot-contract:host] SET_ALL f_index":-1},{"type":"OFF","channel":16,"data1":127,"arpNote":127,"active":true,"ef_index":-1},{
[boot-contract:host] SET_ALL "type":"OFF","channel":16,"data1":127,"arpNote":127,"active":true,"ef_index":-1},{"type":"OFF","
[boot-contract:host] SET_ALL channel":16,"data1":127,"arpNote":127,"active":true,"ef_index":-1},{"type":"OFF","channel":16,"d
[boot-contract:host] SET_ALL ata1":127,"arpNote":127,"active":true,"ef_index":-1},{"type":"OFF","channel":16,"data1":127,"arp
[boot-contract:host] SET_ALL Note":127,"active":true,"ef_index":-1},{"type":"OFF","channel":16,"data1":127,"arpNote":127,"act
[boot-contract:host] SET_ALL ive":true,"ef_index":-1},{"type":"OFF","channel":16,"data1":127,"arpNote":127,"active":true,"ef*
[boot-contract:host] SET_ALL index":-1},{"type":"OFF","channel":16,"data1":127,"arpNote":127,"active":true,"ef_index":-1},{"t
[boot-contract:host] SET_ALL ype":"OFF","channel":16,"data1":127,"arpNote":127,"active":true,"ef_index":-1},{"type":"OFF","ch
[boot-contract:host] SET_ALL annel":16,"data1":127,"arpNote":127,"active":true,"ef_index":-1},{"type":"OFF","channel":16,"dat
[boot-contract:host] SET_ALL a1":127,"arpNote":127,"active":true,"ef_index":-1},{"type":"OFF","channel":16,"data1":127,"arpNo
[boot-contract:host] SET_ALL te":127,"active":true,"ef_index":-1},{"type":"OFF","channel":16,"data1":127,"arpNote":127,"activ
[boot-contract:host] SET_ALL e":true,"ef_index":-1},{"type":"OFF","channel":16,"data1":127,"arpNote":127,"active":true,"ef_in
[boot-contract:host] SET_ALL dex":-1},{"type":"OFF","channel":16,"data1":127,"arpNote":127,"active":true,"ef_index":-1},{"typ
[boot-contract:host] SET_ALL e":"OFF","channel":16,"data1":127,"arpNote":127,"active":true,"ef_index":-1},{"type":"OFF","chan
[boot-contract:host] SET_ALL nel":16,"data1":127,"arpNote":127,"active":true,"ef_index":-1},{"type":"OFF","channel":16,"data1
[boot-contract:host] SET_ALL ":127,"arpNote":127,"active":true,"ef_index":-1},{"type":"OFF","channel":16,"data1":127,"arpNote
[boot-contract:host] SET_ALL ":127,"active":true,"ef_index":-1},{"type":"OFF","channel":16,"data1":127,"arpNote":127,"active"
[boot-contract:host] SET_ALL :true,"ef_index":-1},{"type":"OFF","channel":16,"data1":127,"arpNote":127,"active":true,"ef_inde
[boot-contract:host] SET_ALL x":-1},{"type":"OFF","channel":16,"data1":127,"arpNote":127,"active":true,"ef_index":-1},{"type"
[boot-contract:host] SET_ALL :"OFF","channel":16,"data1":127,"arpNote":127,"active":true,"ef_index":-1},{"type":"OFF","channe
[boot-contract:host] SET_ALL l":16,"data1":127,"arpNote":127,"active":true,"ef_index":-1},{"type":"OFF","channel":16,"data1":
[boot-contract:host] SET_ALL 127,"arpNote":127,"active":true,"ef_index":-1},{"type":"OFF","channel":16,"data1":127,"arpNote":
[boot-contract:host] SET_ALL 127,"active":true,"ef_index":-1},{"type":"OFF","channel":16,"data1":127,"arpNote":127,"active":t
[boot-contract:host] SET_ALL rue,"ef_index":-1},{"type":"OFF","channel":16,"data1":127,"arpNote":127,"active":true,"ef_index"
[boot-contract:host] SET_ALL :-1},{"type":"OFF","channel":16,"data1":127,"arpNote":127,"active":true,"ef_index":-1},{"type":"
[boot-contract:host] SET_ALL OFF","channel":16,"data1":127,"arpNote":127,"active":true,"ef_index":-1},{"type":"OFF","channel"
[boot-contract:host] SET_ALL :16,"data1":127,"arpNote":127,"active":true,"ef_index":-1},{"type":"OFF","channel":16,"data1":12
[boot-contract:host] SET_ALL 7,"arpNote":127,"active":true,"ef_index":-1},{"type":"OFF","channel":16,"data1":127,"arpNote":12
[boot-contract:host] SET_ALL 7,"active":true,"ef_index":-1}],"filter":{"freq":20,"q":0.5,"idle_floor":24,"type":"LINEAR"}}}
[boot-contract:serial] {"type":"ack","seq":2,"checksum":"54ec8994d5f543bfc68ed61966c7e8a9328aab0b2bae762d8d5fdf3ecbf3626f"}
[boot-contract:host] GET_CONFIG
[boot-contract:serial] {"fw_version":"0.0.0","schema_version":6,"pots":[{"index":0,"channel":1,"cc":48},{"index":1,"channel":2,"cc":3},{"index":2,"channel":3,"cc":6},{"index":3,"channel":4,"cc":9},{"index":4,"channel":5,"cc":52},{"index":5,"channel":1,"cc":15},{"index":6,"channel":2,"cc":18},{"index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
