bseverns/MOARkNOBS-42/docs/sketch/systemFlow/hw/led&midiOut.md

One AHCT245 channel kicks 3 V3 logic up to 5 V for a rowdy WS2812B LED strip, while another shoves MIDI bits out both a DIN jack and a 1/8" TRS Type‑A socket.
Teensy pin 6 drives the LED chain; pin 1 handles MIDI through a 220 Ω resistor.
The AHCT245 wants 5 V on VCC—starve it and your colors go full anarchy.

**References**

- [LED schematic](../../MainLEDPool.png)
- [MIDI schematic](../../MIDI.png)
- [74AHCT245 datasheet](https://www.ti.com/lit/ds/symlink/sn74ahct245.pdf)
- [WS2812B datasheet](https://cdn-shop.adafruit.com/datasheets/WS2812B.pdf)
- Snapshots [MainLEDPool.png](../../MainLEDPool.png) and [MIDI.png](../../MIDI.png)

Tiny but mighty LED drivers and MIDI outlines! The related schematic snapshots live in [MainLEDPool.png](../../MainLEDPool.png) and [MIDI.png](../../MIDI.png).

```mermaid
flowchart LR
  subgraph LevelShiftLED["Level-Shift & LED Out"]
    U1[Teensy 4.0] -->|pin6| LS1[AHCT245_CH1]
    LS1 --> R33[Res33_Ω]
    R33 --> LEDStrip[WS2812B_Chain]
  end

  subgraph MIDIOut["MIDI Out"]
    U1 -->|pin1| LS2[AHCT245_CH2]
    LS2 --> R220[Res220_Ω]
    R220 --> DINOut[DIN_Out]
    R220 --> TRSOut[TRS_Type-A_Out]
  end
```
