bseverns/MOARkNOBS-42/docs/project/PilotRun.md

# Pilot Run / Artist Edition

This page explains what a pilot run means in the context of MOARkNOBS-42.

It is not a pricing page or a promise of public order timing. To express interest or ask whether a setup fits the pilot-run boundary, email [severns3@gmail.com](mailto:severns3@gmail.com). No payment or preorder is requested through this page.

## What a pilot run means here

In this project, a pilot run means a first small-batch release of a real instrument with a real support ecosystem around it, but with honest limits.

That support ecosystem currently includes:

- the hardware instrument itself
- current firmware and repo-documented behavior
- the browser configurator workflow
- the OSC / virtual MIDI bridge workflow
- builder, performer, validation, and troubleshooting docs

It does not imply a mass-market launch or universal compatibility claims.

## Who it is for

A pilot-run unit is best suited to people who are comfortable with one or more of these:

- experimental performance setups
- browser or bridge-based workflow choices
- reading documentation before assuming behavior
- validating a real instrument on a real host setup

That includes:

- experimental musicians
- sound and media artists
- advanced builders
- educators and instrument hackers

## What support is included

The primary support layer is the documentation in this repo.

That includes:

- quickstarts for builders and performers
- connectivity guidance for configurator vs bridge use
- validation flow and demo-test guidance
- troubleshooting and support-boundary docs

See:

- [Quickstart for Performers](../getting-started/QuickstartForPerformers.md)
- [Quickstart for Builders](../getting-started/QuickstartForBuilders.md)
- [Connectivity Guide](../getting-started/ConnectivityGuide.md)
- [Validation Flow](../validation/ValidationFlow.md)
- [License and Support](LicenseAndSupport.md)

## What support is not included

This project does not currently promise:

- consumer-style warranty language beyond the actual licenses
- guaranteed response times
- undocumented browser, DAW, or host compatibility
- guaranteed approval of substitute hardware parts
- an assumption that every buyer wants or needs the same workflow

## What early buyers should expect

Early buyers should expect a real instrument with a rich documentation trail, not a sealed consumer appliance.

In practice that means:

- you should expect to choose the right path for your setup: configurator or bridge
- you should expect to validate your actual host environment rather than infer support from generic assumptions
- you should expect the docs to tell you what is current, what is verified, and what still needs bench validation
- you should expect the project's small-batch and artist-run character to remain visible rather than hidden behind generic marketing

## The honest release frame

If you want a controller that behaves like a generic plug-and-play utility surface, this may not be the right fit.

If you want an instrument you can understand, modify, and situate inside a documented ecosystem, the pilot-run framing is the right way to read this project.
