bseverns/MOARkNOBS-42/docs/bench/bridge-host-recipes/TEMPLATE_host-recipe-receipt.md

# Bridge Host Recipe Receipt: RECIPE_NAME

Date/time: unknown/not captured
Git commit/tag: unknown/not captured
Host OS: unknown/not captured
Bridge mode: source or packaged
Node version or artifact name: unknown/not captured
DAW/app/version: unknown/not captured
OSC ports: unknown/not captured
MIDI port label: unknown/not captured
Serial device or simulator: unknown/not captured
Artifact paths: unknown/not captured

## Actions tested

1. Start the Bridge and record the mode and URL or artifact name.
2. Record the host recipe or preset used.
3. Record the serial device or simulator lane used.
4. Record the exact OSC host/listen ports and MIDI port label.
5. Record the exact DAW/app actions tested.
6. Record the exact Bridge evidence observed.
7. Record the exact DAW/app evidence observed.

## Result

PASS, PARTIAL, or FAIL

## Proven

- State only what this receipt directly proves.
- If the Bridge reached `ready`, say that.
- If DAW/app MIDI or OSC ingress was directly observed, say exactly how.
- If return traffic back into the Bridge was directly observed, say exactly how.

## Caveats

- State what was not observed.
- If the DAW/app was open but ingest/return proof was not completed, mark that explicitly.
- Do not claim broad certification from one host/app/version receipt.

## Supporting evidence

- Recipe definition: unknown/not captured
- Supporting bridge receipt: unknown/not captured
- Supporting firmware receipt: unknown/not captured

## Artifact notes

- Screenshots, screen recordings, Bridge logs, route traces, DAW project files, or exported state JSON: unknown/not captured
