bseverns/MOARkNOBS-42/hardware/archive/README.md

# Hardware Photo Archive

`T-3D5W706139A/` contains raw historical assembly photographs retained for project provenance. The filenames came from the source archive and are not a current assembly sequence, fabrication package, or release claim.

Use `docs/assets/board/` for optimized reader-facing photographs and `hardware/CurrentBuild.md` for current hardware status.
