bseverns/MOARkNOBS-42/docs/assets/board/brdF.png

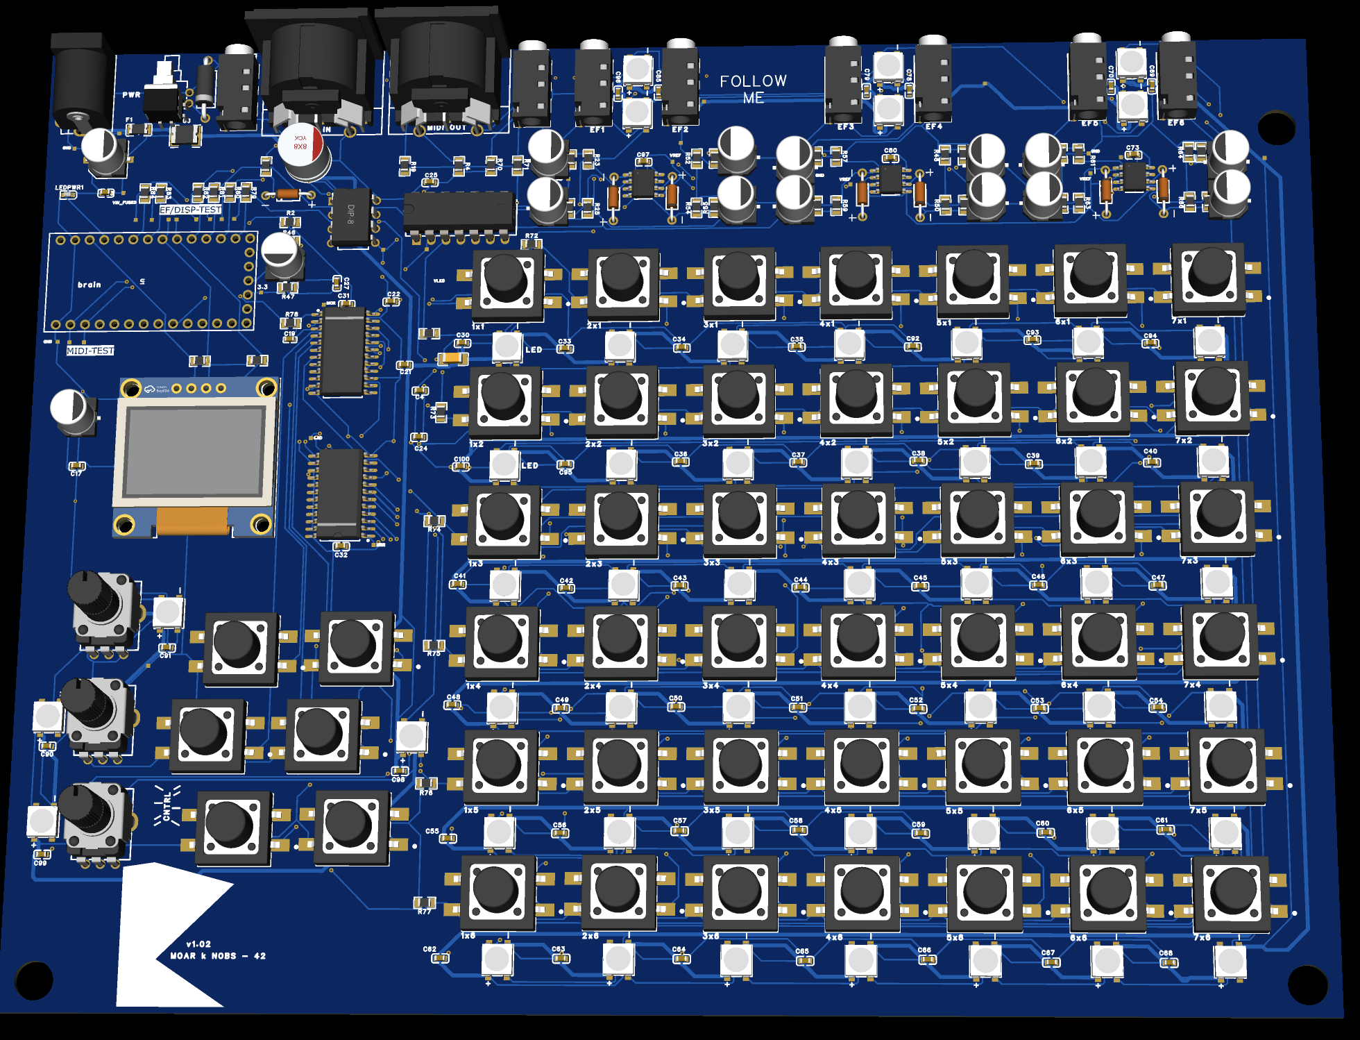
docs/assets/board/brdF.png
