bseverns/MOARkNOBS-42/docs/assets/board/brdR.png

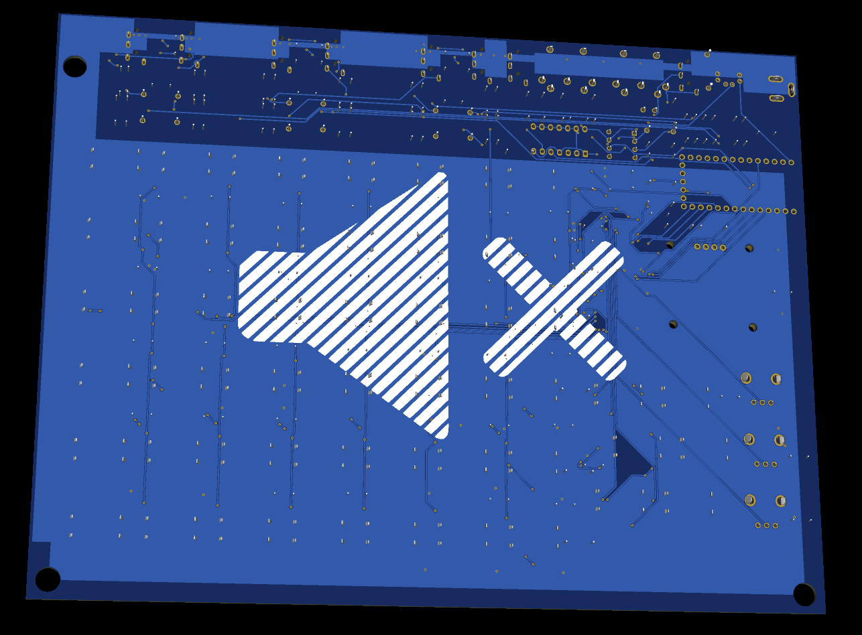
docs/assets/board/brdR.png
