bseverns/MOARkNOBS-42/docs/assets/board/land.png

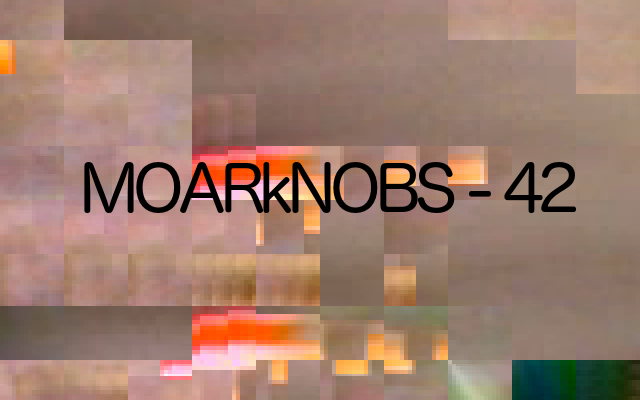
docs/assets/board/land.png
