bseverns/MOARkNOBS-42/docs/assets/board/moarB.png

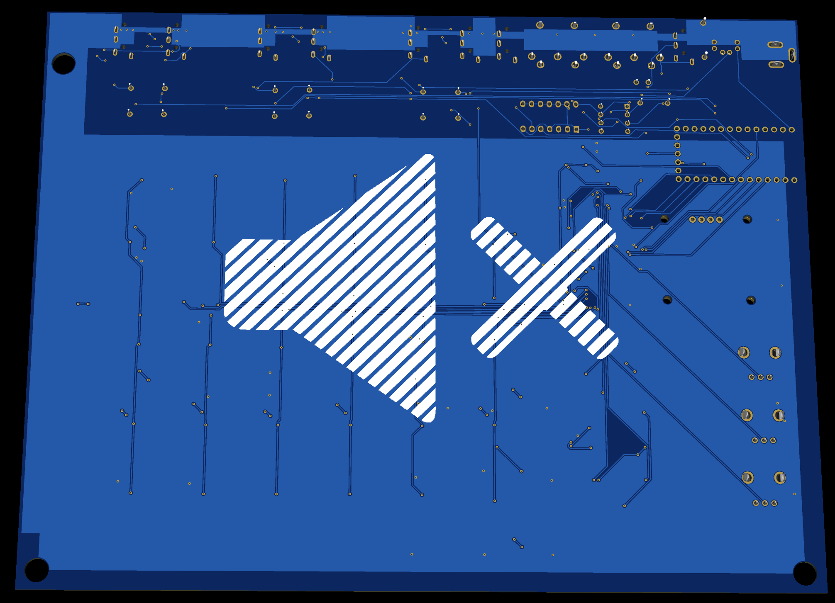
docs/assets/board/moarB.png
