bseverns/MOARkNOBS-42/docs/assets/signal-shapes/bandpass.png

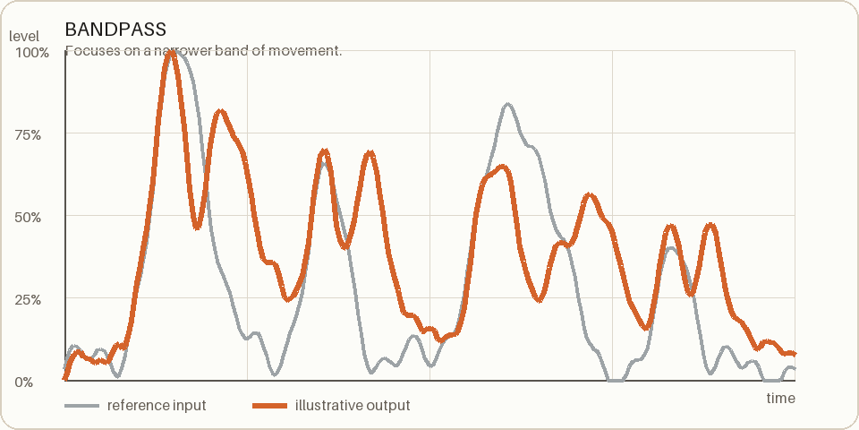
docs/assets/signal-shapes/bandpass.png
