bseverns/MOARkNOBS-42/docs/assets/signal-shapes/exponential.png

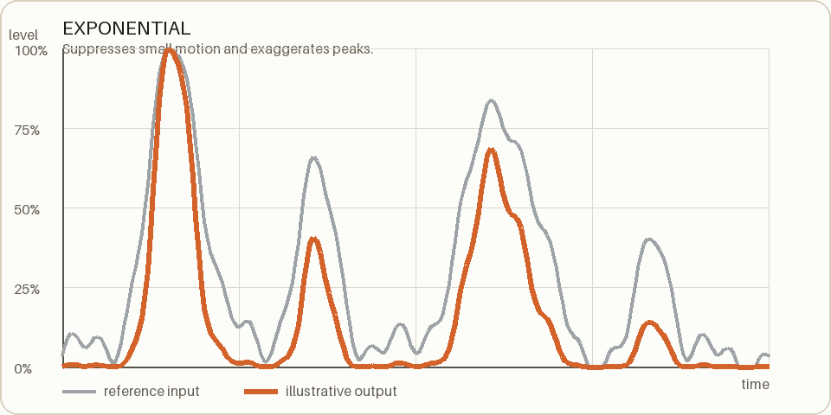
docs/assets/signal-shapes/exponential.png
