bseverns/MOARkNOBS-42/docs/assets/signal-shapes/highpass.png

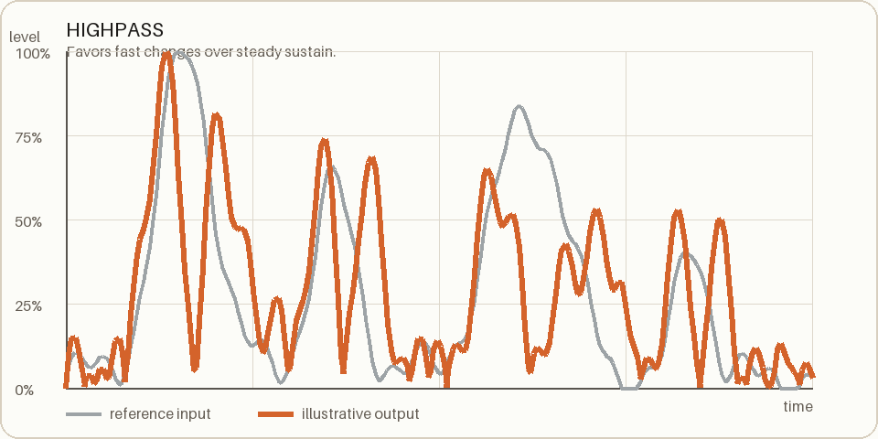
docs/assets/signal-shapes/highpass.png
