bseverns/MOARkNOBS-42/docs/assets/signal-shapes/linear.png

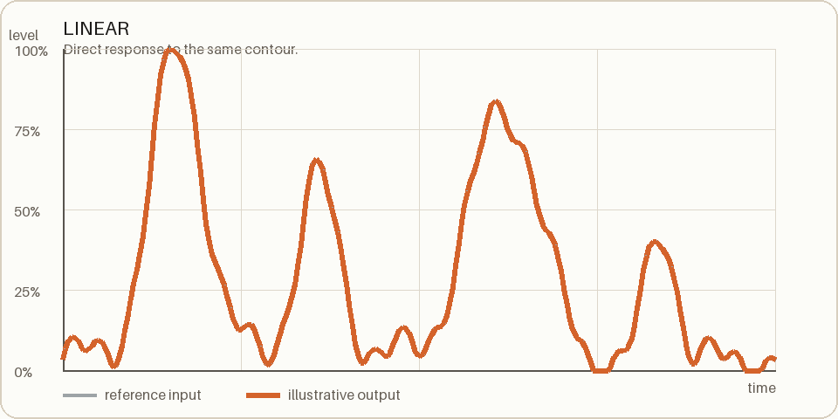
docs/assets/signal-shapes/linear.png
