bseverns/MOARkNOBS-42/docs/assets/signal-shapes/lowpass.png

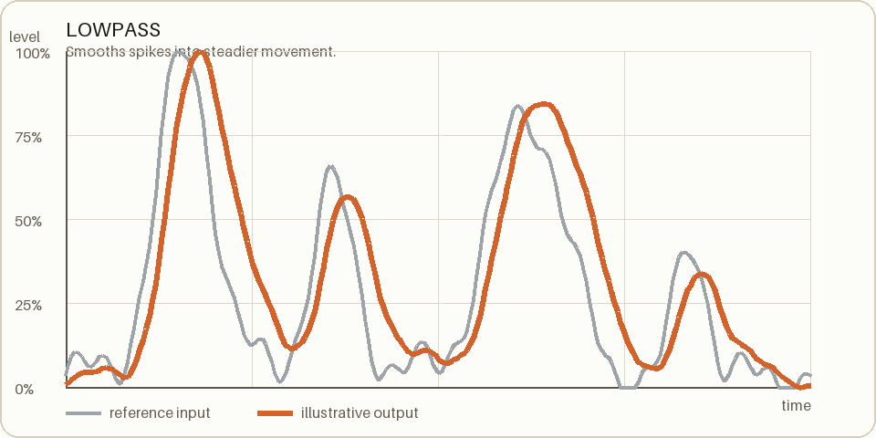
docs/assets/signal-shapes/lowpass.png
