bseverns/MOARkNOBS-42/docs/assets/signal-shapes/opposite_linear.png

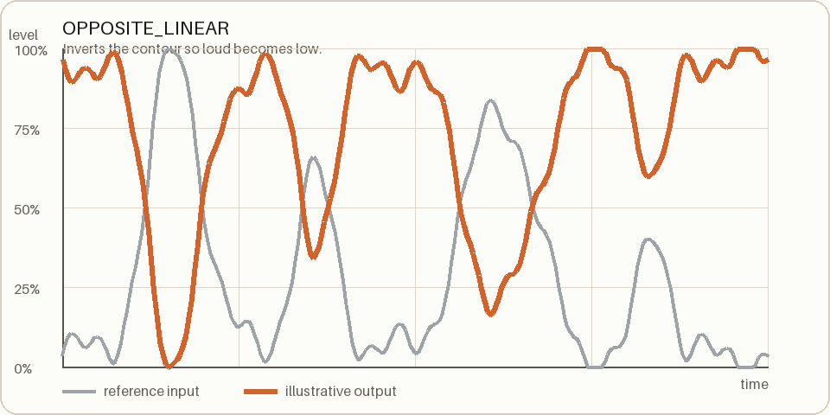
docs/assets/signal-shapes/opposite_linear.png
