bseverns/MOARkNOBS-42/docs/sketch/Interface&Cntrl.png

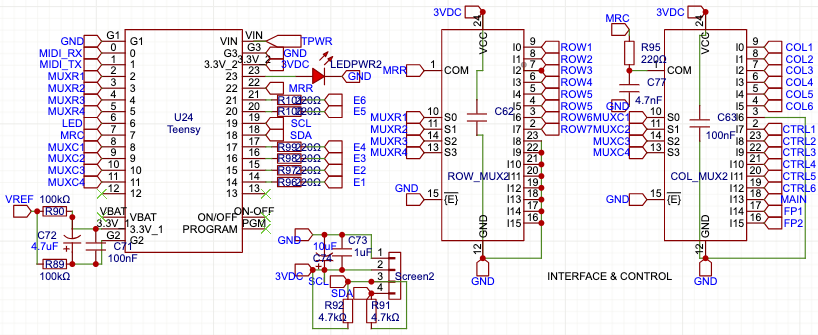
docs/sketch/Interface&Cntrl.png
