bseverns/MOARkNOBS-42/docs/sketch/Power-Reg.png

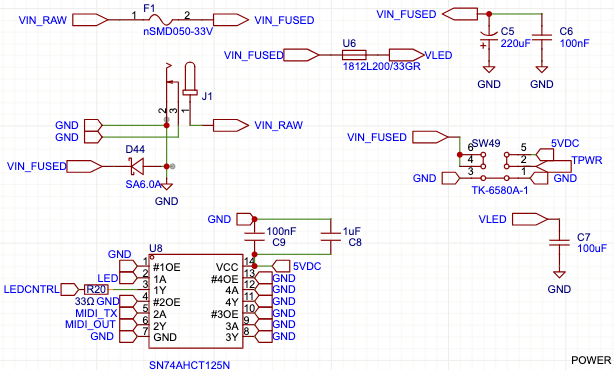
docs/sketch/Power-Reg.png
