bseverns/MOARkNOBS-42/docs/sketch/T-3D5W706139A/0ce41d7c40958f2d3d69cfa9ba016e89.jpg

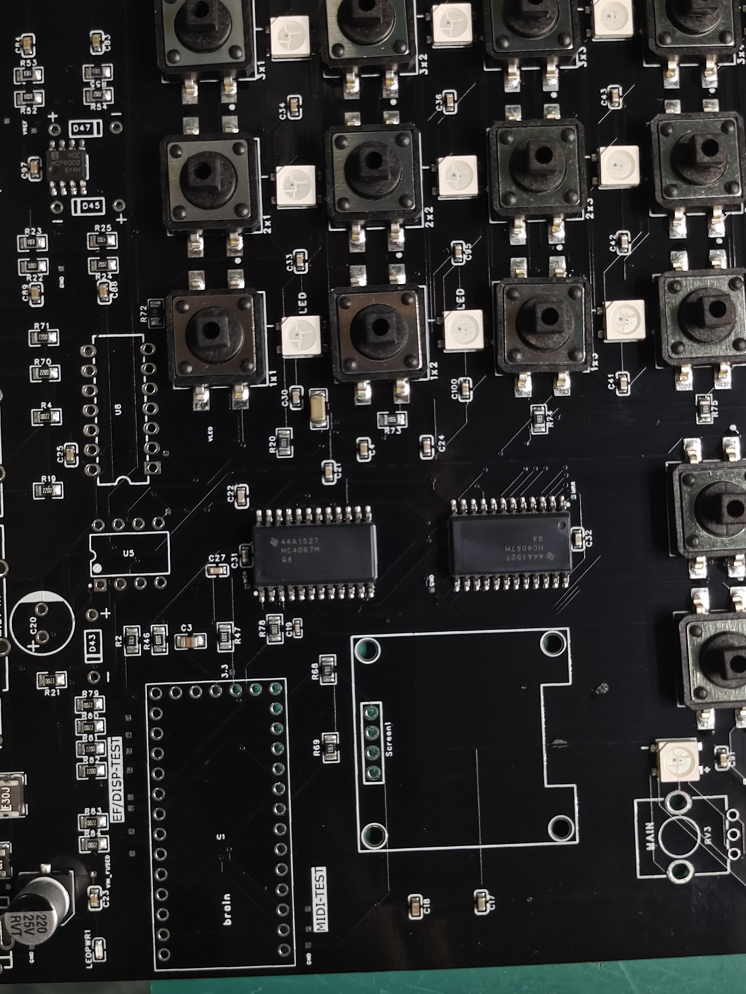
docs/sketch/T-3D5W706139A/0ce41d7c40958f2d3d69cfa9ba016e89.jpg
