bseverns/MOARkNOBS-42/docs/sketch/T-3D5W706139A/5ca78f7f64a5ae205a25a15a012c0280.jpg

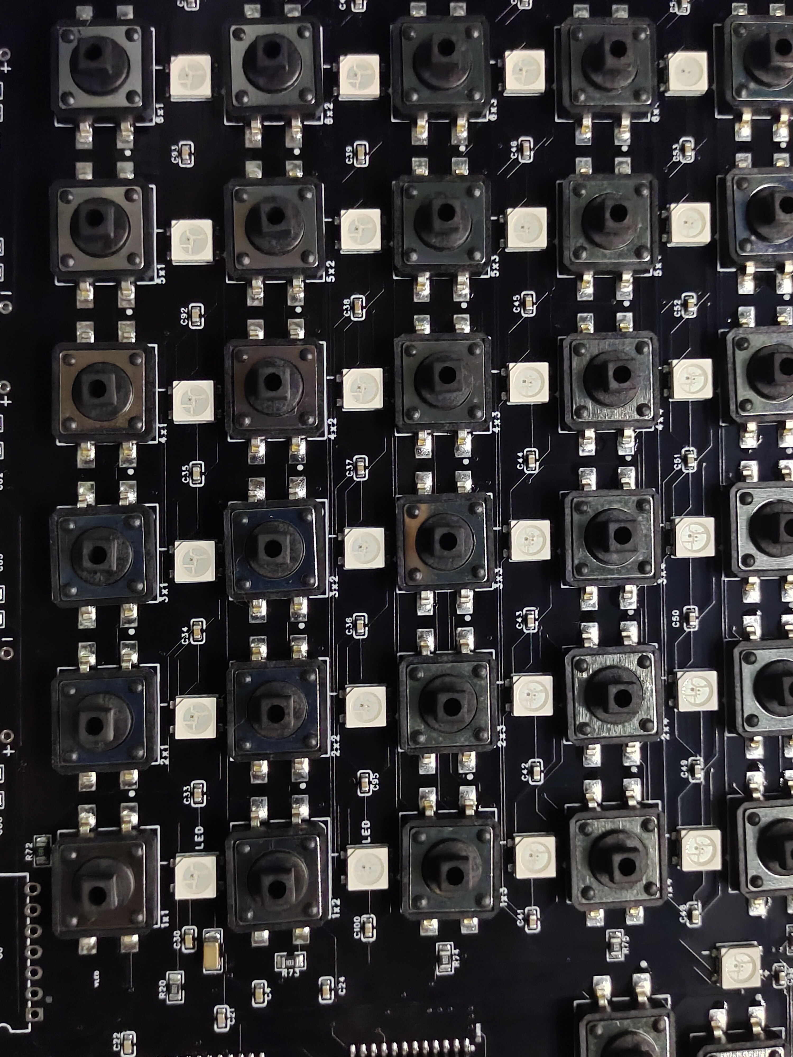
docs/sketch/T-3D5W706139A/5ca78f7f64a5ae205a25a15a012c0280.jpg
