bseverns/MOARkNOBS-42/docs/sketch/T-3D5W706139A/07f777c57aa990516baf06bcd4414bbb.jpg

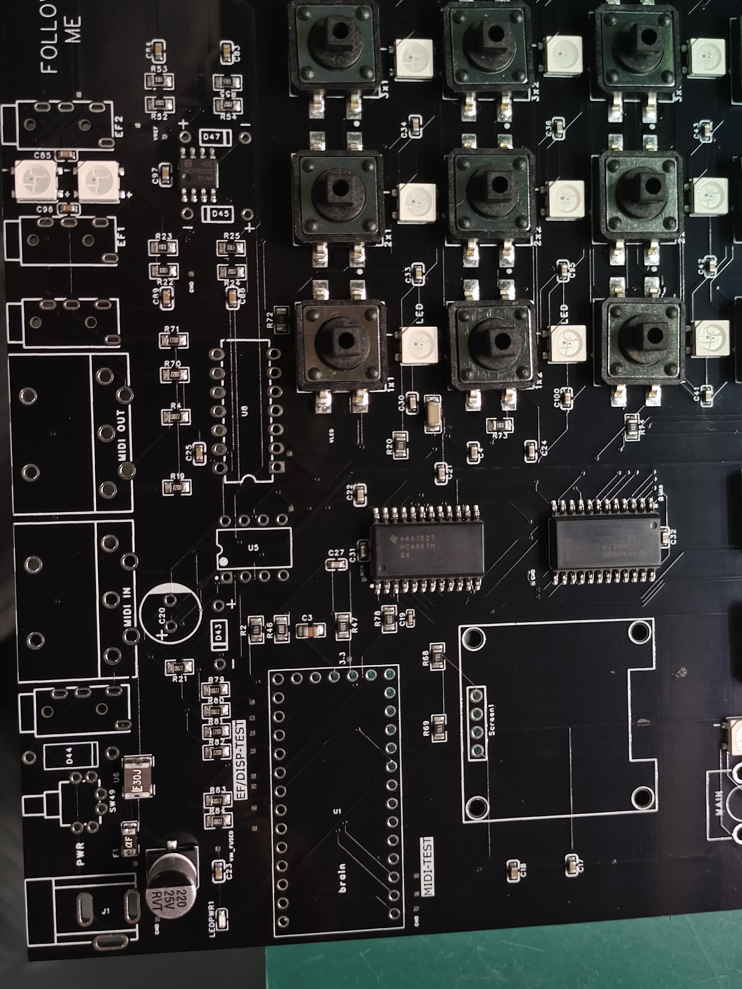
docs/sketch/T-3D5W706139A/07f777c57aa990516baf06bcd4414bbb.jpg
