bseverns/MOARkNOBS-42/docs/sketch/T-3D5W706139A/8e1e0dce52fd3a631518eacc81225a61.jpg

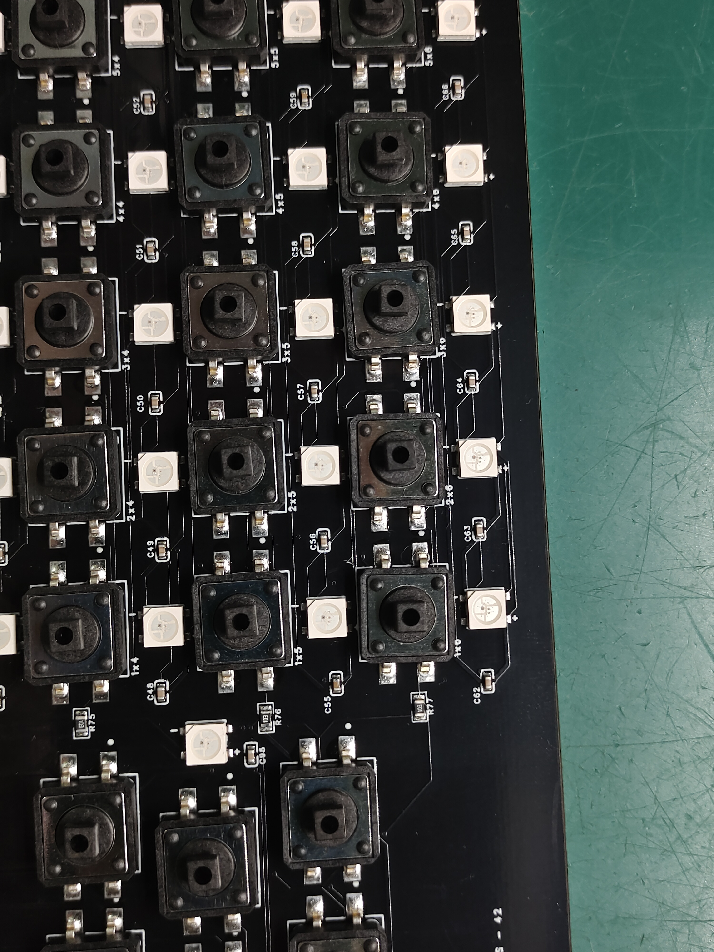
docs/sketch/T-3D5W706139A/8e1e0dce52fd3a631518eacc81225a61.jpg
