bseverns/MOARkNOBS-42/docs/sketch/T-3D5W706139A/47fe4ad2c3bd3f0e1658a6497c9ed50b.jpg

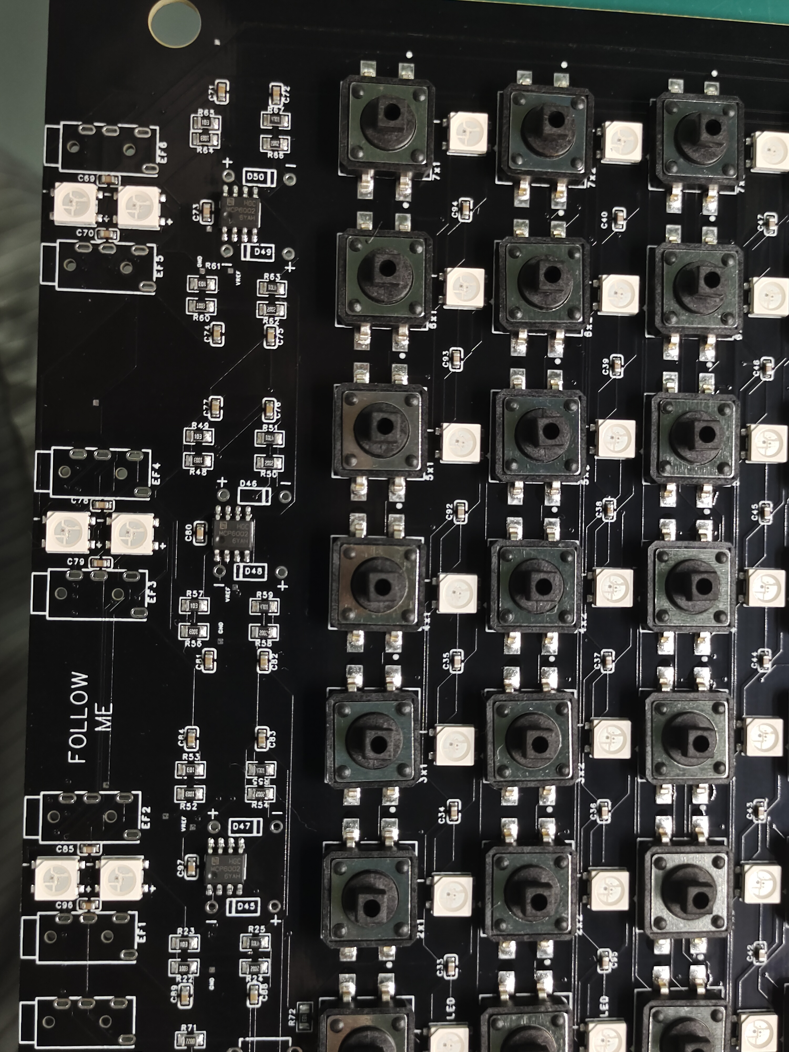
docs/sketch/T-3D5W706139A/47fe4ad2c3bd3f0e1658a6497c9ed50b.jpg
