bseverns/MOARkNOBS-42/docs/sketch/T-3D5W706139A/78880a4b465c2dc8e506313f1d6a85d5.jpg

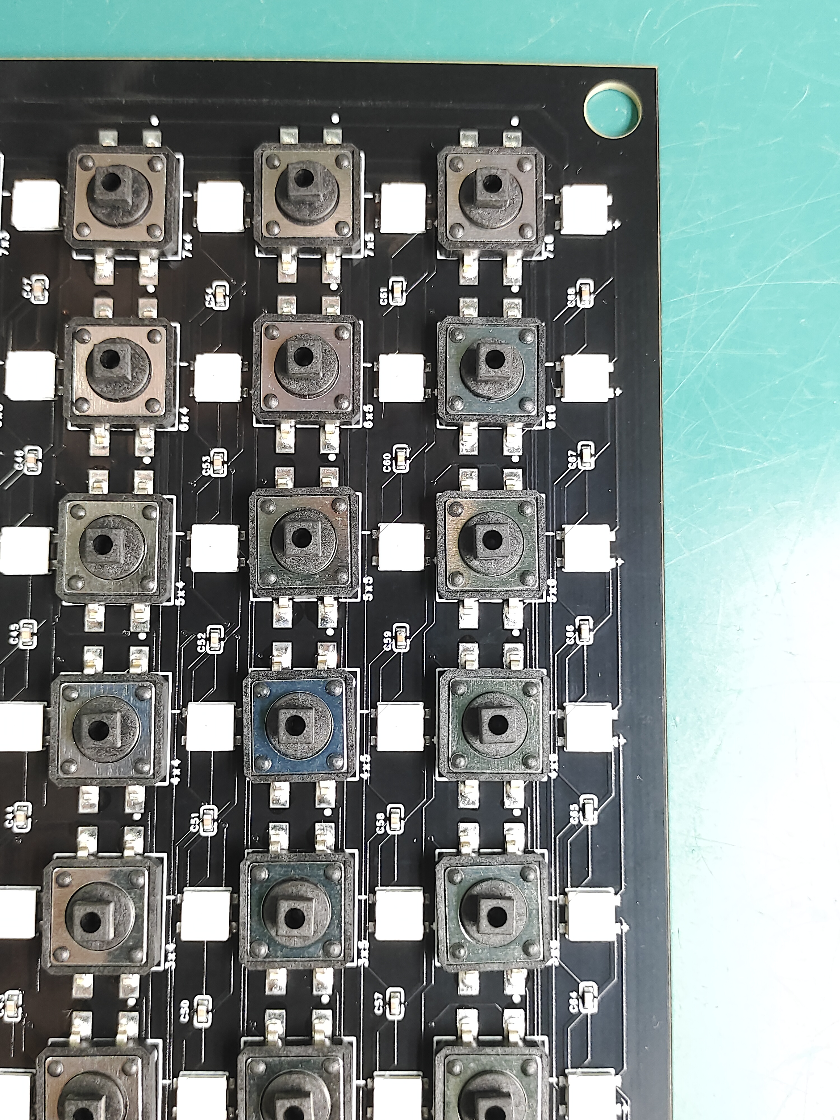
docs/sketch/T-3D5W706139A/78880a4b465c2dc8e506313f1d6a85d5.jpg
