bseverns/MOARkNOBS-42/docs/sketch/T-3D5W706139A/256810d17fca38f6c7abfe4b21114cba.jpg

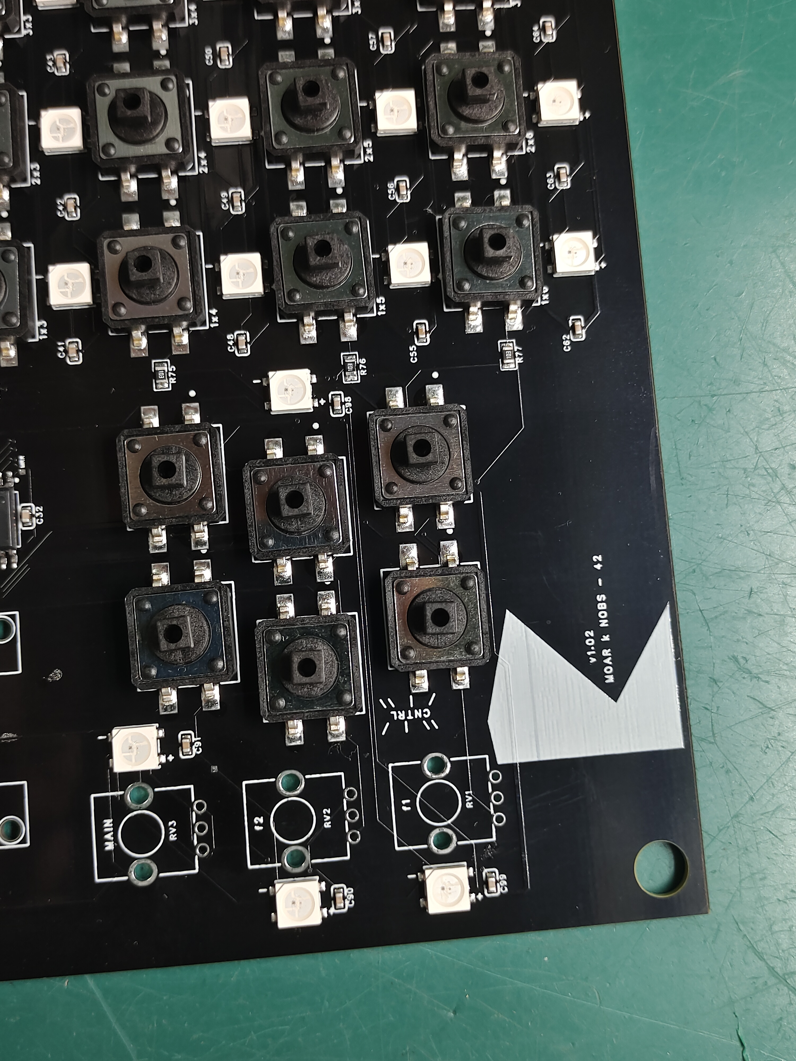
docs/sketch/T-3D5W706139A/256810d17fca38f6c7abfe4b21114cba.jpg
