bseverns/MOARkNOBS-42/docs/sketch/T-3D5W706139A/1122399b50725b229eef99579e961d21.jpg

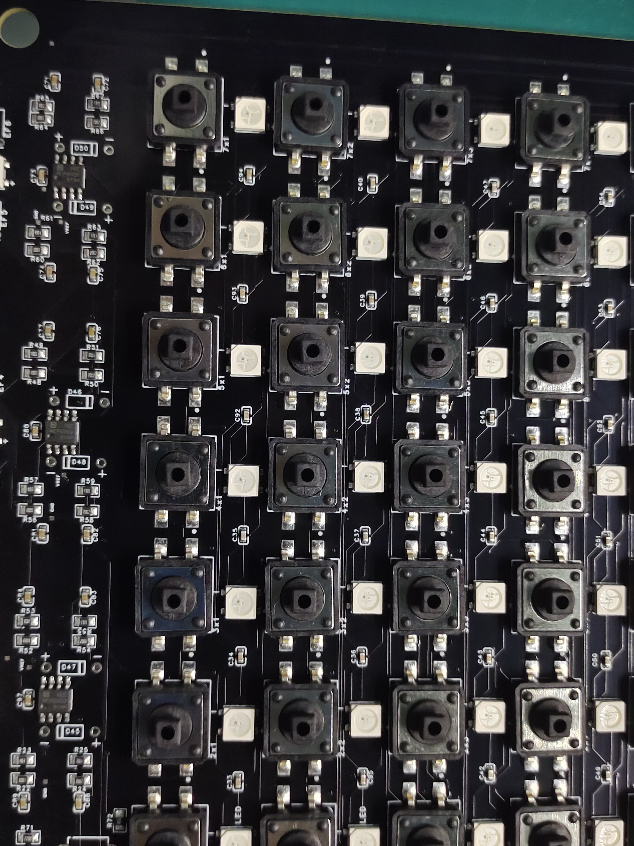
docs/sketch/T-3D5W706139A/1122399b50725b229eef99579e961d21.jpg
