bseverns/MOARkNOBS-42/docs/sketch/T-3D5W706139A/c3f57a14d89240ee652f2c90f77bc39f.jpg

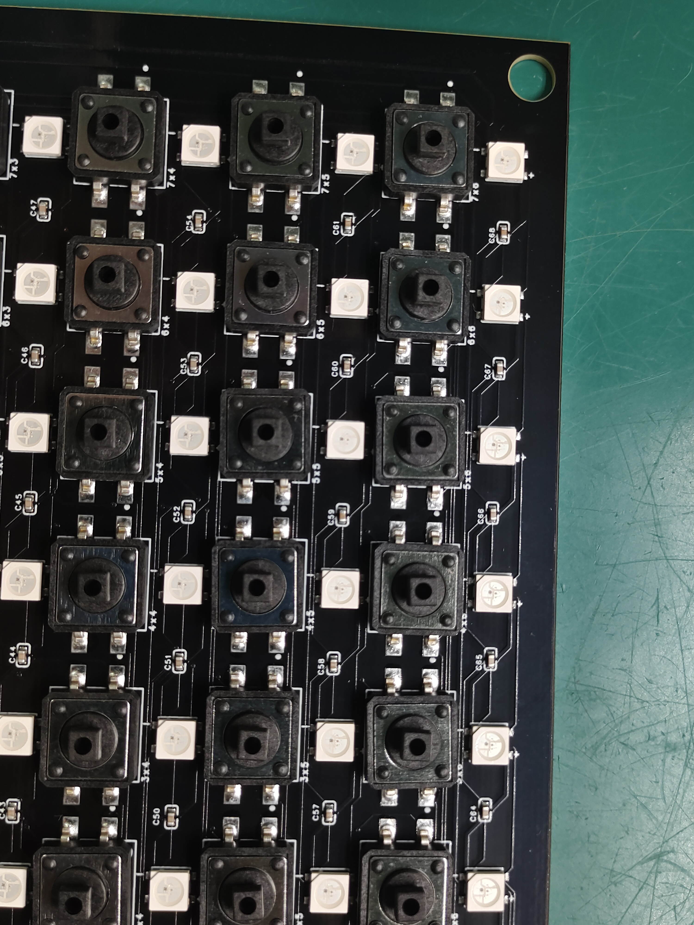
docs/sketch/T-3D5W706139A/c3f57a14d89240ee652f2c90f77bc39f.jpg
