bseverns/MOARkNOBS-42/docs/sketch/T-3D5W706139A/D1–D60 Arrow points to notch. Confirm orientation.png

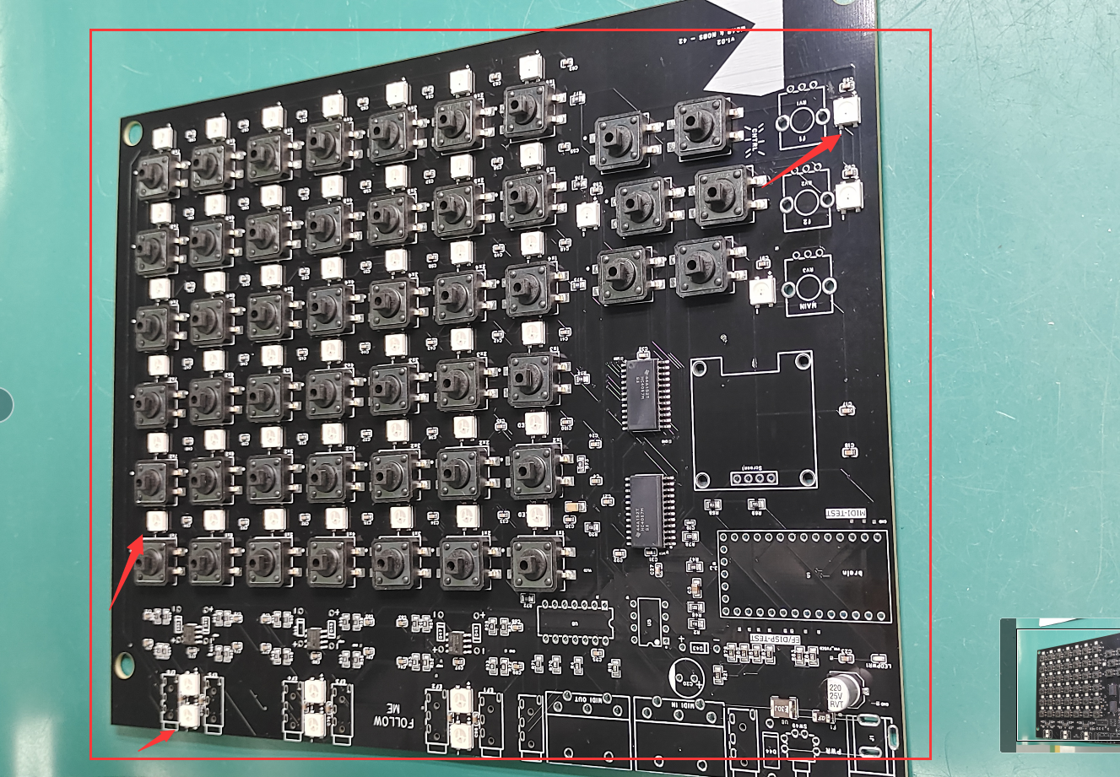
docs/sketch/T-3D5W706139A/D1–D60 Arrow points to notch. Confirm orientation.png
