bseverns/MOARkNOBS-42/docs/guides/LfoRouteGuide.md

# LFO Route Guide

The LFO system becomes much easier to understand once you stop thinking "there are two LFOs" and start thinking "there are a few specific places motion is allowed to go."

This page explains those destinations in plain language.

Every MIDI slot now also owns two fixed lanes: lane 0 always reads LFO 1 and
lane 1 always reads LFO 2. A lane stores an enabled flag, a combine mode, and a
signed amount from -100% to +100%. Fixed lanes compose after EF/ARG in the
order LFO 1 then LFO 2; they do not send a second competing slot value.

`Centered` is the default mode when a lane is first enabled. The physical knob
therefore remains the center of gravity while the oscillator moves around it.
At 100% amount, a bipolar LFO contributes `-64..+63`, allowing a baseline of 64
to reach the complete MIDI range without making most of the waveform clip.

`AddClamp` and `Subtract` instead consume the oscillator's normalized `0..1`
value and add or subtract as much as `0..127` at 100% amount. They are
unipolar operations, so zero is neutral. `Replace` maps the bipolar source
around 64, while `Scale` applies a bipolar multiplier to the preceding value.
A negative amount reverses the direction of any mode.

Legacy global `SlotValue` routes retain their original replacement behavior:
their mapped `0..127` result becomes the complete outgoing slot value and does
not move around the physical knob baseline. If the corresponding fixed lane is
enabled, it shadows the legacy route so only one path owns that LFO/slot pair.

## Start here if you are new

If you are new to routes, start with:

- one LFO
- one internal route
- moderate depth
- a clear target like arp swing or velocity shift

That makes the modulation obvious before it becomes complicated.

## Route overview

The current default routing is simple on purpose: one LFO is easy to see and hear, the other changes how hard the reactive layer bites.

Overview illustration showing internal LFO targets. ArpSwing is shown as shifted offbeats, EfGainTrim as a stronger envelope lane, and velocity/chance as note-shaping routes.

## Internal targets

The current internal route targets are:

- `EfGainTrim`
- `ArpSwing`
- `VelocityShift`
- `NoteChance`
- `ArpGate`
- `JitterDepth`
- `JitterSmoothness`

These are not equivalent. Each one changes a different layer of the instrument.

## What the OLED currently shows

The current firmware does not expose a dedicated "LFO edit" page on the OLED. The closest live on-device readout is the debug diagnostics page, which prints normalized `L1` and `L2` values on the bottom row while showing envelope health above it.

Mock OLED view showing the current debug diagnostics page. The screen reads DBG BPM with clock status, then E0 through E5 envelope baseline/gain/value rows, and ends with L1 and L2 normalized values on the bottom line.

That preview is based on the current `DisplayManager` debug-page strings, so it reflects what the firmware is documenting today rather than an invented UI concept.

## `VelocityShift`

What it changes:

- outgoing note velocity offset during note-trigger paths

Best for:

- making notes breathe in intensity without touching base mappings

## `ArpSwing`

This target changes timing feel rather than color or amplitude.

What it changes:

- how straight or swung the arpeggiator timing feels

What that means musically:

- low depth gives a gentle alive-not-rigid feel
- high depth can make the groove feel dramatically uneven or unstable

Best for:

- performance experiments
- demonstrating that modulation can affect feel, not just value

Not the best first target if the player is still learning basic timing behavior.

## `NoteChance`

What it changes:

- probability of note generation in note-trigger paths

What that means musically:

- low depth keeps phrases steady
- higher depth makes rhythmic density ebb and flow

## `ArpGate`

What it changes:

- note gate percentage in the arpeggiator path

What that means musically:

- shorter values feel percussive
- longer values feel legato

## `JitterDepth`

What it changes:

- the amplitude of random Perlin-based motion used by random filter/arp modes

## `JitterSmoothness`

What it changes:

- the step-to-step smoothness of random Perlin-based motion

## `EfGainTrim`

This target changes how strongly the envelope follower path bites.

What it changes:

- the effective intensity of the reactive control layer

What that means musically:

- low depth can make a reactive setup breathe
- high depth can make the follower path feel overexcited or inconsistent if the rest of the system is already complex

Best for:

- advanced reactive patches
- dynamic modulation experiments

Use carefully when teaching, because it changes the behavior of the control source itself rather than just an obvious output.

## Internal versus external routes

Routes can also go outward to MIDI CC or OSC, but the internal targets are the most important ones to learn first.

Why:

- internal targets are immediate
- they teach the modulation bus without external tooling
- they are easier to debug from the browser and hardware at the same time

Once those make sense, MIDI/OSC routes become much less mysterious.

## Safe first route progression

1. `VelocityShift`
2. `ArpSwing`
3. `EfGainTrim`
4. `NoteChance`
5. `ArpGate`
6. `JitterDepth`
7. `JitterSmoothness`

That order moves from visible, to musical, to structurally reactive.

## Depth: subtle versus extreme

Depth is where most routes either become expressive or become too much.

Use subtle depth when:

- the route should support the player
- the modulation should feel alive but not obvious

Use stronger depth when:

- you are demonstrating the route
- the modulation is meant to become part of the foreground character

The easiest mistake is to judge a target only at extreme depth. Many of these routes are most useful in the middle.

## How routes relate to profiles

Routes are part of the profile snapshot.

That means:

- loading a profile restores LFO routing
- saving a profile preserves that modulation structure
- the browser and telemetry can show the same route behavior the firmware is actually using

See: [Profile Workflow](ProfileWorkflow.md)

## Good route demos

### Best first demo

- target: `VelocityShift`
- depth: moderate
- goal: audible motion in repeated notes

### Best musical demo

- target: `ArpSwing`
- depth: subtle-to-medium
- goal: show groove motion without breaking the phrase

### Best advanced reactive demo

- target: `EfGainTrim`
- depth: subtle
- goal: make the follower path feel alive without turning into noise

## Read next

- [Reactive Control Guide](ReactiveControlGuide.md) for how LFO routes fit the full motion engine
- [Profile Workflow](ProfileWorkflow.md) for how routes persist
- [Preset Library](PresetLibrary.md) for presets that make these route ideas easier to hear and see
