bseverns/MOARkNOBS-42/docs/getting-started/ConnectivityGuide.md

# Connectivity Guide

Use this page when you are deciding between the browser configurator and the bridge.

Current contract/support boundary: [Host Compatibility](../reference/HostCompatibility.md), [App/README.md](https://github.com/bseverns/MOARkNOBS-42/blob/main/App/README.md), [bridge/README.md](https://github.com/bseverns/MOARkNOBS-42/blob/main/bridge/README.md), [Documentation Truth Map](../reference/DocumentationTruthMap.md).

Decision graphic comparing the direct configurator path with the bridge path for OSC and DAW workflows.

## The short version

- Use the `configurator` when you want to talk directly to one board over USB for setup, monitoring, and profile management.
- Use the `bridge` when you need OSC or a virtual MIDI port for a DAW or host application.

## What the configurator does

The browser configurator talks directly to the board over WebSerial. It is the best path for:

- connecting to one board over USB
- viewing manifest/config data
- staging and applying edits
- loading and saving profiles
- exporting/importing JSON configs

See [Configurator Tour](../guides/Configurator.md).

## What the bridge does

The bridge is a Node.js process that sits between the board and other software. It now has a browser-driven local console that starts/stops the bridge and opens the configurator over the bridge transport. It is the best path for:

- turning board telemetry into OSC
- creating a virtual MIDI port for a DAW
- receiving OSC or MIDI commands and forwarding them back to the board
- keeping the configurator available while OSC and virtual MIDI are running

See [OSC Bridge](../guides/OSCBridge.md) and [Performer Bridge Guide](../guides/BridgeForPerformers.md).

## When WebSerial alone is enough

WebSerial alone is enough when all of these are true:

- the board is connected directly over USB
- you only need configuration, monitoring, and profile work
- you do not need OSC routing
- you do not need a virtual MIDI device in another host

## When the bridge is needed

Use the bridge when any of these are true:

- you want OSC in Max, Pure Data, TouchOSC, or another OSC-capable host
- you want a DAW to see a virtual MIDI port named `MN42 Bridge`
- your workflow is built around OSC/MIDI software instead of direct browser configuration
- you want to open the configurator from the bridge console without relying on WebSerial

## What other software sees

### What a DAW sees

The bridge exposes a virtual MIDI port named `MN42 Bridge`.

Bridge MIDI mapping documented in the repo:

- Channel 1 CC `0..41` = slot updates
- Channel 2 CC `0..5` = envelope follower updates

### What an OSC host sees

The bridge publishes:

- `/mn42/slots`
- `/mn42/envelopes`

And it accepts commands at:

- `/mn42/cmd`

For live slot control, send JSON shaped like
`{"cmd":"SET_SLOT_VALUE","slot":2,"value":95}`.

## Minimal compatibility matrix

| Workflow | What is required | Status | Notes |
| --- | --- | --- | --- |
| Browser configurator over WebSerial | Browser with WebSerial support plus `http://localhost` or another allowed secure context | Verified in repo evidence | Chromium-based automation and App docs treat this as the strongest direct-browser path. |
| Browser configurator in Firefox or Safari | Browser support for the same WebSerial flow | Not claimed | This repo does not treat Firefox/Safari WebSerial as a verified path. Use Chromium or the bridge when the browser path matters. |
| Browser-driven bridge console | Node.js 24 plus a desktop browser | Verified in repo evidence | The bridge UI serves the configurator at `/app/`, exposes raw `/ws`, and now prefers the structured bridge session/runtime when available. |
| Bridge CLI on desktop host | Node.js 24 plus USB serial access | Verified in repo evidence | The bridge runtime and tests are aligned around the Node 24 desktop-host lane. |
| OSC host integration | Running bridge plus UDP OSC host | Documented path, bench validation still required | The OSC contract is documented and software-tested, but host-specific bench proof still depends on the operator setup. |
| DAW integration | Running bridge plus DAW MIDI device enablement | Documented path, bench validation still required | The bridge advertises `MN42 Bridge`, but this repo does not claim broad DAW-by-DAW validation. |

## Recommended decision rule

1. Start with the configurator if your goal is setup or profile editing.
2. Add the bridge only when you need OSC or DAW-facing virtual MIDI.
3. If a browser path is uncertain, use the bridge rather than guessing.
