bseverns/MOARkNOBS-42/App/tests/visual-snapshots/configure-1440x1000.png

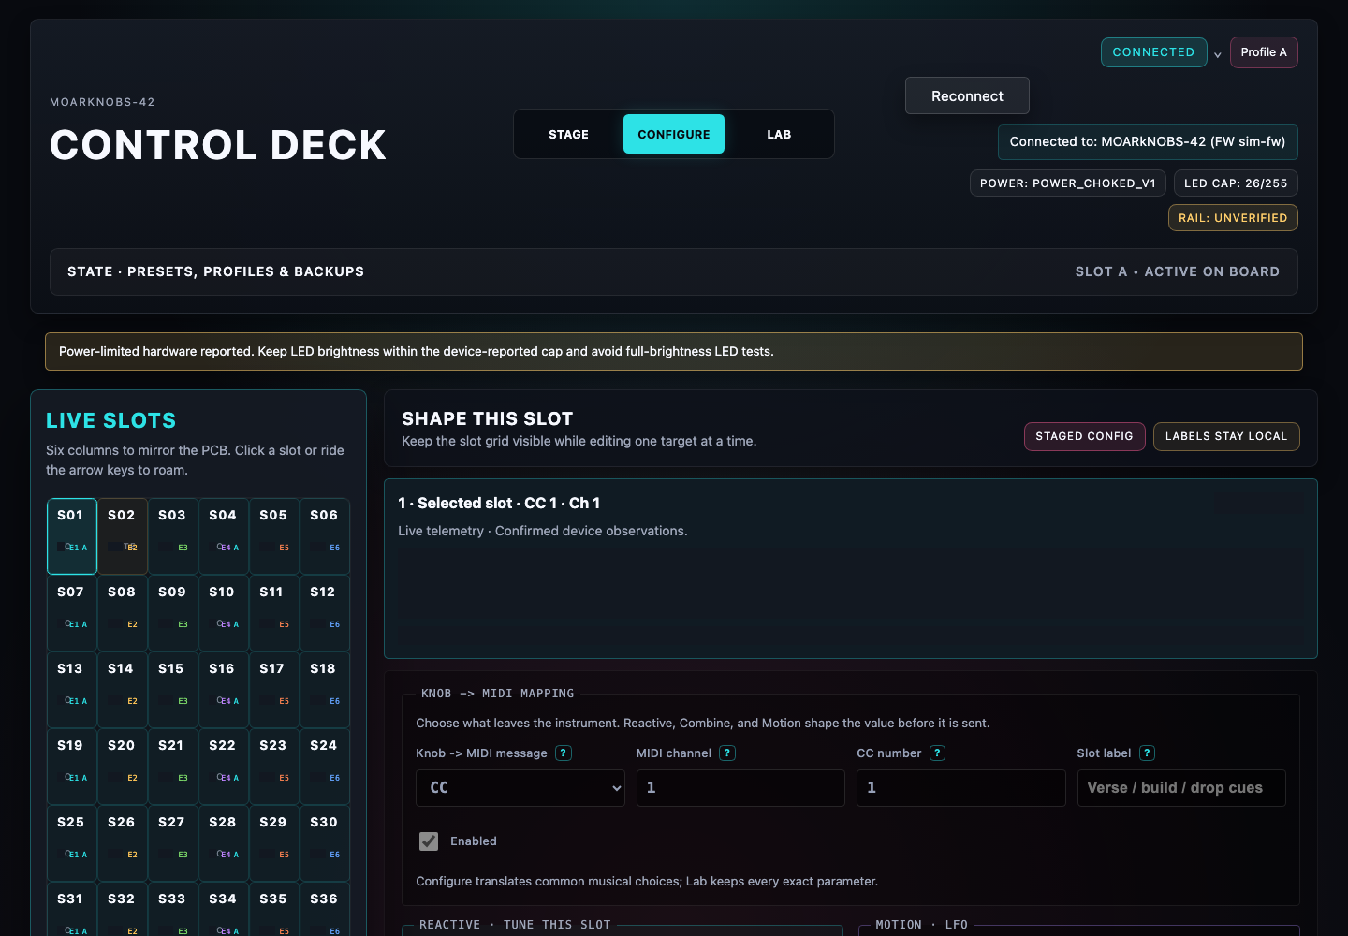
App/tests/visual-snapshots/configure-1440x1000.png
