bseverns/MOARkNOBS-42/App/tests/visual-snapshots/incoming-midi-open-1356.png

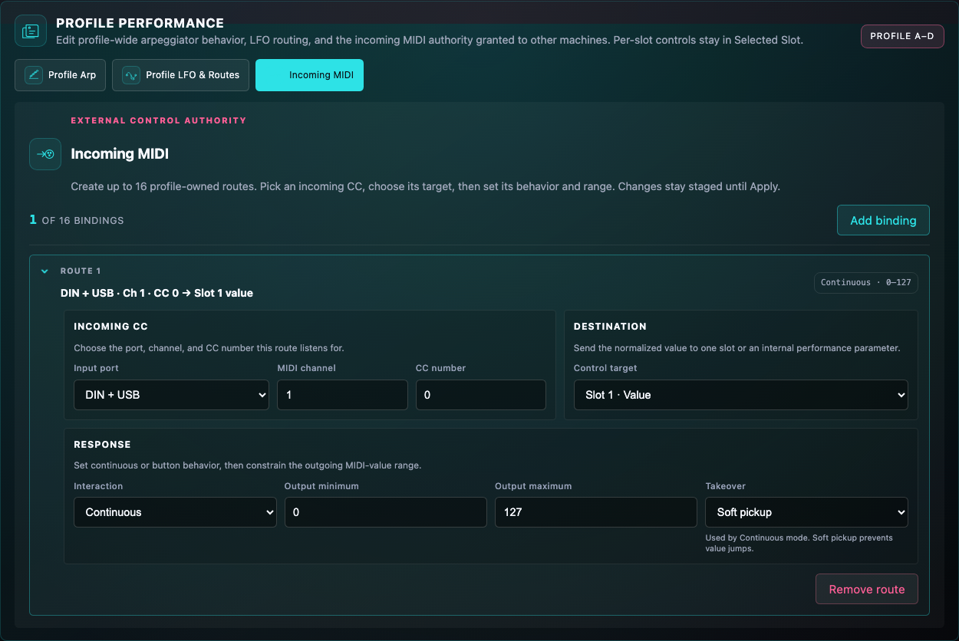
App/tests/visual-snapshots/incoming-midi-open-1356.png
