bseverns/MOARkNOBS-42/App/tests/visual-snapshots/lab-1920x1080.png

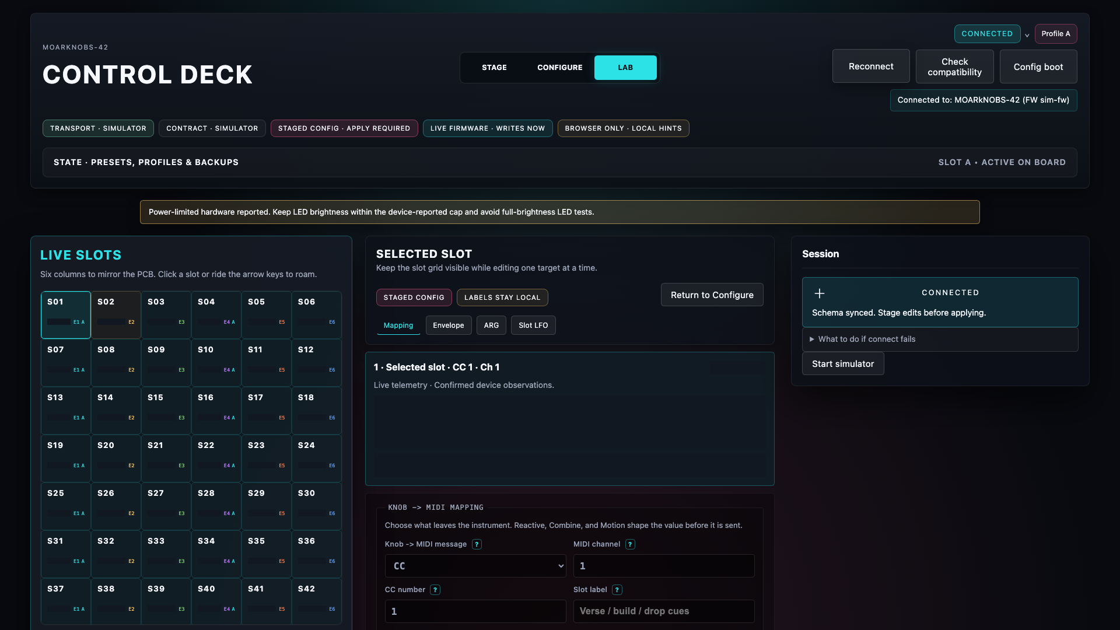
App/tests/visual-snapshots/lab-1920x1080.png
