bseverns/MOARkNOBS-42/App/tests/visual-snapshots/stage-1440x1000.png

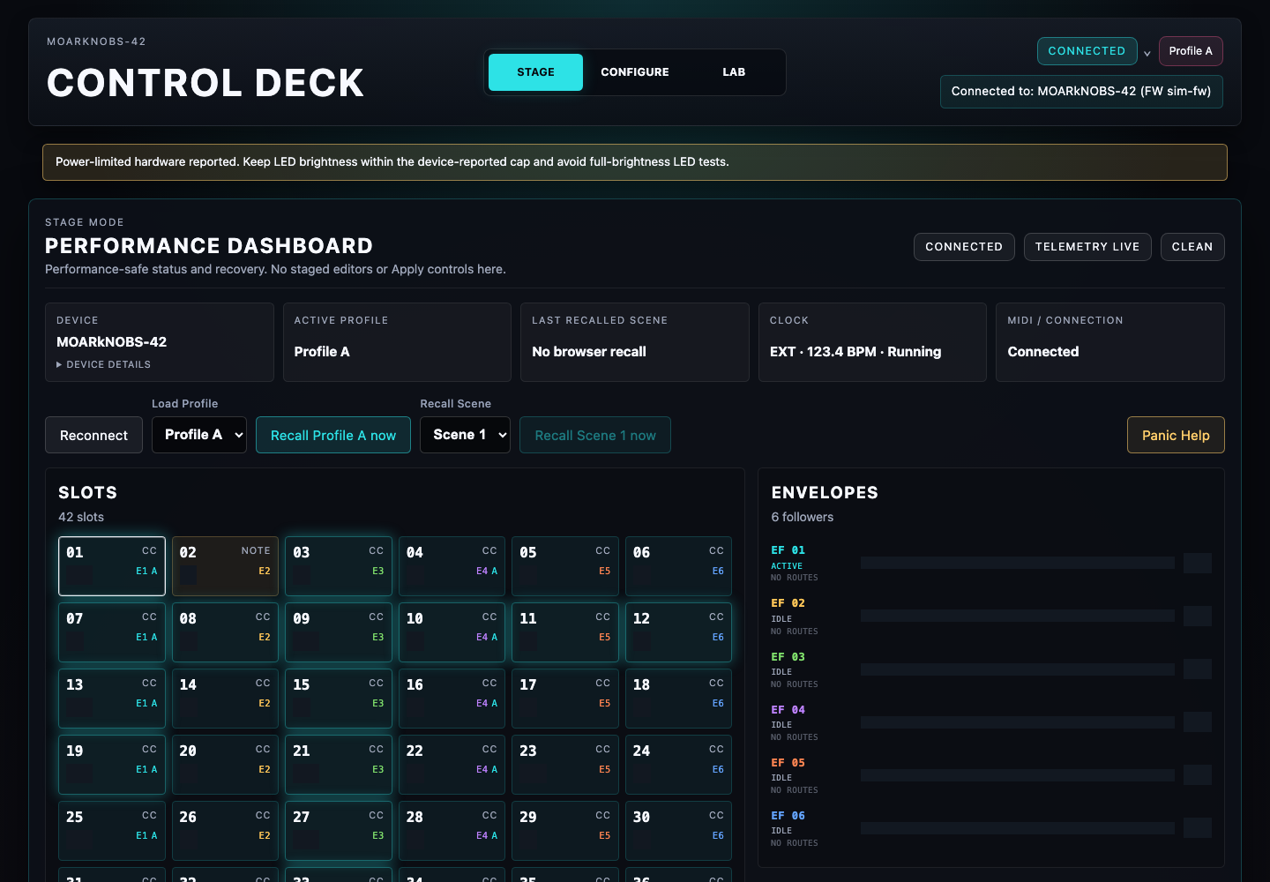
App/tests/visual-snapshots/stage-1440x1000.png
