bseverns/MOARkNOBS-42/firmware/src/biquadfilter_t.cpp

#include <Arduino.h>
#include "BiquadFilter.h"
#include "Globals.h"

/*
BiquadFilter math test

Confirms coefficient calculations and internal state for low-, high-
and band-pass modes—the same filters that EnvelopeFollower and EfVoice
lean on when `initializeRuntime()` spins up the DSP chain.

Build and upload with PlatformIO environment `teensy40_biquad_test`.
Requires only a board capable of Serial output (Teensy 4.0 recommended);
no other hardware is needed.

See `firmware/README.md` under "Test Philosophy (and Real Talk)" for
the full list of available test sketches.
*/

void setup() {
    Serial.begin(SERIAL_BAUD);
    while (!Serial) {
        // wait for serial
    }
    Serial.println("=== BiquadFilter Test ===");

    const float freq = 1000.0f;
    const float sampleRate = 48000.0f;
    const float q = 0.707f;

    bool passLP = false;
    bool passHP = false;
    bool passBP = false;

    auto runTest = [&](BiquadFilter::FilterType type) -> bool {
        BiquadFilter filter;
        filter.configure(type, freq, sampleRate, q);

        float omega = 2.0f * PI * freq / sampleRate;
        float cos_omega = cosf(omega);
        float sin_omega = sinf(omega);
        float alpha = sin_omega / (2.0f * q);

        float a0 = 0.0f;
        float a1 = 0.0f;
        float a2 = 0.0f;
        float b1 = -2.0f * cos_omega;
        float b2 = 1.0f - alpha;

        switch (type) {
        case BiquadFilter::LOWPASS:
            a0 = (1.0f - cos_omega) / 2.0f;
            a1 = 1.0f - cos_omega;
            a2 = a0;
            break;
        case BiquadFilter::HIGHPASS:
            a0 = (1.0f + cos_omega) / 2.0f;
            a1 = -(1.0f + cos_omega);
            a2 = a0;
            break;
        case BiquadFilter::BANDPASS:
            a0 = alpha;
            a1 = 0.0f;
            a2 = -alpha;
            break;
        }

        float norm = 1.0f + alpha;
        a0 /= norm;
        a1 /= norm;
        a2 /= norm;
        b1 /= norm;
        b2 /= norm;

        float firstOut = filter.process(1.0f);
        bool coefCheck = fabsf(firstOut - a0) < 1e-5f;

        for (int i = 0; i < 50; ++i) {
            filter.process(0.0f);
        }
        bool settleCheck = fabsf(filter.process(0.0f)) < 1e-3f;

        return coefCheck && settleCheck;
    };

    passLP = runTest(BiquadFilter::LOWPASS);
    passHP = runTest(BiquadFilter::HIGHPASS);
    passBP = runTest(BiquadFilter::BANDPASS);

    if (passLP && passHP && passBP) {
        Serial.println("BiquadFilter tests PASS");
    } else {
        Serial.println("BiquadFilter tests FAIL");
    }
}

void loop() {}
