bseverns/MOARkNOBS-42/firmware/src/ConfigManager.cpp

// ConfigManager is the repo's long-term memory. It shows how we marshal structs
// into EEPROM, guard against corruption, and fan those bytes back into runtime
// objects without leaking pointers or faith. Treat this file as a crash course
// in embedded persistence: every helper explains why the bounds checks exist
// and how legacy migrations keep older builds from bricking.

#include "ConfigManager.h"
#include "BoardPowerProfile.h"
#include "ProfileStorage.h"
#include "ProfileMigration.h"
#include "ProfileModulationStorage.h"
#include "EnvelopeFollower.h"
#include "ARGMixer.h" // reuse the shared sanitizeSlotArg implementation
#include "LFO/LFOManager.h"
#include "storage/EepromStorageBackend.h"
#if defined(CONFIG_STORAGE_LITTLEFS)
#include "storage/LittleFsStorageBackend.h"
#endif
#include <algorithm>
#include <cmath>
#include <cstddef>
#include <vector>
#include "Log.h"

extern ConfigManager configManager;

// Weak hook lets test firmware skip the heavyweight EF voice refresh logic.
#if defined(__GNUC__) || defined(__clang__)
extern void refreshEfVoicesFromConfig() __attribute__((weak));
#else
extern void refreshEfVoicesFromConfig();
#endif

// Update one slot's EF settings, persist them, and notify any runtime cache
// that mirrors follower assignments.
void saveSlotEfSettings(uint8_t slotIndex, const MIDISlot::EfSettings &settings) {
    if (slotIndex >= NUM_SLOTS) {
        return;
    }

    MIDISlot &slot = configManager.getSlot(slotIndex);
    slot.efSettings = settings;
    configManager.saveSlot(slotIndex, slot);

#if defined(__GNUC__) || defined(__clang__)
    if (refreshEfVoicesFromConfig != nullptr) {
        refreshEfVoicesFromConfig();
    }
#else
    refreshEfVoicesFromConfig();
#endif
}

namespace {
StorageBackend *gStorageBackendOverride = nullptr;

StorageBackend &activeStorageBackend() {
    if (gStorageBackendOverride) {
        return *gStorageBackendOverride;
    }
#if defined(CONFIG_STORAGE_LITTLEFS)
    static LittleFsStorageBackend littleFsBackend;
    // LittleFsStorageBackend already delegates reads/writes to EEPROM when it
    // cannot initialize. Returning it consistently preserves that fallback
    // while keeping its readiness detail visible to diagnostics and hosts.
    return littleFsBackend;
#else
    static EepromStorageBackend defaultBackend;
    return defaultBackend;
#endif
}

uint8_t storageRead(int address) { return activeStorageBackend().read(address); }

void storageUpdate(int address, uint8_t value) { activeStorageBackend().update(address, value); }

template <typename T> void storageGet(int address, T &value) {
    activeStorageBackend().readBytes(address, &value, sizeof(T));
}

template <typename T> void storagePut(int address, const T &value) {
    activeStorageBackend().writeBytes(address, &value, sizeof(T));
}

constexpr uint16_t kLegacyConfigVersion = 0x0003;
constexpr float kMinFilterFrequency = EF_FILTER_FREQ_MIN_HZ;
constexpr float kMaxFilterFrequency = EF_FILTER_FREQ_MAX_HZ;
constexpr float kMinFilterQ = EF_FILTER_Q_MIN;
constexpr float kMaxFilterQ = EF_FILTER_Q_MAX;
constexpr int kUnassignedEnvelope = -1;
// Computes CRC-16 with the Modbus-flavored 0xA001 polynomial to keep our
// saved configuration blocks honest. Peek at docs/EEPROMLayout.md to see
// where the checksum bunkers down.
static uint16_t crc16_update(uint16_t crc, uint8_t data) {
    crc ^= data;
    for (uint8_t i = 0; i < 8; ++i) {
        if (crc & 1) {
            crc = (crc >> 1) ^ 0xA001;
        } else {
            crc >>= 1;
        }
    }
    return crc;
}

// filterCoefficientsLookSane and maybeRescueFilterTailFromLegacy live in
// SchemaMigration.cpp — they are only needed during boot migration.

// sanitizeProfileEfSettings, sanitizeProfileData, and computeProfileCrc
// are now in ProfileStorage.cpp / ProfileStorage.h.

// Clamp the filter payload that gets mirrored into slot storage and the legacy
// tail region.
SlotEnvelopePayload sanitizeEnvelopePayloadImpl(const SlotEnvelopePayload &payload) {
    SlotEnvelopePayload sanitized = payload;
    if (sanitized.filterType > static_cast<uint8_t>(EnvelopeFollower::BANDPASS)) {
        sanitized.filterType = static_cast<uint8_t>(EnvelopeFollower::LINEAR);
    }
    if (!std::isfinite(sanitized.frequency)) {
        sanitized.frequency = kMinFilterFrequency;
    }
    sanitized.frequency = constrain(sanitized.frequency, kMinFilterFrequency, kMaxFilterFrequency);
    if (!std::isfinite(sanitized.q)) {
        sanitized.q = kMinFilterQ;
    }
    sanitized.q = constrain(sanitized.q, kMinFilterQ, kMaxFilterQ);
    return sanitized;
}

// Persist the shared "tail" filter payload used by older layouts and recovery
// helpers, returning the sanitized version that was actually written.
SlotEnvelopePayload persistFilterTailImpl(const SlotEnvelopePayload &payload) {
    SlotEnvelopePayload sanitized = sanitizeEnvelopePayloadImpl(payload);
    storageUpdate(EEPROM_ENVELOPE_TYPES, sanitized.filterType);
    storagePut(EEPROM_FILTER_FREQ, sanitized.frequency);
    storagePut(EEPROM_FILTER_Q, sanitized.q);
    return sanitized;
}

// Validate whether an EF filter enum is one of the persisted values we know how
// to map back into runtime behavior.
bool filterTypeIsValid(MIDISlot::EfSettings::FilterType type) {
    switch (type) {
    case MIDISlot::EfSettings::FilterType::Linear:
    case MIDISlot::EfSettings::FilterType::OppositeLinear:
    case MIDISlot::EfSettings::FilterType::Exponential:
    case MIDISlot::EfSettings::FilterType::Random:
    case MIDISlot::EfSettings::FilterType::Lowpass:
    case MIDISlot::EfSettings::FilterType::Highpass:
    case MIDISlot::EfSettings::FilterType::Bandpass:
        return true;
    }
    return false;
}

// Extract just the persistable filter payload from a full EF settings block.
SlotEnvelopePayload settingsToPayload(const MIDISlot::EfSettings &settings) {
    SlotEnvelopePayload payload{};
    payload.filterType = static_cast<uint8_t>(settings.filterType);
    payload.frequency = settings.frequency;
    payload.q = settings.q;
    return payload;
}

// Push a persistable filter payload back into a full EF settings block.
void applyPayloadToSettings(const SlotEnvelopePayload &payload, MIDISlot::EfSettings &settings) {
    settings.filterType = static_cast<MIDISlot::EfSettings::FilterType>(
        constrain(payload.filterType, static_cast<uint8_t>(0),
                  static_cast<uint8_t>(MIDISlot::EfSettings::FilterType::Bandpass)));
    settings.frequency = payload.frequency;
    settings.q = payload.q;
}

// Clamp a full EF settings block so corrupt EEPROM or imported JSON cannot
// destabilize follower runtime math.
MIDISlot::EfSettings sanitizeEfSettings(const MIDISlot::EfSettings &settings) {
    // Clamp EF settings so corrupt EEPROM data doesn't destabilize runtime.
    MIDISlot::EfSettings sanitized = settings;
    if (!filterTypeIsValid(sanitized.filterType)) {
        sanitized.filterType = MIDISlot::EfSettings::FilterType::Linear;
    }
    SlotEnvelopePayload payload = sanitizeEnvelopePayloadImpl(settingsToPayload(sanitized));
    applyPayloadToSettings(payload, sanitized);
    sanitized.oversample = static_cast<uint8_t>(constrain(static_cast<int>(sanitized.oversample),
                                                          static_cast<int>(EF_OVERSAMPLE_MIN),
                                                          static_cast<int>(EF_OVERSAMPLE_MAX)));
    if (!std::isfinite(sanitized.smoothing)) {
        sanitized.smoothing = 0.2f;
    }
    sanitized.smoothing = constrain(sanitized.smoothing, 0.0f, 1.0f);
    if (!std::isfinite(sanitized.baseline)) {
        sanitized.baseline = 0.0f;
    }
    if (!std::isfinite(sanitized.gain)) {
        sanitized.gain = 1.0f;
    }
    // Validate EF mode and auto-cal flags.
    if (sanitized.efMode > static_cast<uint8_t>(EnvelopeFollower::EFMode::Follower)) {
        sanitized.efMode = static_cast<uint8_t>(EnvelopeFollower::EFMode::Peak);
    }
    sanitized.autoBaseline = sanitized.autoBaseline ? 1 : 0;
    sanitized.autoGain = sanitized.autoGain ? 1 : 0;
    sanitized.gateThreshold = constrain(sanitized.gateThreshold, 0, 127);
    sanitized.gateHysteresis = constrain(sanitized.gateHysteresis, 0, 127);
    sanitized.activityThreshold = constrain(sanitized.activityThreshold, 0, 127);
    sanitized.gainTarget = constrain(sanitized.gainTarget, 0, 127);
    if (sanitized.destinationMode > static_cast<uint8_t>(EfDestinationMode::Centered)) {
        sanitized.destinationMode = static_cast<uint8_t>(EfDestinationMode::AddClamp);
    }
    sanitized.attackMs = static_cast<uint16_t>(constrain(static_cast<int>(sanitized.attackMs),
                                                         static_cast<int>(EF_TIME_MIN_MS),
                                                         static_cast<int>(EF_TIME_MAX_MS)));
    sanitized.releaseMs = static_cast<uint16_t>(constrain(static_cast<int>(sanitized.releaseMs),
                                                          static_cast<int>(EF_TIME_MIN_MS),
                                                          static_cast<int>(EF_TIME_MAX_MS)));
    sanitized.rmsWindowMs = static_cast<uint16_t>(constrain(static_cast<int>(sanitized.rmsWindowMs),
                                                            static_cast<int>(EF_TIME_MIN_MS),
                                                            static_cast<int>(EF_TIME_MAX_MS)));
    sanitized.baselineTauMs = static_cast<uint16_t>(
        constrain(static_cast<int>(sanitized.baselineTauMs), static_cast<int>(EF_TIME_MIN_MS),
                  static_cast<int>(EF_TIME_MAX_MS)));
    sanitized.gainTauMs = static_cast<uint16_t>(constrain(static_cast<int>(sanitized.gainTauMs),
                                                          static_cast<int>(EF_TIME_MIN_MS),
                                                          static_cast<int>(EF_TIME_MAX_MS)));
    return sanitized;
}

// Runtime-only EF fields get a lighter sanitization pass because they are not
// supposed to contain the full persisted tuning set.
MIDISlot::EfRuntime sanitizeEfRuntime(const MIDISlot::EfRuntime &runtime) {
    MIDISlot::EfRuntime sanitized = runtime;
    if (sanitized.followerIndex < -1) {
        sanitized.followerIndex = -1;
    }
    return sanitized;
}
} // namespace

void ConfigManager::setStorageBackend(StorageBackend *backend) {
    gStorageBackendOverride = backend;
}

StorageBackend *ConfigManager::getStorageBackend() { return &activeStorageBackend(); }

// Constructor
ConfigManager::ConfigManager(uint8_t numPots, uint8_t numButtons)
    : _numPots(numPots), _numButtons(numButtons) {}

// Centralized EEPROM health check
bool ConfigManager::checkEEPROMHealth(bool backup, uint16_t base) {
    int address = base + (backup ? EEPROM_MAGIC_ADDRESS + 2 : EEPROM_MAGIC_ADDRESS);
    uint16_t magic = storageRead(address) << 8 | storageRead(address + 1);
    return (magic == (backup ? EEPROM_MAGIC_BACKUP : EEPROM_MAGIC_PRIMARY));
}

bool ConfigManager::hasHealthyConfigurationCopy(bool backup, uint16_t base) const {
    if (!const_cast<ConfigManager *>(this)->checkEEPROMHealth(backup, base)) {
        return false;
    }
    const int offset = base + (backup ? EEPROM_BACKUP_START : EEPROM_START_ADDRESS);
    uint16_t version = 0;
    uint16_t storedCrc = 0;
    storageGet(offset + EEPROM_CONFIG_VERSION, version);
    storageGet(offset + EEPROM_CONFIG_CRC, storedCrc);
    if (version != CONFIG_VERSION) {
        return false;
    }
    uint16_t calculated = 0xFFFF;
    for (uint8_t i = 0; i < _numPots; ++i) {
        calculated = crc16_update(calculated, storageRead(offset + EEPROM_POT_CHANNELS + i));
    }
    for (uint8_t i = 0; i < _numPots; ++i) {
        calculated = crc16_update(calculated, storageRead(offset + EEPROM_POT_CC + i));
    }
    if (base == EEPROM_PROFILE_START(0)) {
        calculated = crc16_update(calculated, storageRead(offset + EEPROM_ACTIVE_PROFILE));
        calculated = crc16_update(calculated, storageRead(offset + EEPROM_LED_MODE));
    }
    return calculated == storedCrc;
}

// Write magic number to EEPROM
void ConfigManager::writeMagicNumber(bool backup, uint16_t base) {
    int address = base + (backup ? EEPROM_MAGIC_ADDRESS + 2 : EEPROM_MAGIC_ADDRESS);
    uint16_t magic = backup ? EEPROM_MAGIC_BACKUP : EEPROM_MAGIC_PRIMARY;
    storageUpdate(address, (magic >> 8) & 0xFF);
    storageUpdate(address + 1, magic & 0xFF);
}

// Save configuration with verification and backup
void ConfigManager::saveConfiguration() {
    // Refresh backup first so an interrupted or partially verified primary write cannot leave
    // recovery with only a stale/corrupt copy.
    uint16_t base = EEPROM_PROFILE_START(0);
    writeEEPROM(true, base);
    writeMagicNumber(true, base);
    writeEEPROM(false, base); // Write primary
    writeMagicNumber(false, base);

    // Verify
    std::vector<uint8_t> temp;
    if (!loadConfiguration(temp, base)) {
        LOG_PRINTLN(
            "{\"type\":\"info\",\"message\":\"Primary EEPROM write failed, saving to backup.\"}");
        writeEEPROM(true, base);
        writeMagicNumber(true, base);
    }
}

// Load configuration (primary)
bool ConfigManager::loadConfiguration(std::vector<uint8_t> &potChannels, uint16_t base) {
    // Recovery order: primary -> backup -> defaults.
    if (checkEEPROMHealth(false, base)) {
        readEEPROM(false, base);
        bool needsRewrite = false;
        if (_stored.version != CONFIG_VERSION) {
            if (_stored.version == kLegacyConfigVersion) {
                needsRewrite = true;
            } else {
                LOG_PRINTLN("{\"type\":\"status\",\"level\":\"warn\",\"message\":\"Config version "
                            "mismatch, trying backup.\"}");
                return loadBackupConfiguration(potChannels, base);
            }
        }
        bool includeProfile = (base == EEPROM_PROFILE_START(0));
        if (_stored.crc != calculateCRC(includeProfile)) {
            LOG_PRINTLN(
                "{\"type\":\"status\",\"level\":\"warn\",\"message\":\"Config CRC mismatch, "
                "trying backup.\"}");
            return loadBackupConfiguration(potChannels, base);
        }
        if (_stored.activeProfile >= NUM_PROFILES) {
            _stored.activeProfile = 0;
            needsRewrite = true;
        }
        potChannels.clear();
        for (uint8_t i = 0; i < _numPots; i++) {
            potChannels.push_back(_stored.potChannels[i]);
        }
        if (needsRewrite) {
            _stored.version = CONFIG_VERSION;
            saveConfiguration();
        }
        _lastLoadSource = LoadSource::kPrimary;
        return true;
    }
    LOG_PRINTLN("{\"type\":\"status\",\"level\":\"warn\",\"message\":\"Primary EEPROM corrupted, "
                "trying backup.\"}");
    return loadBackupConfiguration(potChannels, base);
}

// Load configuration (backup)
bool ConfigManager::loadBackupConfiguration(std::vector<uint8_t> &potChannels, uint16_t base) {
    // Backup path mirrors primary validation and emits a recovery event for UI messaging.
    if (checkEEPROMHealth(true, base)) {
        readEEPROM(true, base);
        bool needsRewrite = false;
        if (_stored.version != CONFIG_VERSION) {
            if (_stored.version == kLegacyConfigVersion) {
                needsRewrite = true;
            } else {
                LOG_PRINTLN("{\"type\":\"error\",\"message\":\"Backup config version mismatch.\"}");
                resetConfiguration(potChannels, true);
                return false;
            }
        }
        bool includeProfile = (base == EEPROM_PROFILE_START(0));
        if (_stored.crc != calculateCRC(includeProfile)) {
            LOG_PRINTLN("{\"type\":\"error\",\"message\":\"Backup CRC mismatch.\"}");
            resetConfiguration(potChannels, true);
            return false;
        }
        if (_stored.activeProfile >= NUM_PROFILES) {
            _stored.activeProfile = 0;
            needsRewrite = true;
        }
        potChannels.clear();
        for (uint8_t i = 0; i < _numPots; i++) {
            potChannels.push_back(_stored.potChannels[i]);
        }
        // A successful backup load should repair the primary copy so future boots/profile swaps
        // stop tripping the same recovery path.
        writeEEPROM(false, base);
        writeMagicNumber(false, base);
        if (needsRewrite) {
            _stored.version = CONFIG_VERSION;
            saveConfiguration();
        }
        _lastRecoveryEvent = RecoveryEvent::kBackupRestored;
        _lastLoadSource = LoadSource::kBackup;
        return true;
    }
    LOG_PRINTLN(
        "{\"type\":\"error\",\"message\":\"Backup EEPROM corrupted, resetting to defaults.\"}");
    resetConfiguration(potChannels, true);
    return false;
}

// Internal read from EEPROM
void ConfigManager::readEEPROM(bool backup, uint16_t base) {
    int offset = base + (backup ? EEPROM_BACKUP_START : EEPROM_START_ADDRESS);
    for (uint8_t i = 0; i < NUM_POTS; i++) {
        if (i >= _numPots) break;
        _stored.potChannels[i] = storageRead(offset + EEPROM_POT_CHANNELS + i);
        _stored.potCCNumbers[i] = storageRead(offset + EEPROM_POT_CC + i);
    }
    if (base == EEPROM_PROFILE_START(0)) {
        _stored.activeProfile = storageRead(offset + EEPROM_ACTIVE_PROFILE);
        _stored.ledMode = storageRead(offset + EEPROM_LED_MODE);
        uint8_t idleFloor = storageRead(offset + EEPROM_EF_IDLE_FLOOR);
        uint8_t idleFloorCheck = storageRead(offset + EEPROM_EF_IDLE_FLOOR_CHECK);
        g_efIdleFloor = ((idleFloor ^ 0xFF) == idleFloorCheck && idleFloor <= 127)
                            ? idleFloor
                            : EF_IDLE_FLOOR_DEFAULT;
        uint8_t usbMidiOut = storageRead(offset + EEPROM_USB_MIDI_OUT);
        uint8_t usbMidiOutCheck = storageRead(offset + EEPROM_USB_MIDI_OUT_CHECK);
        g_usbMidiOutEnabled =
            ((usbMidiOut ^ 0xFF) == usbMidiOutCheck && usbMidiOut <= 1) ? (usbMidiOut != 0) : true;
    }
    storageGet(offset + EEPROM_CONFIG_VERSION, _stored.version);
    storageGet(offset + EEPROM_CONFIG_CRC, _stored.crc);
}

// Internal write to EEPROM
void ConfigManager::writeEEPROM(bool backup, uint16_t base) {
    int offset = base + (backup ? EEPROM_BACKUP_START : EEPROM_START_ADDRESS);
    uint16_t crc = calculateCRC(base == EEPROM_PROFILE_START(0));
    for (uint8_t i = 0; i < _numPots; i++) {
        storageUpdate(offset + EEPROM_POT_CHANNELS + i, _stored.potChannels[i]);
        storageUpdate(offset + EEPROM_POT_CC + i, _stored.potCCNumbers[i]);
    }
    if (base == EEPROM_PROFILE_START(0)) {
        storageUpdate(offset + EEPROM_ACTIVE_PROFILE, _stored.activeProfile);
        storageUpdate(offset + EEPROM_LED_MODE, _stored.ledMode);
        storageUpdate(offset + EEPROM_EF_IDLE_FLOOR, g_efIdleFloor);
        storageUpdate(offset + EEPROM_EF_IDLE_FLOOR_CHECK, g_efIdleFloor ^ 0xFF);
        storageUpdate(offset + EEPROM_USB_MIDI_OUT, g_usbMidiOutEnabled ? 1 : 0);
        storageUpdate(offset + EEPROM_USB_MIDI_OUT_CHECK, (g_usbMidiOutEnabled ? 1 : 0) ^ 0xFF);
    }
    storagePut(offset + EEPROM_CONFIG_VERSION, (uint16_t)CONFIG_VERSION);
    storagePut(offset + EEPROM_CONFIG_CRC, crc);
    _stored.version = CONFIG_VERSION;
    _stored.crc = crc;
}

uint16_t ConfigManager::calculateCRC(bool includeProfile) const {
    uint16_t crc = 0xFFFF;
    for (uint8_t i = 0; i < _numPots; ++i) {
        crc = crc16_update(crc, _stored.potChannels[i]);
    }
    for (uint8_t i = 0; i < _numPots; ++i) {
        crc = crc16_update(crc, _stored.potCCNumbers[i]);
    }
    if (includeProfile) {
        crc = crc16_update(crc, _stored.activeProfile);
        crc = crc16_update(crc, _stored.ledMode);
    }
    return crc;
}

// Load a profile block into the current working config
bool ConfigManager::loadProfile(uint8_t id) {
    // Clamp to valid profile slots so EEPROM reads stay in range.
    if (id >= NUM_PROFILES) {
        id = 0;
    }
    uint16_t base = EEPROM_PROFILE_START(id);
    const bool includeProfileFields = (base == EEPROM_PROFILE_START(0));
    const StoredConfig prior = _stored;
    const uint8_t priorIdleFloor = g_efIdleFloor;
    const bool priorUsbMidiOutEnabled = g_usbMidiOutEnabled;

    const auto restorePrior = [&]() {
        _stored = prior;
        g_efIdleFloor = priorIdleFloor;
        g_usbMidiOutEnabled = priorUsbMidiOutEnabled;
    };
    const auto loadValidated = [&](bool backup) {
        if (!checkEEPROMHealth(backup, base)) {
            return false;
        }
        readEEPROM(backup, base);
        return _stored.version == CONFIG_VERSION &&
               _stored.crc == calculateCRC(includeProfileFields);
    };

    if (loadValidated(false)) {
        return true;
    }
    restorePrior();
    if (loadValidated(true)) {
        return true;
    }
    restorePrior();
    LOG_PRINTLN(
        "{\"type\":\"status\",\"level\":\"warn\",\"message\":\"Profile slot corrupted, using "
        "current configuration.\"}");
    return false;
}

// Save the current config into the given profile block
void ConfigManager::saveProfile(uint8_t id) {
    // Clamp to valid profile slots so EEPROM writes stay in range.
    if (id >= NUM_PROFILES) {
        id = 0;
    }
    uint16_t base = EEPROM_PROFILE_START(id);
    // Capture the new slot map in the backup region first so an interrupted write
    // still leaves a complete copy to recover from.
    writeEEPROM(true, base);
    writeMagicNumber(true, base);
    writeEEPROM(false, base);
    writeMagicNumber(false, base);
    std::vector<uint8_t> temp;
    if (!loadConfiguration(temp, base)) {
        LOG_PRINTLN("{\"type\":\"info\",\"message\":\"Primary EEPROM corrupted after save; backup "
                    "contains latest profile.\"}");
    }
}

bool ConfigManager::loadProfileSettings(uint8_t id, ProfileData &profile) const {
    if (id >= NUM_PROFILES) return false;

    const uint16_t base = EEPROM_PROFILE_SETTINGS_START(id);
    ProfileData decoded{};
    const ProfileDecodeResult result =
        decodeStoredProfile(activeStorageBackend(), base, slots, decoded);
    if (result == ProfileDecodeResult::InsufficientStorage) {
        LOG_PRINTLN("{\"type\":\"status\",\"level\":\"error\",\"message\":\"Profile storage "
                    "capacity is insufficient.\"}");
    }
    if (result != ProfileDecodeResult::Success) return false;

    profile = decoded;
    return true;
}

bool ConfigManager::saveProfileSettings(uint8_t id, const ProfileData &profile) {
    // Save a sanitized profile payload with a fresh CRC.
    if (id >= NUM_PROFILES) {
        return false;
    }
    ProfileData sanitized = sanitizeProfileData(profile);
    sanitized.crc = computeProfileCrc(sanitized);
    const uint16_t base = EEPROM_PROFILE_SETTINGS_START(id);
    if (!activeStorageBackend().contains(base, sizeof(sanitized))) {
        LOG_PRINTLN("{\"type\":\"status\",\"level\":\"error\",\"message\":\"Profile storage "
                    "capacity is insufficient.\"}");
        return false;
    }
    storagePut(base, sanitized);
    ProfileData verified{};
    storageGet(base, verified);
    return verified.version == PROFILE_SETTINGS_VERSION &&
           verified.crc == computeProfileCrc(verified);
}

FLASHMEM bool ConfigManager::loadProfileModulation(uint8_t id,
                                          ProfileModulationExtension &extension) const {
    if (id >= NUM_PROFILES) return false;
    const uint16_t base = EEPROM_PROFILE_MODULATION_START(id);
    if (!activeStorageBackend().contains(base, sizeof(ProfileModulationExtension))) return false;
    uint16_t storedVersion = 0;
    storageGet(base, storedVersion);
    if (storedVersion == 0x0001) {
        uint8_t legacyBytes[4 + sizeof(ProfileSlotModSettings) * NUM_SLOTS]{};
        for (size_t i = 0; i < sizeof(legacyBytes); ++i) {
            legacyBytes[i] = activeStorageBackend().read(base + i);
        }
        return decodeProfileModulationV1(legacyBytes, sizeof(legacyBytes), extension);
    }
    ProfileModulationExtension stored{};
    storageGet(base, stored);
    if (stored.version != PROFILE_MODULATION_VERSION ||
        stored.crc != computeProfileModulationCrc(stored)) return false;
    extension = sanitizeProfileModulation(stored);
    extension.crc = computeProfileModulationCrc(extension);
    return true;
}

FLASHMEM bool ConfigManager::saveProfileModulation(
    uint8_t id, const ProfileModulationExtension &extension) {
    if (id >= NUM_PROFILES) return false;
    ProfileModulationExtension sanitized = sanitizeProfileModulation(extension);
    sanitized.crc = computeProfileModulationCrc(sanitized);
    const uint16_t base = EEPROM_PROFILE_MODULATION_START(id);
    if (!activeStorageBackend().contains(base, sizeof(sanitized))) return false;
    storagePut(base, sanitized);
    ProfileModulationExtension verified{};
    storageGet(base, verified);
    return verified.version == PROFILE_MODULATION_VERSION &&
           verified.crc == computeProfileModulationCrc(verified);
}

void ConfigManager::setActiveProfile(uint8_t id) {
    // Persist the profile index so power cycles restore the last slot.
    if (id >= NUM_PROFILES) {
        id = 0;
    }
    _stored.activeProfile = id;
    saveConfiguration();
}

// Initialize configuration
void ConfigManager::begin(std::vector<uint8_t> &potChannels) {
    sanitizeSlotArena();
    // Hydrate profile-A configuration before boot code asks which persisted
    // profile is active. Blank storage still follows the existing later reset
    // path; any stamped copy is validated through primary/backup recovery.
    if (checkEEPROMHealth(false, EEPROM_PROFILE_START(0)) ||
        checkEEPROMHealth(true, EEPROM_PROFILE_START(0))) {
        loadConfiguration(potChannels);
    } else {
        potChannels.clear();
        for (uint8_t i = 0; i < _numPots; ++i) {
            potChannels.push_back(_stored.potChannels[i]);
        }
    }
    // Load every MIDISlot from EEPROM into our in-RAM array.
    for (uint8_t i = 0; i < NUM_SLOTS; ++i) {
        loadSlot(i, slots[i]);
    }
}

void ConfigManager::loadSlot(uint8_t idx, MIDISlot &dest) {
    MIDISlot temp{};
    const int address = static_cast<int>(EEPROM_SLOT_BASE + idx * SLOT_EEPROM_SIZE);
    storageGet(address, temp);
    if (temp.sysexLength > SysExTemplate::kMaxLength) {
        temp.sysexLength = 0;
        temp.sysexTemplate.fill(0);
    }
    temp.efSettings = sanitizeEfSettings(temp.efSettings);
    temp.ef = sanitizeEfRuntime(temp.ef);
    temp.setEnvelopeFollowerIndex(temp.ef.followerIndex);
    temp.arg = sanitizeSlotArg(temp.arg);
    temp.lfo = sanitizeSlotLfoConfig(temp.lfo);
    dest = temp;
    if (dest.arpNote > 127)
        dest.arpNote = dest.data1;
}

void ConfigManager::saveSlot(uint8_t idx, const MIDISlot &src) {
    MIDISlot sanitized = src;
    if (sanitized.sysexLength > SysExTemplate::kMaxLength) {
        sanitized.sysexLength = SysExTemplate::kMaxLength;
    }
    for (uint8_t i = sanitized.sysexLength; i < SysExTemplate::kMaxLength; ++i) {
        sanitized.sysexTemplate[i] = 0;
    }
    sanitized.efSettings = sanitizeEfSettings(sanitized.efSettings);
    sanitized.ef = sanitizeEfRuntime(sanitized.ef);
    sanitized.setEnvelopeFollowerIndex(sanitized.ef.followerIndex);
    sanitized.arg = sanitizeSlotArg(sanitized.arg);
    sanitized.lfo = sanitizeSlotLfoConfig(sanitized.lfo);
    const int address = static_cast<int>(EEPROM_SLOT_BASE + idx * SLOT_EEPROM_SIZE);
    storagePut(address, sanitized);
    slots[idx] = sanitized;
}

// Potentiometer accessors
uint8_t ConfigManager::getPotChannel(uint8_t potIndex) const {
    return _stored.potChannels.at(potIndex);
}

uint8_t ConfigManager::getPotCCNumber(uint8_t potIndex) const {
    return _stored.potCCNumbers.at(potIndex);
}

void ConfigManager::setPotChannel(uint8_t potIndex, uint8_t channel) {
    if (potIndex < _numPots) {
        _stored.potChannels[potIndex] = channel;
        if (potIndex < slots.size()) {
            MIDISlot &slot = slots[potIndex];
            if (slot.midiChannel != channel) {
                slot.midiChannel = channel;
                saveSlot(potIndex, slot);
            }
        }
    }
}

void ConfigManager::setPotChannelLive(uint8_t potIndex, uint8_t channel) {
    if (potIndex < _numPots) {
        _stored.potChannels[potIndex] = channel;
        if (potIndex < slots.size()) {
            slots[potIndex].midiChannel = channel;
        }
    }
}

void ConfigManager::setPotCCNumber(uint8_t potIndex, uint8_t ccNumber) {
    if (potIndex < _numPots) {
        _stored.potCCNumbers[potIndex] = ccNumber;
        if (potIndex < slots.size()) {
            MIDISlot &slot = slots[potIndex];
            if (slot.data1 != ccNumber) {
                slot.data1 = ccNumber;
                saveSlot(potIndex, slot);
            }
        }
    }
}

void ConfigManager::setPotCCNumberLive(uint8_t potIndex, uint8_t ccNumber) {
    if (potIndex < _numPots) {
        _stored.potCCNumbers[potIndex] = ccNumber;
        if (potIndex < slots.size()) {
            slots[potIndex].data1 = ccNumber;
        }
    }
}

// Envelope settings
bool ConfigManager::loadEnvelopeSettings(std::map<int, MIDISlot::EfSettings> &potToEnvelopeMap,
                                         std::vector<EnvelopeFollower> &envelopes) {
    bool allFound = true;

    potToEnvelopeMap.clear();
    for (uint8_t potIndex = 0; potIndex < NUM_POTS; ++potIndex) {
        int storedValue = storageRead(EEPROM_ENVELOPE_ASSIGNMENTS + potIndex);
        int envelopeIndex = (storedValue == 0xFF) ? kUnassignedEnvelope : storedValue;
        MIDISlot::EfSettings settings = {};
        if (potIndex < slots.size()) {
            settings = slots[potIndex].efSettings;
            settings.followerIndex = slots[potIndex].ef.followerIndex;
        }
        if (envelopeIndex >= 0 && envelopeIndex < static_cast<int>(envelopes.size())) {
            settings.followerIndex = static_cast<int8_t>(envelopeIndex);
            settings = sanitizeEfSettings(settings);
            potToEnvelopeMap.emplace(potIndex, settings);
            if (potIndex < slots.size()) {
                slots[potIndex].efSettings = settings;
                slots[potIndex].setEnvelopeFollowerIndex(settings.followerIndex);
            }
        } else if (potIndex < slots.size()) {
            slots[potIndex].setEnvelopeFollowerIndex(-1);
        }
    }

    for (size_t envIndex = 0; envIndex < envelopes.size(); ++envIndex) {
        float baseline;
        storageGet(EEPROM_EF_BASELINES + envIndex * sizeof(float), baseline);

        envelopes[envIndex].setVref(g_vref); // always refresh Vref
        if (std::isfinite(baseline)) {
            envelopes[envIndex].setBaseline(baseline);
            envelopeConfig.baselines[envIndex] = baseline;
        } else {
            envelopeConfig.baselines[envIndex] = 0.0f;
            allFound = false;
        }
    }

    for (auto &entry : potToEnvelopeMap) {
        auto &settings = entry.second;
        const int follower = settings.followerIndex;
        if (follower < 0 || follower >= static_cast<int>(envelopes.size())) {
            continue;
        }
        settings.baseline = envelopes[follower].getBaseline();
        settings = sanitizeEfSettings(settings);
        envelopes[follower].configureFromEfSettings(settings);
        if (static_cast<size_t>(entry.first) < slots.size()) {
            slots[entry.first].efSettings = settings;
            slots[entry.first].setEnvelopeFollowerIndex(settings.followerIndex);
        }
    }
    return allFound;
}

void ConfigManager::saveEnvelopeSettings(
    const std::map<int, MIDISlot::EfSettings> &potToEnvelopeMap,
    const std::vector<EnvelopeFollower> &envelopes) {
    constexpr uint8_t kUnassignedMarker = 0xFF;
    for (uint8_t potIndex = 0; potIndex < NUM_POTS; ++potIndex) {
        auto it = potToEnvelopeMap.find(potIndex);
        int envelopeIndex = kUnassignedEnvelope;
        if (it != potToEnvelopeMap.end()) {
            envelopeIndex = it->second.followerIndex;
        }
        uint8_t storedValue =
            (envelopeIndex >= 0 && envelopeIndex < static_cast<int>(envelopes.size()))
                ? static_cast<uint8_t>(envelopeIndex)
                : kUnassignedMarker;
        storageUpdate(EEPROM_ENVELOPE_ASSIGNMENTS + potIndex, storedValue);

        if (potIndex < slots.size()) {
            MIDISlot &slot = slots[potIndex];
            if (it != potToEnvelopeMap.end()) {
                MIDISlot::EfSettings sanitized = sanitizeEfSettings(it->second);
                slot.efSettings = sanitized;
                if (envelopeIndex >= 0 && envelopeIndex < static_cast<int>(envelopes.size())) {
                    slot.setEnvelopeFollowerIndex(static_cast<int8_t>(envelopeIndex));
                    slot.efSettings.baseline = envelopes[envelopeIndex].getBaseline();
                } else {
                    slot.setEnvelopeFollowerIndex(-1);
                }
            } else {
                slot.setEnvelopeFollowerIndex(-1);
            }
        }
    }
    for (size_t i = 0; i < envelopes.size(); ++i) {
        envelopeConfig.baselines[i] = envelopes[i].getBaseline();
        storagePut(EEPROM_EF_BASELINES + i * sizeof(float), envelopeConfig.baselines[i]);
    }
}

void ConfigManager::saveEnvelopeBaseline(uint8_t envIndex, float baseline) {
    if (envIndex < NUM_ENVELOPES) {
        envelopeConfig.baselines[envIndex] = baseline;
        storagePut(EEPROM_EF_BASELINES + envIndex * sizeof(float), baseline);
    }
}

// LED settings
void ConfigManager::loadLEDSettings(uint8_t &brightness, CRGB &color) {
    brightness =
        std::min<uint8_t>(storageRead(EEPROM_LED_BRIGHTNESS), BoardPowerProfile::kLedBrightnessCap);
    color.r = storageRead(EEPROM_LED_COLOR);
    color.g = storageRead(EEPROM_LED_COLOR + 1);
    color.b = storageRead(EEPROM_LED_COLOR + 2);
}

void ConfigManager::saveLEDSettings(uint8_t brightness, CRGB color) {
    storageUpdate(EEPROM_LED_BRIGHTNESS,
                  std::min<uint8_t>(brightness, BoardPowerProfile::kLedBrightnessCap));
    storageUpdate(EEPROM_LED_COLOR, color.r);
    storageUpdate(EEPROM_LED_COLOR + 1, color.g);
    storageUpdate(EEPROM_LED_COLOR + 2, color.b);
}

void ConfigManager::setLedMode(LedMode mode) {
    setLedModeLive(mode);
    storageUpdate(EEPROM_LED_MODE, _stored.ledMode);
}

void ConfigManager::setLedModeLive(LedMode mode) {
    _stored.ledMode = static_cast<uint8_t>(sanitizeLedMode(mode));
}

LedMode ConfigManager::getLedMode() const {
    return sanitizeLedMode(static_cast<LedMode>(_stored.ledMode));
}

void ConfigManager::setEfIdleFloor(uint8_t floor) {
    setEfIdleFloorLive(floor);
    storageUpdate(EEPROM_EF_IDLE_FLOOR, g_efIdleFloor);
    storageUpdate(EEPROM_EF_IDLE_FLOOR_CHECK, g_efIdleFloor ^ 0xFF);
}

void ConfigManager::setEfIdleFloorLive(uint8_t floor) {
    g_efIdleFloor = static_cast<uint8_t>(constrain(static_cast<int>(floor), 0, 127));
}

uint8_t ConfigManager::getEfIdleFloor() const { return g_efIdleFloor; }

void ConfigManager::setUsbMidiOutEnabled(bool enabled) {
    setUsbMidiOutEnabledLive(enabled);
    storageUpdate(EEPROM_USB_MIDI_OUT, enabled ? 1 : 0);
    storageUpdate(EEPROM_USB_MIDI_OUT_CHECK, (enabled ? 1 : 0) ^ 0xFF);
}

void ConfigManager::setUsbMidiOutEnabledLive(bool enabled) { g_usbMidiOutEnabled = enabled; }

// Reset configuration to defaults
void ConfigManager::resetConfiguration(std::vector<uint8_t> &potChannels,
                                       bool recordRecoveryEvent) {
    StorageBackend *storage = getStorageBackend();
    const bool transactional = storage->supportsTransactions();
    const bool transactionStarted = transactional && storage->beginTransaction();
    if (recordRecoveryEvent) {
        _lastRecoveryEvent = RecoveryEvent::kDefaultsLoaded;
        _lastLoadSource = LoadSource::kDefaults;
    }
    potChannels.clear();
    for (uint8_t i = 0; i < NUM_POTS; i++) {
        if (i >= _numPots) break;
        setPotChannel(i, 1);  // Default to channel 1
        setPotCCNumber(i, 0); // Default to CC 0
    }
    seedSlotEnvelopePayloads(static_cast<uint8_t>(EnvelopeFollower::LINEAR), kMinFilterFrequency,
                             1.0f);
    _stored.activeProfile = 0;
    _stored.ledMode = static_cast<uint8_t>(LedMode::Static);
    g_efIdleFloor = EF_IDLE_FLOOR_DEFAULT;
    g_usbMidiOutEnabled = true;
    saveConfiguration();
    if (transactionStarted && !storage->commitTransaction()) {
        storage->abortTransaction();
    }
}

ConfigManager::RecoveryEvent ConfigManager::consumeRecoveryEvent() {
    RecoveryEvent event = _lastRecoveryEvent;
    _lastRecoveryEvent = RecoveryEvent::kNone;
    return event;
}

// Mode and ARG methods
void ConfigManager::setMode(uint8_t mode) {
    setModeLive(mode);
    storageUpdate(EEPROM_ARG_MODE, legacyArg.mode);
}

void ConfigManager::setModeLive(uint8_t mode) { legacyArg.mode = mode; }

uint8_t ConfigManager::getMode() const { return legacyArg.mode; }

void ConfigManager::setARGMethod(uint8_t method) {
    setARGMethodLive(method);
    storageUpdate(EEPROM_ARG_METHOD, legacyArg.method);
}

void ConfigManager::setARGMethodLive(uint8_t method) {
    legacyArg.method = method;
    SlotARGConfig defaults{};
    defaults.enabled = legacyArg.enable;
    defaults.method = static_cast<ARGMethod>(legacyArg.method);
    defaults.sourceA = legacyArg.sourceA;
    defaults.sourceB = legacyArg.sourceB;
    defaults = sanitizeSlotArg(defaults);
    legacyArg.method = static_cast<uint8_t>(defaults.method);
}

uint8_t ConfigManager::getARGMethod() const { return legacyArg.method; }

void ConfigManager::setARGEnable(uint8_t enable) {
    setARGEnableLive(enable);
    storageUpdate(EEPROM_ARG_ENABLE, legacyArg.enable);
}

void ConfigManager::setARGEnableLive(uint8_t enable) { legacyArg.enable = enable ? 1 : 0; }

uint8_t ConfigManager::getARGEnable() const { return legacyArg.enable; }

void ConfigManager::setEnvelopePair(uint8_t envA, uint8_t envB) {
    setEnvelopePairLive(envA, envB);
    storageUpdate(EEPROM_ARG_ENV_A, legacyArg.sourceA);
    storageUpdate(EEPROM_ARG_ENV_B, legacyArg.sourceB);
}

void ConfigManager::setEnvelopePairLive(uint8_t envA, uint8_t envB) {
    uint8_t safeA = static_cast<uint8_t>(constrain(static_cast<int>(envA), 0, NUM_ENVELOPES - 1));
    uint8_t safeB = static_cast<uint8_t>(constrain(static_cast<int>(envB), 0, NUM_ENVELOPES - 1));
    if (NUM_ENVELOPES > 1 && safeA == safeB) {
        safeB = static_cast<uint8_t>((safeA + 1) % NUM_ENVELOPES);
    }
    legacyArg.sourceA = safeA;
    legacyArg.sourceB = safeB;
}

uint8_t ConfigManager::getEnvelopeA() const {
    int pin = envelopeAnalogPin(legacyArg.sourceA);
    if (pin < 0)
        pin = legacyArg.sourceA;
    return static_cast<uint8_t>(pin);
}

uint8_t ConfigManager::getEnvelopeB() const {
    int pin = envelopeAnalogPin(legacyArg.sourceB);
    if (pin < 0)
        pin = legacyArg.sourceB;
    return static_cast<uint8_t>(pin);
}

void ConfigManager::saveMIDISlots(const MIDISlot *slots, size_t count) {
    if (slots == nullptr || count == 0) {
        return;
    }
    // Clamp to maximum number of slots to avoid overflow
    if (count > 42) {
        count = 42;
    }
    for (size_t i = 0; i < count; ++i) {
        saveSlot(static_cast<uint8_t>(i), slots[i]);
    }
}

void ConfigManager::loadMIDISlots(MIDISlot *slots, size_t count) {
    if (slots == nullptr || count == 0) {
        return;
    }
    if (count > 42) {
        count = 42;
    }
    for (size_t i = 0; i < count; ++i) {
        loadSlot(static_cast<uint8_t>(i), slots[i]);
    }
}

SlotEnvelopePayload ConfigManager::getSlotEnvelopePayload(uint8_t idx) const {
    if (idx >= slots.size()) {
        SlotEnvelopePayload fallback{};
        return sanitizeEnvelopePayload(fallback);
    }
    return sanitizeEnvelopePayload(settingsToPayload(slots[idx].efSettings));
}

void ConfigManager::setSlotEnvelopePayload(uint8_t idx, const SlotEnvelopePayload &payload) {
    if (idx >= slots.size()) {
        return;
    }
    SlotEnvelopePayload sanitized = sanitizeEnvelopePayload(payload);
    MIDISlot &slot = slots[idx];
    applyPayloadToSettings(sanitized, slot.efSettings);
    slot.efSettings = sanitizeEfSettings(slot.efSettings);
    slot.ef = sanitizeEfRuntime(slot.ef);
    saveSlot(idx, slots[idx]);
}

SlotEnvelopePayload ConfigManager::setAllSlotEnvelopePayloads(uint8_t filterType, float freq,
                                                              float q) {
    return seedSlotEnvelopePayloads(filterType, freq, q);
}

void ConfigManager::setSlotLive(uint8_t idx, const MIDISlot &slot) {
    if (idx >= slots.size()) {
        return;
    }
    MIDISlot sanitized = slot;
    if (sanitized.sysexLength > SysExTemplate::kMaxLength) {
        sanitized.sysexLength = SysExTemplate::kMaxLength;
    }
    for (uint8_t i = sanitized.sysexLength; i < SysExTemplate::kMaxLength; ++i) {
        sanitized.sysexTemplate[i] = 0;
    }
    sanitized.efSettings = sanitizeEfSettings(sanitized.efSettings);
    sanitized.ef = sanitizeEfRuntime(sanitized.ef);
    sanitized.setEnvelopeFollowerIndex(sanitized.ef.followerIndex);
    sanitized.arg = sanitizeSlotArg(sanitized.arg);
    sanitized.lfo = sanitizeSlotLfoConfig(sanitized.lfo);
    slots[idx] = sanitized;
}

SlotEnvelopePayload ConfigManager::sanitizeEnvelopePayload(const SlotEnvelopePayload &payload) {
    return sanitizeEnvelopePayloadImpl(payload);
}

SlotEnvelopePayload ConfigManager::sanitizeFilterTail(const SlotEnvelopePayload &payload) {
    return sanitizeEnvelopePayload(payload);
}

SlotEnvelopePayload ConfigManager::persistFilterTail(const SlotEnvelopePayload &payload) {
    return persistFilterTailImpl(payload);
}

// loadLegacyARGSettings, migrateLegacyARGSettings, slotLooksSane,
// sanitizeSlotArena, wipeSlotRegion, migrateLegacySlotPayloads,
// seedSlotEnvelopePayloads, sanitizeEnvelopePayload, and wipeProfileBlocks
// are now implemented in SchemaMigration.cpp.
