bseverns/MOARkNOBS-42/firmware/src/Runtime.cpp

#include "Runtime.h"

#include <Arduino.h>
#include <algorithm>
#include <array>
#include <cstdint>
#include <cmath>
#include <imxrt.h>
#include "ButtonManager.h"
#include "ConfigManager.h"
#include "DiagnosticRecord.h"
#include "DisplayManager.h"
#include "EfFilterControl.h"
#include "LEDManager.h"
#include "MIDIHandler.h"
#include "MachineParameterService.h"
#include "MidiInputRouter.h"
#include "PotentiometerManager.h"
#include "Arpeggiator.h"
#include "Utility.h"
#include "TimeUtils.h"
#include "Log.h"
#include "Globals.h"
#include "LFO/LFOManager.h"
#include "ARGMixer.h"
#include "Protocol.h"
#include "UI.h"
#include "Scheduler.h"
#include "SlotModulationResolver.h"
#include "ModulationTransportPolicy.h"
#include "bench_log_latency.h"
#include "interop/SeedBoxLink.h"

#include <TimerOne.h>

// Runtime.cpp is the execution layer for the standalone instrument path.
//
// Reading order:
// 1. small private queues/flags and clock helpers
// 2. boot-time bring-up in initializeRuntime()
// 3. high-frequency service lanes (MIDI, followers, LFOs)
// 4. mid-tier musical processing (envelopes, note-offs, internal clock)
// 5. diagnostics and health reporting
//
// This keeps the file aligned with Runtime.h and with the scheduler-driven
// shape named in firmware_main.cpp.

namespace {

volatile uint8_t midiServiceRequestCount = 0;
constexpr uint8_t kMaxMidiServiceRequestCount = 0xFF;
uint32_t lastMidiDropAlertCount = 0;
uint32_t lastMidiTaskOverrunAlertCount = 0;
uint32_t lastUartOverrunAlertCount = 0;
unsigned long internalClockNextTick = 0;

template <typename T> void storageGet(int address, T &value) {
    ConfigManager::getStorageBackend()->readBytes(address, &value, sizeof(T));
}

struct PendingNoteOff {
    uint32_t dueTime = 0;
    uint8_t note = 0;
    uint8_t channel = 0;
    bool active = false;
};

constexpr size_t kPendingNoteOffCapacity = 64;
std::array<PendingNoteOff, kPendingNoteOffCapacity> pendingNoteOffs{};
std::array<uint32_t, NUM_ENVELOPES> envelopeFollowerSampledAtUs{};

struct SlotModulationFrame {
    bool efActive = false;
    uint8_t efValue = 0;
    std::array<bool, LFOManager::kMaxLFOs> lfoActive{};
    std::array<uint8_t, LFOManager::kMaxLFOs> lfoValue{{64, 64}};
    uint8_t lastEmittedValue = 0xFF;
    unsigned long lastEmitMs = 0;
    SlotModulationResult result{};
    bool resultValid = false;
};

std::array<SlotModulationFrame, NUM_SLOTS> slotModulationFrames{};
constexpr unsigned long kSlotModulationMinSendIntervalMs = 9;
using SlotTransportPolicy = ModulationTransportPolicy<NUM_SLOTS>;
static_assert(SlotTransportPolicy::kCapacityBytes == MIDIHandler::kMaxOutgoingSysExBytes,
              "Transport capacity must admit one maximum bounded SysEx frame");
SlotTransportPolicy modulationTransport;

void resetModulationTransport() {
    modulationTransport.reset(now());
}

void queueMidiServiceRequest() {
    // ISR-safe flagging: keep the interrupt short and let `processMIDI()` grab the work later.
    if (midiServiceRequestCount < kMaxMidiServiceRequestCount) {
        ++midiServiceRequestCount;
    }
    ++g_systemDiagnostics.midiServiceRequests;
    if (midiServiceRequestCount > g_systemDiagnostics.midiServiceMaxBacklog) {
        g_systemDiagnostics.midiServiceMaxBacklog = midiServiceRequestCount;
    }
}

// Consume and account for every ISR-raised request from task context.
uint8_t consumeMidiServiceRequests() {
    uint8_t pending = 0;
    noInterrupts();
    pending = midiServiceRequestCount;
    midiServiceRequestCount = 0;
    interrupts();
    return pending;
}

} // namespace

bool queuePendingNoteOff(uint8_t note, uint8_t channel, unsigned long delayMs);

namespace {
volatile unsigned long statusLedPulseDeadline = 0;
unsigned long statusLedBootDeadline = 0;
unsigned long statusLedBeatPulseDeadline = 0;
uint32_t statusLedLastClockTickCount = 0;

constexpr unsigned long kStatusLedBootHoldMs = 3000UL;
constexpr unsigned long kStatusLedHeartbeatHalfPeriodMs = 1000UL;
constexpr unsigned long kStatusLedClockPulseMs = 120UL;
} // namespace

void requestStatusLEDPulse(uint16_t durationMs) {
    // Blink the status LED from any task as diagnostics fire.
    statusLedPulseDeadline = now() + durationMs;
}

namespace {
bool deadlineStillActive(unsigned long deadline, unsigned long current) {
    return deadline != 0 && static_cast<long>(current - deadline) < 0;
}

bool externalClockDominant() {
    return g_followExternalClock && midiHandler.isClockRunning() &&
           midiHandler.hasExternalClockSignal();
}

bool internalClockDominant() { return g_tappedBPM > 0.0f && !externalClockDominant(); }

bool performanceClockActive() { return externalClockDominant() || internalClockDominant(); }

uint8_t resolveSlotNoteVelocity(uint8_t slotIndex, const MIDISlot &slot) {
    uint8_t velo = 125;
    if (slotIndex < efVoices.size() && efVoices[slotIndex].hasRendered()) {
        velo = efVoices[slotIndex].latestLevel();
    } else if (slot.ef.followerIndex >= 0 &&
               static_cast<size_t>(slot.ef.followerIndex) < envelopeFollowers.size()) {
        velo = static_cast<uint8_t>(constrain(
            envelopeFollowers[static_cast<size_t>(slot.ef.followerIndex)].getEnvelopeLevel(), 0,
            127));
    }
    int lfoVelocityOffset = static_cast<int>(lroundf(g_lfoVelocityShift * 32.0f));
    return static_cast<uint8_t>(constrain(velo + velocityShift + lfoVelocityOffset, 0, 127));
}

uint16_t resolveClockedNoteGateMs() {
    float bpm = 0.0f;
    if (externalClockDominant()) {
        bpm = midiHandler.externalClockBpm();
    }
    if (bpm <= 0.0f) {
        bpm = g_tappedBPM;
    }
    if (bpm <= 0.0f) {
        return 120;
    }
    const float quarterNoteMs = 60000.0f / bpm;
    return static_cast<uint16_t>(constrain(lroundf(quarterNoteMs * 0.45f), 40L, 400L));
}

void emitNoteSlot(uint8_t slotIndex, MIDISlot &slot, unsigned long gateMs) {
    const uint8_t note = static_cast<uint8_t>(slot.data1 % 128);
    const uint8_t velocity = resolveSlotNoteVelocity(slotIndex, slot);
    int lfoChanceOffset = static_cast<int>(lroundf(g_lfoNoteChance * 40.0f));
    int effectiveChance = constrain(static_cast<int>(changeProbability) + lfoChanceOffset, 0, 100);
    if (random(100U) >= static_cast<uint8_t>(effectiveChance)) {
        return;
    }
    // Admit the note only after its release has a reserved queue entry.  A
    // dropped Note Off is worse than a dropped trigger: it can leave a voice
    // stuck indefinitely.
    if (queuePendingNoteOff(note, slot.midiChannel, gateMs)) {
        midiHandler.sendNoteOn(note, velocity, slot.midiChannel);
    }
}

uint16_t midiValueToRawAdc(uint8_t value) {
    return static_cast<uint16_t>((static_cast<uint32_t>(value) * 1023U + 63U) / 127U);
}

int16_t midiValueToPitchBend(uint8_t value) {
    const int bend =
        static_cast<int>(lroundf((static_cast<float>(value) / 127.0f) * 16383.0f)) - 8192;
    return static_cast<int16_t>(constrain(bend, -8192, 8191));
}

uint8_t slotModulationTransportCost(const MIDISlot &slot, uint8_t value) {
    switch (slot.type) {
    case MIDIMessageType::CC:
    case MIDIMessageType::PitchBend:
    case MIDIMessageType::ModWheel:
        return 3;
    case MIDIMessageType::Note:
        return 6; // Account for both the admitted Note On and its reserved Note Off.
    case MIDIMessageType::ProgramChange:
    case MIDIMessageType::Aftertouch:
        return 2;
    case MIDIMessageType::NRPN:
    case MIDIMessageType::RPN:
        return 12;
    case MIDIMessageType::SysEx: {
        std::array<uint8_t, SysExTemplate::kMaxLength> msg{};
        return buildSysExPayload(slot, midiValueToRawAdc(value), msg.data(), msg.size());
    }
    case MIDIMessageType::OFF:
    default:
        return 0;
    }
}

bool emitSlotModulationValue(uint8_t slotIndex, uint8_t value) {
    if (slotIndex >= NUM_SLOTS) {
        return false;
    }
    MIDISlot &slot = configManager.getSlot(slotIndex);
    if (!slot.active) {
        return false;
    }

    bool emitted = true;
    switch (slot.type) {
    case MIDIMessageType::CC:
        midiHandler.sendControlChange(slot.data1, value, slot.midiChannel);
        break;
    case MIDIMessageType::Note: {
        const uint8_t note = static_cast<uint8_t>(slot.data1 % 128);
        if (queuePendingNoteOff(note, slot.midiChannel, 100)) {
            midiHandler.sendNoteOn(note, value, slot.midiChannel);
        } else {
            emitted = false;
        }
        break;
    }
    case MIDIMessageType::PitchBend:
        midiHandler.sendPitchBend(midiValueToPitchBend(value), slot.midiChannel);
        break;
    case MIDIMessageType::ProgramChange:
        midiHandler.sendProgramChange(value, slot.midiChannel);
        break;
    case MIDIMessageType::Aftertouch:
        midiHandler.sendAftertouch(value, slot.midiChannel);
        break;
    case MIDIMessageType::ModWheel:
        midiHandler.sendModWheel(value, slot.midiChannel);
        break;
    case MIDIMessageType::NRPN: {
        const uint16_t param = static_cast<uint16_t>(slot.data1) << 7;
        const uint16_t paramValue = static_cast<uint16_t>(value) << 7;
        midiHandler.sendNRPN(param, paramValue, slot.midiChannel);
        break;
    }
    case MIDIMessageType::RPN: {
        const uint16_t param = static_cast<uint16_t>(slot.data1) << 7;
        const uint16_t paramValue = static_cast<uint16_t>(value) << 7;
        midiHandler.sendRPN(param, paramValue, slot.midiChannel);
        break;
    }
    case MIDIMessageType::SysEx: {
        std::array<uint8_t, SysExTemplate::kMaxLength> msg{};
        uint8_t length = buildSysExPayload(slot, midiValueToRawAdc(value), msg.data(), msg.size());
        if (length > 0) {
            midiHandler.sendSysEx(msg.data(), length);
        } else {
            emitted = false;
        }
        break;
    }
    case MIDIMessageType::OFF:
    default:
        emitted = false;
        break;
    }

    if (emitted && slotIndex < NUM_POTS) {
        ledAnimator.setPotTarget(slotIndex, value);
    }
    return emitted;
}

bool isUnconfiguredClockedSlot(const MIDISlot &slot) {
    if (slot.midiChannel != 1 || slot.data1 != 0) {
        return false;
    }
    return slot.type == MIDIMessageType::CC || slot.type == MIDIMessageType::Note;
}

void emitClockedNoteSlots(uint32_t quarterEvents) {
    if (quarterEvents == 0 || !performanceClockActive()) {
        return;
    }
    constexpr uint32_t kMaxClockedQuarterEventsPerPass = 4;
    const uint32_t boundedEvents = std::min(quarterEvents, kMaxClockedQuarterEventsPerPass);
    if (quarterEvents > boundedEvents) {
        g_systemDiagnostics.droppedClockedQuarterEvents += quarterEvents - boundedEvents;
    }
    const unsigned long gateMs = resolveClockedNoteGateMs();
    for (uint32_t beat = 0; beat < boundedEvents; ++beat) {
        for (uint8_t slotIndex = 0; slotIndex < NUM_SLOTS; ++slotIndex) {
            if (arpeggiator.isActive(slotIndex)) {
                continue;
            }
            MIDISlot &slot = configManager.getSlot(slotIndex);
            if (!slot.active) {
                continue;
            }
            if (isUnconfiguredClockedSlot(slot)) {
                continue;
            }
            if (slot.type == MIDIMessageType::Note) {
                emitNoteSlot(slotIndex, slot, gateMs);
                continue;
            }

            int rawValue = slotIndex < NUM_POTS ? potentiometerManager.getLastValue(slotIndex) : -1;
            const uint8_t value = rawValue >= 0 ? Utility::mapToMidiValue(rawValue)
                                                : static_cast<uint8_t>(slot.data1);
            emitSlotModulationValue(slotIndex, value);
        }
    }
}
} // namespace

// Keep the status LED pulse alive until its deadline expires, layered on top of a base liveness
// pattern that is meaningful on the bench.
void serviceStatusLEDPulse() {
    const unsigned long current = now();
    const bool bootHoldActive = deadlineStillActive(statusLedBootDeadline, current);
    const bool diagnosticPulseActive = deadlineStillActive(statusLedPulseDeadline, current);
    const bool clockActive = externalClockDominant() || internalClockDominant();
    const uint32_t currentClockTickCount = midiHandler.clockTickCount();

    if (clockActive) {
        if (currentClockTickCount != statusLedLastClockTickCount) {
            if ((currentClockTickCount / 24U) != (statusLedLastClockTickCount / 24U)) {
                statusLedBeatPulseDeadline = current + kStatusLedClockPulseMs;
            }
            statusLedLastClockTickCount = currentClockTickCount;
        }
    } else {
        statusLedLastClockTickCount = currentClockTickCount;
    }

    const bool beatPulseActive = deadlineStillActive(statusLedBeatPulseDeadline, current);
    const bool heartbeatActive = ((current / kStatusLedHeartbeatHalfPeriodMs) % 2UL) == 0UL;

    if (!diagnosticPulseActive) {
        statusLedPulseDeadline = 0;
    }
    if (!beatPulseActive) {
        statusLedBeatPulseDeadline = 0;
    }

    const bool ledOn = bootHoldActive || diagnosticPulseActive || beatPulseActive ||
                       (!clockActive && heartbeatActive);
    ledManager.setStatusLED(ledOn);
}

// Turn monotonically increasing diagnostic counters into one-shot user-visible alerts.
void checkDiagnosticsForAlerts() {
    // Report any diagnostic counters over Serial and pulse the status LED so students can spot
    // trouble.
    const SystemDiagnostics diag = captureDiagnosticsSnapshot();

    const uint32_t midiDrop = diag.midiDropCount;
    if (midiDrop != lastMidiDropAlertCount) {
        LOG_PRINTF("{\"diagnostic\":\"midi_drop\",\"count\":%lu}\n",
                   static_cast<unsigned long>(midiDrop));
        requestStatusLEDPulse();
        lastMidiDropAlertCount = midiDrop;
    }

    const uint32_t midiTaskOverruns = diag.midiTaskOverrunCount;
    const uint32_t maxMidiMicros = diag.maxProcessMidiMicros;
    if (midiTaskOverruns != lastMidiTaskOverrunAlertCount) {
        LOG_PRINTF("{\"diagnostic\":\"midi_task_overrun\",\"count\":%lu,\"max_us\":%lu}\n",
                   static_cast<unsigned long>(midiTaskOverruns),
                   static_cast<unsigned long>(maxMidiMicros));
        requestStatusLEDPulse();
        lastMidiTaskOverrunAlertCount = midiTaskOverruns;
    }

    const uint32_t uartOverruns = diag.uartOverrunCount;
    if (uartOverruns != lastUartOverrunAlertCount) {
        LOG_PRINTF("{\"diagnostic\":\"uart_overrun\",\"count\":%lu}\n",
                   static_cast<unsigned long>(uartOverruns));
        requestStatusLEDPulse();
        lastUartOverrunAlertCount = uartOverruns;
    }
}

// Wire the runtime managers together once globals, EEPROM, and UI state are ready.
void initializeRuntime(bool baselinesLoaded) {
    // Initialize runtime services now that the UI and EEPROM-backed state are ready.
    resetModulationTransport();
    pinMode(VREF_ADC_PIN, INPUT);
    for (int pin : ENVELOPE_ANALOG_PINS) {
#if defined(INPUT_PULLDOWN)
        pinMode(pin, INPUT_PULLDOWN);
#else
        pinMode(pin, INPUT);
#endif
    }
    g_vref = Utility::readVrefADC(VREF_ADC_PIN);

    midiHandler.begin();
    midiHandler.setDiagnostics(&g_systemDiagnostics);
    midiHandler.setDisplayManager(&displayManager);
    midiInputRouter.setCallbacks(MachineParameterService::apply, MachineParameterService::read);
    midiHandler.setControlChangeInputCallback(
        [](MidiInputPort port, uint8_t channel, uint8_t controller, uint8_t value) {
            midiInputRouter.routeControlChange(port, channel, controller, value);
        });
    if (g_seedboxInteropEnabled) {
        seedbox::interop::mn42::SeedBoxLink::instance().begin(&midiHandler);
    }
    lfoManager.attachMIDI(&midiHandler);
    lfoManager.setSlotValueCallback([](uint8_t lfoIndex, uint8_t slotIndex, uint8_t value) {
        if (slotIndex >= slotModulationFrames.size() ||
            lfoIndex >= slotModulationFrames[slotIndex].lfoActive.size()) {
            return;
        }
        SlotModulationFrame &frame = slotModulationFrames[slotIndex];
        frame.lfoActive[lfoIndex] = true;
        frame.lfoValue[lfoIndex] = value;
    });
    ledAnimator.setMode(configManager.getLedMode());
    statusLedBootDeadline = now() + kStatusLedBootHoldMs;
    statusLedPulseDeadline = 0;
    statusLedBeatPulseDeadline = 0;
    statusLedLastClockTickCount = midiHandler.clockTickCount();

    potentiometerManager.setMidiCallback(
        [&](uint8_t /*ccNumber*/, uint8_t value, uint16_t rawValue, uint8_t potIdx) {
            auto &slot = configManager.getSlot(potIdx);
            if (!slot.active)
                return;

            // A modulated slot is emitted only by the control-rate resolver.
            // The pot manager still owns the physical baseline cache.
            const bool hasFixedLfo = std::any_of(
                slot.lfo.lfo.begin(), slot.lfo.lfo.end(),
                [](const SlotLfoLane &lane) { return lane.enabled(); });
            if (slot.getEnvelopeFollowerIndex() >= 0 || hasFixedLfo ||
                lfoManager.slotIsRouted(potIdx)) {
                return;
            }

            switch (slot.type) {
            case MIDIMessageType::CC:
                midiHandler.sendControlChange(slot.data1, value, slot.midiChannel);
                break;

            case MIDIMessageType::Note:
                if (performanceClockActive()) {
                    break;
                }
                emitNoteSlot(potIdx, slot, 100);
                break;
            case MIDIMessageType::PitchBend: {
                int16_t bend = map(static_cast<int>(rawValue), 0, 1023, -8192, 8191);
                midiHandler.sendPitchBend(bend, slot.midiChannel);
                break;
            }

            case MIDIMessageType::ProgramChange:
                midiHandler.sendProgramChange(slot.data1, slot.midiChannel);
                break;

            case MIDIMessageType::Aftertouch: {
                uint8_t pres = Utility::mapToMidiValue(rawValue);
                midiHandler.sendAftertouch(pres, slot.midiChannel);
                break;
            }

            case MIDIMessageType::ModWheel: {
                uint8_t mod = Utility::mapToMidiValue(rawValue);
                midiHandler.sendModWheel(mod, slot.midiChannel);
                break;
            }

            case MIDIMessageType::NRPN: {
                uint16_t param = static_cast<uint16_t>(slot.data1) << 7;
                uint16_t val = static_cast<uint16_t>(Utility::mapToMidiValue(rawValue)) << 7;
                midiHandler.sendNRPN(param, val, slot.midiChannel);
                break;
            }

            case MIDIMessageType::RPN: {
                uint16_t param = static_cast<uint16_t>(slot.data1) << 7;
                uint16_t val = static_cast<uint16_t>(Utility::mapToMidiValue(rawValue)) << 7;
                midiHandler.sendRPN(param, val, slot.midiChannel);
                break;
            }

            case MIDIMessageType::SysEx: {
                std::array<uint8_t, SysExTemplate::kMaxLength> msg{};
                uint8_t length = buildSysExPayload(slot, rawValue, msg.data(), msg.size());
                if (length > 0) {
                    midiHandler.sendSysEx(msg.data(), length);
                }
                break;
            }

            default:
                break;
            }
        });

    potentiometerManager.loadFromEEPROM();

#if defined(MN42_DIAG_DISABLE_TIMER1_ISR) && (MN42_DIAG_DISABLE_TIMER1_ISR != 0)
    LOG_PRINTLN("{\"type\":\"diag\",\"code\":\"timer1_isr_disabled\"}");
#else
    Timer1.initialize(1000);
    Timer1.attachInterrupt(midiTimerISR);
#endif

    filter.configure(BiquadFilter::LOWPASS, 1000, 44100);

    for (auto &ef : envelopeFollowers) {
        ef.toggleActive(true);
        if (!baselinesLoaded) {
            ef.calibrate();
        }
    }
    float sf, sq;
    storageGet(EEPROM_FILTER_FREQ, sf);
    storageGet(EEPROM_FILTER_Q, sq);
    sf = constrain(sf, 20.0f, 5000.0f);
    sq = constrain(sq, 0.5f, 4.0f);
    for (auto &ef : envelopeFollowers)
        ef.configureFilter(sf, sq);

    for (uint8_t i = 0; i < NUM_SLOTS; i++) {
        if (potentiometerManager.getChannel(i) == 0)
            potentiometerManager.setChannel(i, 1);
        if (potentiometerManager.getCCNumber(i) > 127)
            potentiometerManager.setCCNumber(i, i % 128);
    }

    if (!configManager.loadConfiguration(potChannels)) {
        LOG_PRINTLN("EEPROM corrupted → resetting.");
        potentiometerManager.resetEEPROM();
    }

    switch (configManager.consumeRecoveryEvent()) {
    case ConfigManager::RecoveryEvent::kBackupRestored:
        displayManager.setTemporaryMessage("Config restored\nfrom backup", 3000);
        break;
    case ConfigManager::RecoveryEvent::kDefaultsLoaded:
        displayManager.setTemporaryMessage("EEPROM corrupted\ndefaults loaded", 4000);
        break;
    default:
        break;
    }

#if defined(MN42_DIAG_DISABLE_SCHEDULERS) && (MN42_DIAG_DISABLE_SCHEDULERS != 0)
    LOG_PRINTLN("{\"type\":\"diag\",\"code\":\"schedulers_disabled\"}");
#else
    initializeSchedulers();
#endif
}

// Timer ISR is intentionally tiny: it only requests service and leaves real work to task
// context.
void midiTimerISR() { queueMidiServiceRequest(); }

// High-frequency MIDI ingress/service lane.
void processMIDI() {
    // The high-tier scheduler already paces this lane. Keep the Timer1 request as an interrupt
    // breadcrumb, but do not make USB/DIN polling depend on that interrupt firing; otherwise USB
    // clock can be visible to the host while the firmware never drains it.
    const uint8_t requests = consumeMidiServiceRequests();
    ++g_systemDiagnostics.midiServiceExecutions;
    if (requests > 1) {
        g_systemDiagnostics.midiServiceCoalesced += requests - 1;
    }
    midiHandler.processIncomingMIDI();

    static uint32_t lastDisplayTick = 0;
    static uint32_t lastQuarterNoteTick = 0;
    uint32_t tickCount = midiHandler.clockTickCount();
    if (tickCount != lastDisplayTick) {
        // Catch-up path: if multiple clock ticks arrive between scheduler slices, advance by the
        // full delta to keep beat position stable.
        // Keep this section display-free so the high-priority MIDI service path never blocks on
        // I2C.
        uint32_t diff = tickCount - lastDisplayTick;
        lastDisplayTick = tickCount;

        lastClockTime = now();
        midiBeatPosition = (midiBeatPosition + diff) % 8;
        lastClockTime = now();
        midiHandler.clearClockTick();

        const uint32_t currentQuarterNoteTick = tickCount / 24U;
        if (currentQuarterNoteTick != lastQuarterNoteTick) {
            emitClockedNoteSlots(currentQuarterNoteTick - lastQuarterNoteTick);
            lastQuarterNoteTick = currentQuarterNoteTick;
        }
    }

    monitorSerialHealth();
}

// High-tier follower sampling lane.
void processEnvelopeFollowers() {
    // Fast follower pass runs in the high-tier scheduler; downstream MIDI mapping happens in
    // `processEnvelopes()` on the mid tier.
    constexpr size_t kFollowersPerPass = EF_FOLLOWERS_PER_PASS;
    static size_t nextFollowerIndex = 0;
    float gainTrim = 1.0f + g_lfoEfGainTrim;
    gainTrim = constrain(gainTrim, 0.0f, 2.0f);
    const size_t followerCount = envelopeFollowers.size();
    if (followerCount == 0) {
        return;
    }
    const size_t passes = std::min(kFollowersPerPass, followerCount);
    for (size_t offset = 0; offset < passes; ++offset) {
        const size_t idx = (nextFollowerIndex + offset) % followerCount;
        EnvelopeFollower &follower = envelopeFollowers[idx];
        if (!follower.getActiveState()) {
            envelopeFollowerReady[idx] = false;
            continue;
        }
        follower.setExternalGainTrim(gainTrim);
        follower.update();
        envelopeFollowerLevels[idx] = follower.getEnvelopeLevel();
        envelopeFollowerReady[idx] = true;
        envelopeFollowerSampledAtUs[idx] = micros();
    }
    nextFollowerIndex = (nextFollowerIndex + passes) % followerCount;
}

// High-tier LFO update lane.
void processLFOs() {
    // Route callbacks repopulate these flags from the current route table.
    // Clearing first also removes stale contributions immediately after a
    // route is deleted or a profile is switched.
    for (SlotModulationFrame &frame : slotModulationFrames) {
        frame.lfoActive.fill(false);
    }
    lfoManager.update(now());
    const LFOBus &bus = lfoManager.bus();
    g_lfoEfGainTrim = bus.efGainTrim;
    g_lfoArpSwing = bus.arpSwing;
    g_lfoVelocityShift = bus.velocityShift;
    g_lfoNoteChance = bus.noteChance;
    g_lfoArpGate = bus.arpGate;
    g_lfoJitterDepth = bus.jitterDepth;
    g_lfoJitterSmoothness = bus.jitterSmoothness;
    g_lfoValues[0] = lfoManager.normalizedValue(0);
    g_lfoValues[1] = lfoManager.normalizedValue(1);
    ledManager.setBrightnessModulator(1.0f);
}

// Shared delayed note-off queue used by both direct pot gestures and clocked note emission.
bool queuePendingNoteOff(uint8_t note, uint8_t channel, unsigned long delayMs) {
    uint32_t due = now() + delayMs;
    for (auto &entry : pendingNoteOffs) {
        if (!entry.active) {
            entry.active = true;
            entry.note = note;
            entry.channel = channel;
            entry.dueTime = due;
            return true;
        }
    }
    // Note-off queue overflow is treated as a dropped-MIDI diagnostic event.
    ++g_systemDiagnostics.midiDropCount;
    requestStatusLEDPulse();
    return false;
}

// Deferred cleanup lane for scheduled note endings.
void processPendingNoteOffs() {
    unsigned long current = now();
    for (auto &entry : pendingNoteOffs) {
        if (!entry.active)
            continue;
        if (static_cast<long>(current - entry.dueTime) >= 0) {
            midiHandler.sendNoteOff(entry.note, 0, entry.channel);
            entry.active = false;
        }
    }
}

// Mid-tier envelope-to-MIDI modulation lane.
void processEnvelopes() {
    for (SlotModulationFrame &frame : slotModulationFrames) {
        frame.efActive = false;
    }

    std::array<int, NUM_ENVELOPES> rawFollowerLevels{};
    std::array<uint8_t, NUM_ENVELOPES> followerLevels{};
    std::array<bool, NUM_ENVELOPES> followerReady{};
    for (size_t idx = 0; idx < envelopeFollowers.size(); ++idx) {
        rawFollowerLevels[idx] = envelopeFollowerLevels[idx];
        followerLevels[idx] =
            static_cast<uint8_t>(constrain(rawFollowerLevels[idx], 0, 127));
        followerReady[idx] = envelopeFollowerReady[idx];
        if (followerReady[idx]) {
            ledAnimator.setEnvelopeTarget(static_cast<uint8_t>(idx),
                                          constrain(rawFollowerLevels[idx], 0, 127));
        }
    }

    for (const auto &entry : potToEnvelopeMap) {
        const int potIndex = entry.first;
        const MIDISlot::EfSettings &settings = entry.second;
        const int envelopeIndex = settings.followerIndex;
        if (potIndex < 0 || potIndex >= NUM_POTS)
            continue;
        if (envelopeIndex >= 0 && envelopeIndex < static_cast<int>(envelopeFollowers.size())) {
            int currentPotReading = potentiometerManager.getLastValue(potIndex);
            if (currentPotReading < 0)
                continue;

            EnvelopeFollower *envelope = &envelopeFollowers[envelopeIndex];
            bool envelopeActive = envelope->getActiveState();

            if (!envelopeActive) {
                continue;
            }

            if (!followerReady[envelopeIndex]) {
                continue;
            }

            const MIDISlot &slot = configManager.getSlot(potIndex);
            uint8_t reactiveSource = followerLevels[envelopeIndex];
            if (slot.arg.enabled) {
                const SlotARGConfig arg = sanitizeSlotArg(slot.arg);
                if (!followerReady[arg.sourceA] || !followerReady[arg.sourceB]) {
                    continue;
                }
                reactiveSource = computeArgLevel(arg, followerLevels);
            }

            // ARG selects/computes the reactive input first; the slot-local
            // voice then performs its filtering and shaping exactly once.
            EfVoice &voice = efVoices[potIndex];
            voice.assignFollower(envelopeIndex);
            const float envelopeIntervalMs =
                hwConfig.envelopeTaskInterval > 0
                    ? static_cast<float>(hwConfig.envelopeTaskInterval)
                    : 1.0f;
            voice.setControlRateHz(1000.0f / envelopeIntervalMs);
            voice.syncSettings(slot.efSettings);
            voice.render(reactiveSource);

            if (potIndex >= NUM_SLOTS)
                continue;
            SlotModulationFrame &frame = slotModulationFrames[potIndex];
            frame.efActive = true;
            frame.efValue = voice.latestLevel();
#if BENCH_EF_LATENCY_LOG
            static bool headerPrinted = false;
            if (!headerPrinted) {
                benchEfLatencyHeader();
                headerPrinted = true;
            }
            benchEfLatencyLog(static_cast<uint8_t>(envelopeIndex),
                              static_cast<uint8_t>(potIndex), reactiveSource,
                              frame.efValue, envelopeFollowerSampledAtUs[envelopeIndex],
                              "resolver_cache");
#endif
        }
    }

    if (buttonContext.activePot < NUM_POTS) {
        int activePotReading = potentiometerManager.getLastValue(buttonContext.activePot);
        if (activePotReading >= 0) {
            uint8_t potMidiValue = Utility::mapToMidiValue(activePotReading);
            for (uint8_t i = 0; i < POT_LED_COUNT; ++i) {
                ledManager.setPotIndicator(i, potMidiValue);
            }
        }
    }
}

// Resolve and emit each modulated slot once per control-rate frame.
void processSlotModulation() {
    const unsigned long currentMs = now();
    modulationTransport.refill(currentMs);
    std::array<SlotTransportPolicy::Candidate, NUM_SLOTS> candidates{};

    // Resolve every slot first. Admission below operates on one latest value per slot, so a
    // deferred continuous destination is naturally coalesced instead of building a stale queue.
    for (uint8_t slotIndex = 0; slotIndex < NUM_SLOTS; ++slotIndex) {
        SlotModulationFrame &frame = slotModulationFrames[slotIndex];
        const bool hasLfo = std::any_of(frame.lfoActive.begin(), frame.lfoActive.end(),
                                       [](bool active) { return active; });
        const MIDISlot &slot = configManager.getSlot(slotIndex);
        const bool hasFixedLfo = std::any_of(
            slot.lfo.lfo.begin(), slot.lfo.lfo.end(),
            [](const SlotLfoLane &lane) { return lane.enabled(); });
        int rawBaseline = slotIndex < NUM_POTS
                              ? potentiometerManager.getLastValue(slotIndex)
                              : -1;
        const uint8_t baseline = rawBaseline >= 0
                                     ? Utility::mapToMidiValue(rawBaseline)
                                     : static_cast<uint8_t>(slot.data1 & 0x7F);
        if (!frame.efActive && !hasLfo && !hasFixedLfo) {
            // Forget the previous composed value once ownership returns to the
            // direct pot path. Re-adding a route must force a fresh emit even
            // when it resolves to the same value as the old route.
            frame.lastEmittedValue = 0xFF;
            frame.result = {};
            frame.result.baseline = baseline;
            frame.result.finalValue = baseline;
            frame.resultValid = true;
            continue;
        }

        if (!slot.active) {
            frame.lastEmittedValue = 0xFF;
            frame.result = {};
            frame.result.baseline = baseline;
            frame.result.finalValue = baseline;
            frame.resultValid = true;
            continue;
        }
        SlotModulationInput input{};
        input.baseline = baseline;
        input.efActive = frame.efActive;
        input.efValue = frame.efValue;
        input.efMode = slot.efSettings.destinationMode <=
                               static_cast<uint8_t>(EfDestinationMode::Centered)
                           ? static_cast<EfDestinationMode>(slot.efSettings.destinationMode)
                           : EfDestinationMode::AddClamp;
        for (uint8_t lfoIndex = 0; lfoIndex < input.lfoActive.size(); ++lfoIndex) {
            const SlotLfoLane lane = sanitizeSlotLfoLane(slot.lfo.lfo[lfoIndex]);
            if (lane.enabled()) {
                input.lfoActive[lfoIndex] = true;
                input.lfoNormalized[lfoIndex] = lfoManager.normalizedValue(lfoIndex);
                input.lfoSigned[lfoIndex] = lfoManager.signedValue(lfoIndex);
                input.lfoLane[lfoIndex] = lane;
            } else if (frame.lfoActive[lfoIndex]) {
                // Persisted SlotValue routes historically emitted a complete
                // mapped MIDI value. Replace preserves that audible curve and
                // keeps it independent of the physical pot baseline.
                input.lfoActive[lfoIndex] = true;
                input.lfoNormalized[lfoIndex] =
                    static_cast<float>(frame.lfoValue[lfoIndex]) / 127.0f;
                input.lfoSigned[lfoIndex] =
                    signedSlotLfoFromMidiValue(frame.lfoValue[lfoIndex]);
                input.lfoLane[lfoIndex].setEnabled(true);
                input.lfoLane[lfoIndex].setMode(ModCombineMode::Replace);
                input.lfoLane[lfoIndex].amount = 100;
            }
        }
        frame.result = resolveSlotModulationWithContributions(input);
        frame.resultValid = true;
        const uint8_t finalValue = frame.result.finalValue;

        if (finalValue == frame.lastEmittedValue ||
            currentMs - frame.lastEmitMs < kSlotModulationMinSendIntervalMs) {
            continue;
        }
        const uint8_t cost = slotModulationTransportCost(slot, finalValue);
        if (cost == 0) {
            frame.lastEmittedValue = finalValue;
            frame.lastEmitMs = currentMs;
            continue;
        }
        candidates[slotIndex] = {
            true,
            slot.type == MIDIMessageType::Note,
            finalValue,
            cost,
        };
    }

    while (modulationTransport.availableBytes() > 0) {
        int admittedIndex = modulationTransport.nextCandidate(candidates, true);
        if (admittedIndex < 0) admittedIndex = modulationTransport.nextCandidate(candidates, false);
        if (admittedIndex < 0) break;

        SlotTransportPolicy::Candidate &candidate =
            candidates[static_cast<size_t>(admittedIndex)];
        // Stop rather than skipping an expensive head candidate. Tokens then accumulate and the
        // rotating cursor prevents NRPN/RPN or SysEx destinations from starving behind cheap CCs.
        if (!modulationTransport.canAdmit(candidate.cost)) break;

        candidate.pending = false;
        modulationTransport.recordAttempt(static_cast<size_t>(admittedIndex));
        SlotModulationFrame &frame =
            slotModulationFrames[static_cast<size_t>(admittedIndex)];
        if (emitSlotModulationValue(static_cast<uint8_t>(admittedIndex), candidate.value)) {
            modulationTransport.recordSuccess(candidate.cost);
            frame.lastEmittedValue = candidate.value;
            frame.lastEmitMs = currentMs;
        }
    }
}

bool getSlotModulationResult(uint8_t slotIndex, SlotModulationResult &result) {
    if (slotIndex >= slotModulationFrames.size() ||
        !slotModulationFrames[slotIndex].resultValid) {
        return false;
    }
    result = slotModulationFrames[slotIndex].result;
    return true;
}

// Internal transport clock lane when the device is not following external MIDI clock.
void processInternalClock() {
    if (g_tappedBPM <= 0.0f || externalClockDominant())
        return;

    const unsigned long tickInterval =
        std::max<unsigned long>(1, static_cast<unsigned long>(lroundf(60000.0f /
                                                                         (g_tappedBPM * 24.0f))));
    const unsigned long current = ::now();
    if (internalClockNextTick == 0) {
        internalClockNextTick = current;
    }

    constexpr uint8_t kMaxInternalClockCatchup = 4;
    uint8_t emitted = 0;
    while (static_cast<long>(current - internalClockNextTick) >= 0 &&
           emitted < kMaxInternalClockCatchup) {
        lastClockTime = internalClockNextTick;
        midiHandler.generateClockTick();
        internalClockNextTick += tickInterval;
        ++emitted;
    }
    // Preserve phase for ordinary jitter, but bound worst-case recovery work.
    // Once the cap is exceeded, restart from now instead of replaying an
    // unbounded historical clock burst.
    if (static_cast<long>(current - internalClockNextTick) >= 0) {
        internalClockNextTick = current + tickInterval;
    }
}

// Runtime diagnostics, overrun reporting, and status LED maintenance.
void monitorSystemLoad() {
    static unsigned long lastMonitorTime = 0;
    static unsigned long taskCounter = 0;
    static unsigned long maxLoopDuration = 0;
    static unsigned long lastLoopStart = micros();
    static unsigned long lastLoopOverrunLogMs = 0;
    static unsigned long suppressedLoopOverruns = 0;

    unsigned long currentMicros = micros();
    unsigned long loopDuration = currentMicros - lastLoopStart;
    lastLoopStart = currentMicros;

    g_systemDiagnostics.lastLoopMicros = loopDuration;
    if (loopDuration > maxLoopDuration) {
        maxLoopDuration = loopDuration;
    }
    // Scan budget reconciliation: pot scanning alone takes ~1700µs (42 pots × 4 samples × 10µs).
    // Threshold raised to 2500µs to accommodate full scan + mux settle + MIDI work.
    if (loopDuration > 2500UL) {
        ++g_systemDiagnostics.loopOverrunCount;
        DiagnosticRecord::recordLoopOverrunHighWater(loopDuration);
        const unsigned long currentMillis = now();
        if ((currentMillis - lastLoopOverrunLogMs) >= 1000UL) {
            LOG_PRINTF("{\"diagnostic\":\"loop_overrun\",\"duration_us\":%lu,\"count\":%lu,"
                       "\"suppressed\":%lu}\n",
                       static_cast<unsigned long>(loopDuration),
                       static_cast<unsigned long>(g_systemDiagnostics.loopOverrunCount),
                       static_cast<unsigned long>(suppressedLoopOverruns));
            lastLoopOverrunLogMs = currentMillis;
            suppressedLoopOverruns = 0;
        } else {
            ++suppressedLoopOverruns;
        }
        requestStatusLEDPulse();
    }

    taskCounter++;
    unsigned long currentMillis = now();
    if (currentMillis - lastMonitorTime >= 1000UL) {
        // Diagnostic metrics must be JSON for protocol discipline.
        LOG_PRINTF("{\"type\":\"diag\",\"metric\":\"tasks_per_second\",\"value\":%lu}\n",
                   taskCounter);
        g_systemDiagnostics.maxLoopMicros = maxLoopDuration;
        maxLoopDuration = 0;
        taskCounter = 0;
        lastMonitorTime = currentMillis;
    }

    checkDiagnosticsForAlerts();
    serviceStatusLEDPulse();
}

// Hardware serial health probe used by the configurator/runtime serial lane.
void monitorSerialHealth() {
#if defined(__IMXRT1062__)
    if (IMXRT_LPUART6.STAT & LPUART_STAT_OR) {
        IMXRT_LPUART6.STAT |= LPUART_STAT_OR;
        ++g_systemDiagnostics.uartOverrunCount;
    }
#endif
}

#if defined(UNIT_TEST)
void testOnly_resetRuntimeState() {
    midiServiceRequestCount = 0;
    internalClockNextTick = 0;
    pendingNoteOffs = {};
    slotModulationFrames = {};
    resetModulationTransport();
    statusLedPulseDeadline = 0;
    lastMidiDropAlertCount = 0;
    lastMidiTaskOverrunAlertCount = 0;
    lastUartOverrunAlertCount = 0;
}

void testOnly_emitClockedSlots(uint32_t quarterEvents) { emitClockedNoteSlots(quarterEvents); }

uint16_t testOnly_modulationTransportBytes() { return modulationTransport.availableBytes(); }

size_t testOnly_pendingNoteOffCount() {
    return static_cast<size_t>(std::count_if(
        pendingNoteOffs.begin(), pendingNoteOffs.end(),
        [](const PendingNoteOff &entry) { return entry.active; }));
}

void testOnly_setSlotLfoFrame(uint8_t slotIndex, uint8_t lfoIndex, uint8_t value) {
    if (slotIndex >= slotModulationFrames.size() ||
        lfoIndex >= slotModulationFrames[slotIndex].lfoActive.size()) {
        return;
    }
    slotModulationFrames[slotIndex].lfoActive[lfoIndex] = true;
    slotModulationFrames[slotIndex].lfoValue[lfoIndex] = value;
}

uint8_t testOnly_slotLastEmittedValue(uint8_t slotIndex) {
    return slotIndex < slotModulationFrames.size()
               ? slotModulationFrames[slotIndex].lastEmittedValue
               : 0xFF;
}
#endif
