bseverns/MOARkNOBS-42/firmware/src/ButtonManager.cpp

// ButtonManager is the interaction coordinator between semantic gestures and
// instrument behavior. ButtonScanner owns mux/debounce mechanics and
// ButtonGestureInterpreter owns timing/grammar; this file owns command dispatch
// and the presentation notifications emitted after an on-device action.

#include "ButtonManager.h"
#include "EnvelopeFollower.h"
#include "Globals.h"
#include "ConfigManager.h"
#include "MIDITypes.h"
#include "Utility.h"
#include "TimeUtils.h"
#include "Arpeggiator.h"
#include "WebSerial.h"
#include "LFO/LFOManager.h"
#include "LFO/LFOShape.h"
#include "LFO/LFOClock.h"
#include <array>
#include <map>
#include <cmath>

// Stable press states are fed into DisplayManager, ConfigManager,
// EnvelopeFollower assignments, and the Arpeggiator. Electrical topology stays
// behind ButtonScanner.

extern std::vector<EnvelopeFollower> envelopeFollowers;
extern ButtonManagerContext buttonContext;
extern ConfigManager configManager;
extern LFOManager lfoManager;

// Verbose logging rides on BUTTON_MANAGER_DEBUG. See ButtonManager.h for macros.

// Mirror the global ARG pair count so our math stays synced without recomputing.
static const int NUM_ARG_PAIRS = ARG_PAIRS_LEN;

static constexpr MIDISlot::EfSettings::FilterType SLOT_FILTERS[] = {
    MIDISlot::EfSettings::FilterType::Linear,      MIDISlot::EfSettings::FilterType::OppositeLinear,
    MIDISlot::EfSettings::FilterType::Exponential, MIDISlot::EfSettings::FilterType::Random,
    MIDISlot::EfSettings::FilterType::Lowpass,     MIDISlot::EfSettings::FilterType::Highpass,
    MIDISlot::EfSettings::FilterType::Bandpass};
static constexpr const char *FILTER_TYPE_NAMES[] = {
    "LINEAR", "OPPOSITE_LINEAR", "EXPONENTIAL", "RANDOM", "LOWPASS", "HIGHPASS", "BANDPASS"};

static constexpr int NUM_FILTER_TYPES = sizeof(SLOT_FILTERS) / sizeof(SLOT_FILTERS[0]);
static constexpr ARGMethod ALL_ARG_METHODS[] = {
    ARGMethod::PLUS, ARGMethod::MIN,  ARGMethod::PECK, ARGMethod::SHAV, ARGMethod::SQAR,
    ARGMethod::BABS, ARGMethod::TABS, ARGMethod::MULT, ARGMethod::DIVI, ARGMethod::AVG,
    ARGMethod::XABS, ARGMethod::MAXX, ARGMethod::MINN, ARGMethod::XORR};

static constexpr const char *ARG_METHOD_NAMES[] = {"PLUS", "MIN",  "PECK", "SHAV", "SQAR",
                                                   "BABS", "TABS", "MULT", "DIVI", "AVG",
                                                   "XABS", "MAXX", "MINN", "XORR"};

// Active profile index is stored globally so boot can restore it.

namespace {
constexpr uint8_t maskCtrl0 = 1 << 0;
constexpr uint8_t maskCtrl1 = 1 << 1;
constexpr uint8_t maskCtrl2 = 1 << 2;
constexpr uint8_t maskCtrl3 = 1 << 3;
constexpr uint8_t maskCtrl4 = 1 << 4;
constexpr uint8_t maskCtrl5 = 1 << 5;
constexpr uint8_t panicMask = maskCtrl0 | maskCtrl1 | maskCtrl2;
constexpr uint8_t configModeMask = maskCtrl0 | maskCtrl2 | maskCtrl3 | maskCtrl5;
constexpr uint8_t clockSourceMask = maskCtrl1 | maskCtrl4 | maskCtrl5;
constexpr uint8_t lfoTuningMask = maskCtrl0 | maskCtrl1 | maskCtrl3;
constexpr uint8_t lfoLiveToggleMask = maskCtrl0 | maskCtrl1 | maskCtrl4;
constexpr unsigned long kTuningStatusMs = 600;

// Emit one slot patch so the browser can follow on-device edits.
inline void streamSlotPatch(ConfigManager &config, uint8_t slotIndex) {
    WebSerial::sendSlotPatch(config, slotIndex);
}

// Emit one slot-to-envelope assignment patch for the browser/editor layer.
inline void streamEnvelopeAssignment(uint8_t slotIndex, int envelopeIndex) {
    WebSerial::sendEnvelopeAssignment(slotIndex, envelopeIndex);
}

// Emit updated filter tuning after a control-button gesture changes it.
inline void streamFilterPatch(const EnvelopeFollower &env) {
    WebSerial::sendFilterPatch(env.getFilterType(), env.getShapingFrequency(), env.getShapingQ());
}

// Emit current ARG settings after local edits so the browser stays honest.
inline void streamArgPatch(const ConfigManager &config) {
    WebSerial::sendArgPatch(config.getARGMethod(), config.getARGEnable() != 0,
                            config.getEnvelopeA(), config.getEnvelopeB());
}

// Accept either raw analog pin ids or normalized follower indices from older call sites.
inline uint8_t normalizeEnvelopeIndex(uint8_t raw) {
    int idx = envelopeIndexFromAnalogPin(raw);
    if (idx >= 0) {
        return static_cast<uint8_t>(idx);
    }
    if (raw < NUM_ENVELOPES) {
        return raw;
    }
    return static_cast<uint8_t>(raw % NUM_ENVELOPES);
}

// Map one EF filter enum back to its position in the cycle list.
inline int filterIndex(MIDISlot::EfSettings::FilterType type) {
    for (int i = 0; i < NUM_FILTER_TYPES; ++i) {
        if (SLOT_FILTERS[i] == type) {
            return i;
        }
    }
    return 0;
}

// Step forward/backward through the supported EF filter list.
inline MIDISlot::EfSettings::FilterType cycleFilter(MIDISlot::EfSettings::FilterType current,
                                                    int delta) {
    int index = filterIndex(current);
    index = (index + delta + NUM_FILTER_TYPES) % NUM_FILTER_TYPES;
    return SLOT_FILTERS[index];
}

const char *slotTypeLabel(MIDIMessageType type) {
    switch (type) {
    case MIDIMessageType::OFF:
        return "OFF";
    case MIDIMessageType::CC:
        return "CC";
    case MIDIMessageType::Note:
        return "NOTE";
    case MIDIMessageType::PitchBend:
        return "BEND";
    case MIDIMessageType::ProgramChange:
        return "PROG";
    case MIDIMessageType::Aftertouch:
        return "AFT";
    case MIDIMessageType::ModWheel:
        return "MOD";
    case MIDIMessageType::NRPN:
        return "NRPN";
    case MIDIMessageType::RPN:
        return "RPN";
    case MIDIMessageType::SysEx:
        return "SYX";
    }
    return "?";
}

const char *lfoShapeLabel(LFOShape shape) {
    switch (shape) {
    case LFOShape::Sine:
        return "SINE";
    case LFOShape::Triangle:
        return "TRI";
    case LFOShape::Saw:
        return "SAW";
    case LFOShape::Square:
        return "SQR";
    case LFOShape::SampleHold:
        return "S/H";
    case LFOShape::RandomSlew:
        return "RSLEW";
    }
    return "?";
}

const char *lfoSyncRatioLabel(LFOSyncRatio ratio) {
    switch (ratio) {
    case LFOSyncRatio::Div1:
        return "1/1";
    case LFOSyncRatio::Div2:
        return "1/2";
    case LFOSyncRatio::Div4:
        return "1/4";
    case LFOSyncRatio::Div8:
        return "1/8";
    case LFOSyncRatio::Div16:
        return "1/16";
    case LFOSyncRatio::Div32:
        return "1/32";
    case LFOSyncRatio::Mul2:
        return "x2";
    case LFOSyncRatio::Mul4:
        return "x4";
    }
    return "?";
}

const char *lfoTargetLabel(LFOInternalTarget target) {
    switch (target) {
    case LFOInternalTarget::EfGainTrim:
        return "EF GAIN";
    case LFOInternalTarget::ArpSwing:
        return "ARP SWNG";
    case LFOInternalTarget::VelocityShift:
        return "VEL SHIFT";
    case LFOInternalTarget::NoteChance:
        return "NOTE CHNC";
    case LFOInternalTarget::ArpGate:
        return "ARP GATE";
    case LFOInternalTarget::JitterDepth:
        return "JIT DEPTH";
    case LFOInternalTarget::JitterSmoothness:
        return "JIT SMTH";
    }
    return "?";
}

LFOInternalTarget cycleLfoTarget(LFOInternalTarget current) {
    uint8_t next = static_cast<uint8_t>(current) + 1;
    if (next > static_cast<uint8_t>(LFOInternalTarget::JitterSmoothness)) {
        next = 0;
    }
    return static_cast<LFOInternalTarget>(next);
}

// Persist new EF settings, update the slot cache, and reconfigure the live follower if present.
inline void commitEfSettings(ButtonManagerContext &context, int slotIndex,
                             const MIDISlot::EfSettings &settings) {
    MIDISlot &slot = context.configManager.getSlot(static_cast<uint8_t>(slotIndex));
    slot.efSettings = settings;
    slot.setEnvelopeFollowerIndex(settings.followerIndex);
    context.configManager.saveSlot(static_cast<uint8_t>(slotIndex), slot);
    context.potToEnvelopeMap[slotIndex] = slot.efSettings;
    int follower = settings.followerIndex;
    if (follower >= 0 && follower < static_cast<int>(context.envelopes.size())) {
        context.envelopes[follower].configureFromEfSettings(slot.efSettings);
    }
}
} // namespace

// Constructor
ButtonManager::ButtonManager(const HardwareConfig &config, const uint8_t *controlPins,
                             PotentiometerManager *potentiometerManager)
    : _scanner(config, controlPins), _potentiometerManager(potentiometerManager), activeMode(0),
      _pendingEfSlot(-1), _efAssignDeadline(0) {}

// Called during setup to configure the multiplexers and reset gesture state.
void ButtonManager::initButtons() {
    _scanner.initHardware();
    _gesture.reset();
}

void ButtonManager::enterOnDeviceConfigMode(ButtonManagerContext &context) {
    cancelPendingConfirm(context);
    _pendingEfSlot = -1;
    _onDeviceConfigModeActive = true;
    _onDeviceConfigModeDirty = false;
    _lastConfigFloorPotBucket = -1;
    if (context.diagnosticMode) {
        context.diagnosticMode = false;
        context.ledManager.setDiagnosticMode(false);
    }
    context.ledManager.setPanelModeIndicator(PanelModeIndicator::Config);
    context.displayManager.displayStatus("Config Mode ON", 1200);
}

void ButtonManager::exitOnDeviceConfigMode(ButtonManagerContext &context, bool autosave) {
    cancelPendingConfirm(context);
    bool saved = false;
    if (autosave && _onDeviceConfigModeDirty) {
        context.configManager.saveProfile(g_activeProfile);
        context.configManager.saveEnvelopeSettings(context.potToEnvelopeMap, context.envelopes);
        context.profileRequests.requestSave();
        saved = true;
    }
    _onDeviceConfigModeActive = false;
    _onDeviceConfigModeDirty = false;
    _lastConfigFloorPotBucket = -1;
    context.ledManager.setPanelModeIndicator(PanelModeIndicator::None);
    context.displayManager.displayStatus(saved ? "Config Saved" : "Config Mode OFF", 1200);
}

void ButtonManager::enterLfoTuningMode(ButtonManagerContext &context) {
    cancelPendingConfirm(context);
    _pendingEfSlot = -1;
    _lfoTuningActive = true;
    _lfoTuningIndex = 0;
    _lastLfoTuneFreqHz = -1.0f;
    _lastLfoTuneDepth = -1.0f;
    _lastLfoTuneRatioIndex = -1;
    _lastLfoTuneBipolarState = -1;
    context.ledManager.setPanelModeIndicator(PanelModeIndicator::Lfo);
    context.displayManager.displayStatus("LFO Tune ON", 1000);
}

void ButtonManager::exitLfoTuningMode(ButtonManagerContext &context) {
    cancelPendingConfirm(context);
    _lfoTuningActive = false;
    _lastLfoTuneRatioIndex = -1;
    _lastLfoTuneBipolarState = -1;
    context.ledManager.setPanelModeIndicator(PanelModeIndicator::None);
    context.displayManager.displayStatus("LFO Tune OFF", 1000);
}

// One unified loop scans stable states, interprets gestures, and dispatches
// resulting actions. The electrical and gesture boundaries remain separate.
void ButtonManager::processButtons(ButtonManagerContext &context) {
    unsigned long now = ::now();

    // Drop pending EF assignment if the window expired
    if (_pendingEfSlot >= 0 && now > _efAssignDeadline) {
        _pendingEfSlot = -1;
        context.displayManager.displayStatus("EF assign timeout", 1000);
    }

#ifdef BUTTON_MANAGER_PROFILE
    uint32_t tStart = micros();
#endif

    // Scan one matrix row per pass. This keeps button latency under control while shaving the
    // worst-case loop time enough that other schedulers can still run on schedule.
    const MatrixScanRange scanned = _scanner.scanNextMatrixRow(now);
    for (uint8_t i = scanned.begin; i < scanned.end; ++i) {
        updateButtonStateMachine(i, _scanner.isPressed(i), context);
    }

    // Control buttons & pots via spare mux channels
    scanControlInputs(context);
    flushDeferredControlPresses(context);

#ifdef BUTTON_MANAGER_PROFILE
    uint32_t tElapsed = micros() - tStart;
    static uint32_t maxScan = 0;
    static uint64_t totalScan = 0;
    static uint32_t scanCount = 0;
    if (tElapsed > maxScan) {
        maxScan = tElapsed;
    }
    totalScan += tElapsed;
    if (++scanCount % 1000 == 0) {
        Serial.printf("btn scan avg %luus max %luus\n", (unsigned long)(totalScan / scanCount),
                      (unsigned long)maxScan);
    }
    // Scan budget reconciliation: flag if we exceed the scheduler slice budget.
    // Button scan should complete in <2ms to leave room for MIDI/LED work.
    if (tElapsed > 2000U) {
        ++g_systemDiagnostics.loopOverrunCount;
    }
#endif
}

void ButtonManager::updateButtonStateMachine(uint8_t index, bool pressed,
                                             ButtonManagerContext &context) {
    ButtonGestureMode mode;
    mode.immediateShortPresses = _onDeviceConfigModeActive || _lfoTuningActive;
    mode.longPressesEnabled = !mode.immediateShortPresses;
    dispatchGestureEvents(_gesture.updateButton(index, pressed, ::now(), mode), context);
}

/*
Fire the actual long‑press payload after confirmation.
*/
void ButtonManager::performLongPressAction(uint8_t index, ButtonManagerContext &context) {
    // Slot buttons (0-41)
    if (index < NUM_VIRTUAL_BUTTONS) {
        MIDISlot &slotRef = context.configManager.getSlot(index);
        MIDISlot::EfSettings settings = slotRef.efSettings;
        settings.followerIndex = slotRef.getEnvelopeFollowerIndex();
        auto it = context.potToEnvelopeMap.find(index);
        if (it != context.potToEnvelopeMap.end()) {
            settings = it->second;
        }
        if (settings.followerIndex < 0) {
            settings.followerIndex = 0;
        } else {
            settings.followerIndex =
                static_cast<int8_t>((settings.followerIndex + 1) % context.envelopes.size());
        }
        commitEfSettings(context, index, settings);
        int assigned = settings.followerIndex;
        if (assigned >= 0 && assigned < static_cast<int>(context.envelopes.size())) {
            context.envelopes[assigned].toggleActive(true);
        }
        char buf[32];
        snprintf(buf, sizeof(buf), "Slot %d -> EF %d", index, assigned);
        context.displayManager.displayStatus(buf, 1500);

        // Allow an explicit EF pick via control buttons 0-5
        _pendingEfSlot = index;
        _efAssignDeadline = ::now() + EF_ASSIGN_WINDOW_MS;
    } else {
        // Control buttons (0-5)
        uint8_t ctrlIdx = index - NUM_VIRTUAL_BUTTONS;
        switch (ctrlIdx) {
        case 0: { // Calibrate assigned envelope follower
            auto it = context.potToEnvelopeMap.find(context.activePot);
            if (it == context.potToEnvelopeMap.end()) {
                context.displayManager.displayStatus("No EF assigned", 1000);
                break;
            }
            int efIndex = it->second.followerIndex;
            if (efIndex >= 0 && efIndex < static_cast<int>(context.envelopes.size())) {
                context.envelopes[efIndex].calibrate(); // auto-saves baseline via ConfigManager
            }
            context.displayManager.displayStatus("EF Calibrated", 1500);
            break;
        }
        case 1: {
            if (context.diagnosticMode) {
                context.diagnosticPage = static_cast<uint8_t>((context.diagnosticPage + 1) %
                                                              DisplayManager::kDiagnosticPageCount);
                context.displayManager.displayStatus("Diag Page", 1000);
            } else {
                // Reload configuration profile from EEPROM
                context.configManager.loadProfile(g_activeProfile);
                context.potChannels.clear();
                for (uint8_t i = 0; i < context.configManager.getNumPots(); ++i) {
                    context.potChannels.push_back(context.configManager.getPotChannel(i));
                }
                context.profileRequests.requestReload();
                context.displayManager.displayStatus("Profile Reset!", 1500);
            }
            break;
        }
        case 2: { // Toggle Slot Active
            MIDISlot &slot = context.configManager.getSlot(context.activePot);
            slot.active = !slot.active;
            context.configManager.saveSlot(context.activePot, slot);
            char buf[32];
            snprintf(buf, sizeof(buf), "Slot %d %s", context.activePot, slot.active ? "ON" : "OFF");
            context.displayManager.displayStatus(buf, 1500);
            break;
        }
        case 3: // EEPROM reload from current profile
            context.configManager.loadConfiguration(context.potChannels);
            context.displayManager.displayStatus("Config Reloaded", 1500);
            break;
        case 4: { // Save configuration to the active profile
            context.configManager.saveProfile(g_activeProfile);
            context.configManager.saveEnvelopeSettings(context.potToEnvelopeMap, context.envelopes);
            context.profileRequests.requestSave();
            context.displayManager.displayStatus("Config Saved", 1500);
            break;
        }
        case 5: { // Diagnostic entry + page cycling (encoder long-press)
            if (!context.diagnosticMode) {
                context.diagnosticMode = true;
                context.diagnosticPage = DisplayManager::kDiagnosticPageDebug;
                context.displayManager.displayStatus("Diagnostics", 1000);
                context.ledManager.setDiagnosticMode(true);
            } else {
                context.diagnosticPage = static_cast<uint8_t>((context.diagnosticPage + 1) %
                                                              DisplayManager::kDiagnosticPageCount);
                context.displayManager.displayStatus("Diag Page", 1000);
            }
            break;
        }
        default:
            context.displayManager.displayStatus("No Long Action", 1000);
            break;
        }
    }
}

void ButtonManager::flushDeferredControlPresses(ButtonManagerContext &context) {
    dispatchGestureEvents(_gesture.flushDeferred(::now()), context);
}

void ButtonManager::dispatchGestureEvents(const ButtonGestureEvents &events,
                                          ButtonManagerContext &context) {
    for (uint8_t eventIndex = 0; eventIndex < events.count; ++eventIndex) {
        const ButtonGestureEvent &event = events.items[eventIndex];
        switch (event.type) {
        case ButtonGestureEventType::PhysicalPress:
            if (event.value >= NUM_VIRTUAL_BUTTONS) {
                context.ledManager.triggerControlButton();
            }
            break;
        case ButtonGestureEventType::PhysicalRelease:
            context.displayManager.registerInteraction();
            break;
        case ButtonGestureEventType::SinglePress:
            doSinglePressAction(event.value, context);
            break;
        case ButtonGestureEventType::DoublePress:
            handleDoublePress(event.value, context);
            break;
        case ButtonGestureEventType::LongPressArmed:
            context.displayManager.displayStatus("CONFIRM\nTap again", 1000);
            startWarningForIndex(event.value, context);
            break;
        case ButtonGestureEventType::LongPressConfirmed:
            performLongPressAction(event.value, context);
            break;
        case ButtonGestureEventType::ConfirmationCancelled:
            if (context.ledManager.isWarningActive()) {
                context.ledManager.clearWarningAnimation();
            }
            break;
        case ButtonGestureEventType::ComboPress:
            handleMultiButtonPress(event.value, context);
            break;
        case ButtonGestureEventType::ComboLongPress:
            handleLongControlChord(event.value, context);
            break;
        case ButtonGestureEventType::ComboRelease:
            handleControlChordRelease(event.value, context);
            break;
        }
    }
}

void ButtonManager::handleLongControlChord(uint8_t mask, ButtonManagerContext &context) {
    const uint8_t arpEditMask = maskCtrl2 | maskCtrl4;
    const uint8_t swingMask = maskCtrl2 | maskCtrl3;
    if (mask == arpEditMask) {
        if (arpeggiator.isActive(context.activePot)) {
            g_arpEditActive = true;
            context.displayManager.displayStatus("Arp Edit", 1000);
        } else {
            context.displayManager.displayStatus("Arp Off", 1000);
        }
        return;
    }
    if (mask == swingMask) {
        static uint8_t swingPreset = 0;
        static const uint8_t swingPresets[] = {0, 8, 16, 30};
        swingPreset = static_cast<uint8_t>((swingPreset + 1) %
                                           (sizeof(swingPresets) / sizeof(swingPresets[0])));
        const uint8_t value = swingPresets[swingPreset];
        arpeggiator.setSwingPercent(static_cast<float>(value));
        char buf[24];
        snprintf(buf, sizeof(buf), "Swing: %u%%", value);
        context.displayManager.displayStatus(buf, 1000);
    }
}

void ButtonManager::handleControlChordRelease(uint8_t mask, ButtonManagerContext &context) {
    if (mask == (maskCtrl2 | maskCtrl4) && g_arpEditActive) {
        g_arpEditActive = false;
        context.displayManager.displayStatus("Arp Edit Off", 1000);
    }
}

/*
Double press logic
*/
void ButtonManager::handleDoublePress(uint8_t index, ButtonManagerContext &context) {
    auto cycleFilterForSlot = [&](uint8_t slotIndex, int delta) -> bool {
        auto it = context.potToEnvelopeMap.find(slotIndex);
        if (it == context.potToEnvelopeMap.end()) {
            context.displayManager.displayStatus("No EF assigned", 1000);
            return false;
        }

        MIDISlot::EfSettings settings = it->second;
        if (settings.followerIndex < 0 ||
            settings.followerIndex >= static_cast<int>(context.envelopes.size())) {
            context.displayManager.displayStatus("No EF assigned", 1000);
            return false;
        }

        settings.filterType = cycleFilter(settings.filterType, delta);
        commitEfSettings(context, slotIndex, settings);

        SlotEnvelopePayload payload = context.configManager.getSlotEnvelopePayload(slotIndex);
        payload.filterType =
            static_cast<uint8_t>(EnvelopeFollower::filterFromEfType(settings.filterType));
        context.configManager.setSlotEnvelopePayload(slotIndex, payload);

        streamSlotPatch(context.configManager, slotIndex);
        streamFilterPatch(context.envelopes[settings.followerIndex]);

        const char *filterName = FILTER_TYPE_NAMES[filterIndex(settings.filterType)];
        char msg[32];
        snprintf(msg, sizeof(msg), "Slot %d => %s", slotIndex, filterName);
        context.displayManager.displayStatus(msg, 1500);
        return true;
    };

    if (index < NUM_VIRTUAL_BUTTONS) {
        cycleFilterForSlot(index, +1);
        return;
    }

    uint8_t cIndex = static_cast<uint8_t>(index - NUM_VIRTUAL_BUTTONS);
    switch (cIndex) {
    case 0:
        cycleFilterForSlot(context.activePot, +1);
        break;
    case 1:
        cycleFilterForSlot(context.activePot, -1);
        break;
    case 2: {
        // Double Press (Ctrl #2): Cycle MIDI message type
        MIDISlot &slot = context.configManager.getSlot(context.activePot);
        slot.type = static_cast<MIDIMessageType>((static_cast<int>(slot.type) + 1) %
                                                 (static_cast<int>(MIDIMessageType::SysEx) + 1));
        context.configManager.saveSlot(context.activePot, slot);
        char buf[32];
        snprintf(buf, sizeof(buf), "Slot %d Type %d", context.activePot,
                 static_cast<int>(slot.type));
        context.displayManager.displayStatus(buf, 1500);
        streamSlotPatch(context.configManager, context.activePot);
        break;
    }
    case 3: {
        // Double Press (Ctrl #3): step through useful ADC oversampling presets.
        MIDISlot &slot = context.configManager.getSlot(context.activePot);
        MIDISlot::EfSettings settings = slot.efSettings;
        auto it = context.potToEnvelopeMap.find(context.activePot);
        if (it != context.potToEnvelopeMap.end()) {
            settings = it->second;
        }

        if (settings.oversample < 2) {
            settings.oversample = 2;
        } else if (settings.oversample < 4) {
            settings.oversample = 4;
        } else if (settings.oversample < 8) {
            settings.oversample = 8;
        } else if (settings.oversample < 16) {
            settings.oversample = 16;
        } else if (settings.oversample < 32) {
            settings.oversample = 32;
        } else {
            settings.oversample = 1;
        }

        commitEfSettings(context, context.activePot, settings);
        char buf[32];
        snprintf(buf, sizeof(buf), "Slot %d EF OS %ux", context.activePot,
                 static_cast<unsigned>(settings.oversample));
        context.displayManager.displayStatus(buf, 1500);
        streamSlotPatch(context.configManager, context.activePot);
        break;
    }
    case 4: {
        // Double Press (Ctrl #4): toggle the slot-local ARG combiner live.
        MIDISlot &slot = context.configManager.getSlot(context.activePot);
        slot.arg.enabled = slot.arg.enabled ? 0 : 1;
        context.configManager.saveSlot(context.activePot, slot);
        context.configManager.setARGEnable(slot.arg.enabled);
        context.configManager.setARGMethod(static_cast<uint8_t>(slot.arg.method));
        context.configManager.setEnvelopePair(slot.arg.sourceA, slot.arg.sourceB);

        context.displayManager.displayStatus(slot.arg.enabled ? "ARG ON" : "ARG OFF", 1200);
        streamSlotPatch(context.configManager, context.activePot);
        streamArgPatch(context.configManager);
        break;
    }
    default:
        context.displayManager.displayStatus("Unknown double press", 1000);
        break;
    }
}

/*
Dispatch a confirmed short press. The helper `handleSingleButtonPress` keeps
the actual per-button actions so other parts of the firmware can reuse them.
*/
void ButtonManager::doSinglePressAction(uint8_t index, ButtonManagerContext &context) {
    BM_DBG_PRINTLN("Single Press on button " + String(index));
    handleSingleButtonPress(index, context);
}

void ButtonManager::handleSingleButtonPress(uint8_t buttonIndex, ButtonManagerContext &context) {
    if (_onDeviceConfigModeActive) {
        if (buttonIndex < NUM_VIRTUAL_BUTTONS) {
            context.activePot = buttonIndex;
            char buf[24];
            snprintf(buf, sizeof(buf), "Cfg Slot=%u", context.activePot);
            context.displayManager.displayStatus(buf, 800);
            return;
        }

        const uint8_t controlIndex = buttonIndex - NUM_VIRTUAL_BUTTONS;
        switch (controlIndex) {
        case 0: {
            context.activePot = (context.activePot + NUM_POTS - 1) % NUM_POTS;
            char buf[24];
            snprintf(buf, sizeof(buf), "Cfg Slot=%u", context.activePot);
            context.displayManager.displayStatus(buf, 800);
            break;
        }
        case 1: {
            context.activePot = (context.activePot + 1) % NUM_POTS;
            char buf[24];
            snprintf(buf, sizeof(buf), "Cfg Slot=%u", context.activePot);
            context.displayManager.displayStatus(buf, 800);
            break;
        }
        case 2: {
            MIDISlot &slot = context.configManager.getSlot(context.activePot);
            slot.type = static_cast<MIDIMessageType>(
                (static_cast<int>(slot.type) + 1) % (static_cast<int>(MIDIMessageType::SysEx) + 1));
            context.configManager.saveSlot(context.activePot, slot);
            markOnDeviceConfigDirty();
            char buf[32];
            snprintf(buf, sizeof(buf), "Type=%s", slotTypeLabel(slot.type));
            context.displayManager.displayStatus(buf, 900);
            streamSlotPatch(context.configManager, context.activePot);
            break;
        }
        case 3: {
            uint8_t oldChan = context.configManager.getPotChannel(context.activePot);
            uint8_t newChan = (oldChan % 16) + 1;
            context.configManager.setPotChannel(context.activePot, newChan);
            if (_potentiometerManager != nullptr) {
                _potentiometerManager->setChannel(context.activePot, newChan);
            }
            if (context.activePot < context.potChannels.size()) {
                context.potChannels[context.activePot] = newChan;
            }
            markOnDeviceConfigDirty();
            char buf[24];
            snprintf(buf, sizeof(buf), "Ch=%u", newChan);
            context.displayManager.displayStatus(buf, 900);
            streamSlotPatch(context.configManager, context.activePot);
            break;
        }
        case 4: {
            MIDIMessageType type = context.configManager.getSlotType(context.activePot);
            if (type == MIDIMessageType::CC) {
                uint8_t oldCC = context.configManager.getPotCCNumber(context.activePot);
                uint8_t newCC = (oldCC + 1) % 128;
                context.configManager.setPotCCNumber(context.activePot, newCC);
                if (_potentiometerManager != nullptr) {
                    _potentiometerManager->setCCNumber(context.activePot, newCC);
                }
                char buf[24];
                snprintf(buf, sizeof(buf), "CC=%u", newCC);
                context.displayManager.displayStatus(buf, 900);
            } else {
                uint8_t param = context.configManager.getSlotData1(context.activePot);
                param = (param + 1) % 128;
                context.configManager.setSlotData1(context.activePot, param);
                const char *label = "D1";
                if (type == MIDIMessageType::Note) {
                    label = "NOTE";
                } else if (type == MIDIMessageType::NRPN) {
                    label = "NRPN";
                } else if (type == MIDIMessageType::RPN) {
                    label = "RPN";
                } else if (type == MIDIMessageType::ProgramChange) {
                    label = "PROG";
                }
                char buf[32];
                snprintf(buf, sizeof(buf), "%s=%u", label, param);
                context.displayManager.displayStatus(buf, 900);
            }
            markOnDeviceConfigDirty();
            streamSlotPatch(context.configManager, context.activePot);
            break;
        }
        case 5:
            exitOnDeviceConfigMode(context, true);
            break;
        default:
            break;
        }
        return;
    }

    if (_lfoTuningActive) {
        if (buttonIndex < NUM_VIRTUAL_BUTTONS) {
            return;
        }
        const uint8_t controlIndex = buttonIndex - NUM_VIRTUAL_BUTTONS;
        LFO &lfo = lfoManager.lfo(_lfoTuningIndex % LFOManager::kMaxLFOs);
        switch (controlIndex) {
        case 0:
            _lfoTuningIndex = 0;
            _lastLfoTuneRatioIndex = -1;
            _lastLfoTuneBipolarState = -1;
            context.displayManager.displayStatus("LFO1", 800);
            break;
        case 1:
            _lfoTuningIndex = 1;
            _lastLfoTuneRatioIndex = -1;
            _lastLfoTuneBipolarState = -1;
            context.displayManager.displayStatus("LFO2", 800);
            break;
        case 2: {
            uint8_t next = static_cast<uint8_t>((static_cast<uint8_t>(lfo.getShape()) + 1) % 6);
            lfo.setShape(static_cast<LFOShape>(next));
            char buf[24];
            snprintf(buf, sizeof(buf), "Shape %s", lfoShapeLabel(lfo.getShape()));
            context.displayManager.displayStatus(buf, 900);
            break;
        }
        case 3:
            lfo.setSyncEnabled(!lfo.isSyncEnabled());
            _lastLfoTuneRatioIndex = -1;
            _lastLfoTuneBipolarState = -1;
            context.displayManager.displayStatus(lfo.isSyncEnabled() ? "Sync ON" : "Sync OFF", 900);
            break;
        case 4: {
            std::array<LFOManager::Route, PROFILE_MAX_ROUTES> routes{};
            const size_t count = std::min(lfoManager.routeCount(), routes.size());
            size_t internalIndex = routes.size();
            for (size_t i = 0; i < count; ++i) {
                if (!lfoManager.getRoute(i, routes[i])) {
                    continue;
                }
                if (routes[i].type == LFOManager::Route::Type::Internal &&
                    routes[i].lfoIndex == (_lfoTuningIndex % LFOManager::kMaxLFOs)) {
                    internalIndex = i;
                    break;
                }
            }

            if (internalIndex == routes.size()) {
                lfoManager.addInternalRoute(_lfoTuningIndex % LFOManager::kMaxLFOs,
                                            LFOInternalTarget::EfGainTrim, 1.0f);
                context.displayManager.displayStatus("Target EF GAIN", 900);
            } else {
                routes[internalIndex].target = cycleLfoTarget(routes[internalIndex].target);
                lfoManager.setRoutes(routes.data(), count);
                char buf[24];
                snprintf(buf, sizeof(buf), "Target %s",
                         lfoTargetLabel(routes[internalIndex].target));
                context.displayManager.displayStatus(buf, 900);
            }
            break;
        }
        case 5:
            exitLfoTuningMode(context);
            break;
        default:
            break;
        }
        return;
    }

    // Pending EF selection overrides normal control button behavior
    if (_pendingEfSlot >= 0 && buttonIndex >= NUM_VIRTUAL_BUTTONS) {
        uint8_t controlIndex = buttonIndex - NUM_VIRTUAL_BUTTONS;
        if (controlIndex < context.envelopes.size()) {
            MIDISlot &slotRef = context.configManager.getSlot(_pendingEfSlot);
            MIDISlot::EfSettings settings = slotRef.efSettings;
            settings.followerIndex = slotRef.getEnvelopeFollowerIndex();
            settings.followerIndex = static_cast<int8_t>(controlIndex);
            commitEfSettings(context, _pendingEfSlot, settings);
            context.envelopes[controlIndex].toggleActive(true);
            char buf[32];
            snprintf(buf, sizeof(buf), "Slot %d -> EF %d", _pendingEfSlot, controlIndex);
            context.displayManager.displayStatus(buf, 1500);
            streamEnvelopeAssignment(_pendingEfSlot, controlIndex);
        }
        _pendingEfSlot = -1;
        return;
    }

    // If it's a virtual "slot" button (0..41)
    if (buttonIndex < NUM_VIRTUAL_BUTTONS) {
        // Make that pot (slot) the “active slot.”
        context.activePot = buttonIndex;
        context.displayManager.displayStatus(("Active Slot=" + String(buttonIndex)).c_str(), 1000);
        return;
    }

    // Otherwise, it's a control button
    uint8_t controlIndex = buttonIndex - NUM_VIRTUAL_BUTTONS;
    switch (controlIndex) {
    case 0:
        // Short Press (Control Button #0): Toggle EF On/Off
        context.envelopeFollowMode = !context.envelopeFollowMode;
        context.displayManager.displayStatus(context.envelopeFollowMode ? "EF: ON" : "EF: OFF",
                                             1500);
        break;

    case 1: {
        // Short Press (Control Button #1): Select next slot
        context.activePot = (context.activePot + 1) % NUM_POTS;
        context.displayManager.displayStatus(("Next Slot=" + String(context.activePot)).c_str(),
                                             1500);
    } break;

    case 2: {
        // Short Press (Control Button #2): Cycle Envelope to follow [if EF on]
        if (!context.envelopeFollowMode) {
            context.displayManager.displayStatus("EF is OFF", 1000);
            break;
        }

        // If EF is on, cycle to the next EF for the active slot
        MIDISlot &slotRef = context.configManager.getSlot(context.activePot);
        MIDISlot::EfSettings settings = slotRef.efSettings;
        settings.followerIndex = slotRef.getEnvelopeFollowerIndex();
        auto it = context.potToEnvelopeMap.find(context.activePot);
        if (it != context.potToEnvelopeMap.end()) {
            settings = it->second;
        }
        if (settings.followerIndex < 0) {
            settings.followerIndex = 0;
        } else {
            settings.followerIndex =
                static_cast<int8_t>((settings.followerIndex + 1) % context.envelopes.size());
        }
        commitEfSettings(context, context.activePot, settings);
        int assigned = settings.followerIndex;
        if (assigned >= 0 && assigned < static_cast<int>(context.envelopes.size())) {
            context.envelopes[assigned].toggleActive(true);
        }

        char buf[32];
        snprintf(buf, sizeof(buf), "Slot %d -> EF %d", context.activePot, assigned);
        context.displayManager.displayStatus(buf, 1500);
        streamEnvelopeAssignment(context.activePot, assigned);
    } break;

    case 3: {
        // Short Press (Control Button #3): Cycle the active slot’s MIDI channel 1..16
        uint8_t oldChan = context.configManager.getPotChannel(context.activePot);
        uint8_t newChan = (oldChan % 16) + 1; // cycles 1..16
        context.configManager.setPotChannel(context.activePot, newChan);

        if (_potentiometerManager != nullptr) {
            _potentiometerManager->setChannel(context.activePot, newChan);
        }
        if (context.activePot < context.potChannels.size()) {
            context.potChannels[context.activePot] = newChan;
        }

        char buf[32];
        snprintf(buf, sizeof(buf), "Slot %d => Ch %d", context.activePot, newChan);
        context.displayManager.displayStatus(buf, 1500);
        streamSlotPatch(context.configManager, context.activePot);
    } break;

    case 4: {
        // Short Press (Control Button #4): Cycle the active slot’s registry number
        MIDIMessageType type = context.configManager.getSlotType(context.activePot);
        if (type == MIDIMessageType::CC) {
            uint8_t oldCC = context.configManager.getPotCCNumber(context.activePot);
            uint8_t newCC = (oldCC + 1) % 128; // 0..127
            context.configManager.setPotCCNumber(context.activePot, newCC);
            if (_potentiometerManager != nullptr) {
                _potentiometerManager->setCCNumber(context.activePot, newCC);
            }
            char buf[32];
            snprintf(buf, sizeof(buf), "Slot %d => CC %d", context.activePot, newCC);
            context.displayManager.displayStatus(buf, 1500);
            streamSlotPatch(context.configManager, context.activePot);
        } else {
            uint8_t param = context.configManager.getSlotData1(context.activePot);
            param = (param + 1) % 128;
            context.configManager.setSlotData1(context.activePot, param);
            const char *label = "D1";
            if (type == MIDIMessageType::Note) {
                label = "NOTE";
            } else if (type == MIDIMessageType::NRPN) {
                label = "NRPN";
            } else if (type == MIDIMessageType::RPN) {
                label = "RPN";
            } else if (type == MIDIMessageType::ProgramChange) {
                label = "PROG";
            }
            char buf[32];
            snprintf(buf, sizeof(buf), "Slot %d => %s %d", context.activePot, label, param);
            context.displayManager.displayStatus(buf, 1500);
            streamSlotPatch(context.configManager, context.activePot);
        }
        WebSerial::sendSlotPatch(context.configManager, context.activePot);
    } break;

    case 5: {
        // Short Press (Control Button #5): Tapped BPM
        if (context.diagnosticMode) {
            // Diagnostics is modal; a quick tap exits so the panel returns to tempo duty.
            context.diagnosticMode = false;
            context.displayManager.displayStatus("Diag Off", 1000);
            context.ledManager.setDiagnosticMode(false);
            break;
        }
        static unsigned long lastTap = 0;
        unsigned long now = ::now();
        if (lastTap != 0) {
            float newBPM = tappedBpmFromInterval(now - lastTap);
            g_tappedBPM = newBPM;
            char buf[32];
            snprintf(buf, sizeof(buf), "Tapped BPM=%.1f", newBPM);
            context.displayManager.displayStatus(buf, 1500);
        }
        lastTap = now;
    } break;

    default:
        context.displayManager.displayStatus("UNKNOWN CTRL BTN", 1000);
        break;
    }
}

void ButtonManager::handleMultiButtonPress(uint8_t pressedButtons, ButtonManagerContext &context) {
    const uint8_t jitterMask = maskCtrl0 | maskCtrl3 | maskCtrl4;

    auto ensureActiveSlot = [&]() -> MIDISlot * {
        if (context.activePot >= NUM_SLOTS) {
            context.displayManager.displayStatus("Slot out of range", 1000);
            return nullptr;
        }
        return &context.configManager.getSlot(context.activePot);
    };

    // (0) Ctrl0 + Ctrl3 + Ctrl4: Jitter tuning mode (handled in scanControlInputs)
    if (pressedButtons == jitterMask) {
        context.displayManager.displayStatus("Jitter Mode", 1000);
    }
    // (0.5) Ctrl0 + Ctrl1 + Ctrl2: panic-safe reset to active profile baseline.
    else if (pressedButtons == panicMask) {
        arpeggiator.stop();
        g_arpEditActive = false;
        context.envelopeFollowMode = false;
        context.configManager.loadProfile(g_activeProfile);
        context.potChannels.clear();
        for (uint8_t i = 0; i < context.configManager.getNumPots(); ++i) {
            context.potChannels.push_back(context.configManager.getPotChannel(i));
        }
        context.profileRequests.requestReload();
        context.displayManager.displayStatus("Panic: Baseline", 1500);
    }
    // (0.75) Ctrl0 + Ctrl2 + Ctrl3 + Ctrl5: on-device config mode toggle.
    else if (pressedButtons == configModeMask) {
        if (_onDeviceConfigModeActive) {
            exitOnDeviceConfigMode(context, true);
        } else {
            enterOnDeviceConfigMode(context);
        }
    }
    // (0.8) Ctrl1 + Ctrl4 + Ctrl5: clock source toggle (EXT follow <-> forced INT).
    else if (pressedButtons == clockSourceMask) {
        g_followExternalClock = !g_followExternalClock;
        context.displayManager.displayStatus(g_followExternalClock ? "CLK SRC EXT" : "CLK SRC INT",
                                             1200);
    }
    // (0.85) Ctrl0 + Ctrl1 + Ctrl3: toggle LFO quick-tune mode.
    else if (pressedButtons == lfoTuningMask) {
        if (_lfoTuningActive) {
            exitLfoTuningMode(context);
        } else {
            enterLfoTuningMode(context);
        }
    } else if (_onDeviceConfigModeActive) {
        return;
    } else if (_lfoTuningActive) {
        return;
    }
    // (0.9) Ctrl0 + Ctrl1 + Ctrl4: make LFO 1 a live source for the active slot.
    // A never-configured lane starts centered at full depth so enabling it has
    // an audible effect; later toggles preserve user tuning.
    else if (pressedButtons == lfoLiveToggleMask) {
        MIDISlot &slot = context.configManager.getSlot(context.activePot);
        SlotLfoLane &lane = slot.lfo.lfo[0];
        const bool enable = !lane.enabled();
        if (enable && lane.amount == 0) {
            lane.setMode(ModCombineMode::Centered);
            lane.amount = 100;
        }
        lane.setEnabled(enable);
        slot.lfo = sanitizeSlotLfoConfig(slot.lfo);
        context.configManager.saveSlot(context.activePot, slot);

        context.displayManager.displayStatus(enable ? "LFO1 LIVE ON" : "LFO1 LIVE OFF", 1200);
        streamSlotPatch(context.configManager, context.activePot);
    }
    // (1) Ctrl3 + Ctrl4 + Ctrl5: toggle USB MIDI output
    else if ((pressedButtons & (maskCtrl3 | maskCtrl4 | maskCtrl5)) ==
             (maskCtrl3 | maskCtrl4 | maskCtrl5)) {
        context.configManager.setUsbMidiOutEnabled(!g_usbMidiOutEnabled);
        context.displayManager.displayStatus(g_usbMidiOutEnabled ? "USB MIDI ON" : "USB MIDI OFF",
                                             1500);
    }
    // (2) Ctrl0 + Ctrl1: Cycle EF’s ARG method if in ARG mode
    else if ((pressedButtons & (maskCtrl0 | maskCtrl1)) == (maskCtrl0 | maskCtrl1)) {
        MIDISlot *slot = ensureActiveSlot();
        if (slot == nullptr) {
            return;
        }
        constexpr size_t methodCount = sizeof(ALL_ARG_METHODS) / sizeof(ALL_ARG_METHODS[0]);
        size_t methodIndex = 0;
        for (; methodIndex < methodCount; ++methodIndex) {
            if (slot->arg.method == ALL_ARG_METHODS[methodIndex]) {
                break;
            }
        }
        methodIndex = (methodIndex + 1) % methodCount;

        slot->arg.enabled = 1;
        slot->arg.method = ALL_ARG_METHODS[methodIndex];
        context.configManager.saveSlot(context.activePot, *slot);

        context.configManager.setARGEnable(slot->arg.enabled);
        context.configManager.setARGMethod(static_cast<uint8_t>(slot->arg.method));

        context.configManager.setEnvelopePair(slot->arg.sourceA, slot->arg.sourceB);

        char msg[32];
        snprintf(msg, sizeof(msg), "Slot %d ARG=%s", context.activePot,
                 ARG_METHOD_NAMES[methodIndex]);
        context.displayManager.displayStatus(msg, 1500);
        streamSlotPatch(context.configManager, context.activePot);
        streamArgPatch(context.configManager);
    }
    // (3) Ctrl0 + Ctrl2: Cycle ARG envelope pair
    else if ((pressedButtons & (maskCtrl0 | maskCtrl2)) == (maskCtrl0 | maskCtrl2)) {
        MIDISlot *slot = ensureActiveSlot();
        if (slot == nullptr) {
            return;
        }
        static size_t pairIndex = 0;
        pairIndex = (pairIndex + 1) % NUM_ARG_PAIRS;
        const auto &pair = ARG_PAIRS[pairIndex];
        const uint8_t sourceA = normalizeEnvelopeIndex(pair.first);
        const uint8_t sourceB = normalizeEnvelopeIndex(pair.second);

        slot->arg.enabled = 1;
        slot->arg.sourceA = sourceA;
        slot->arg.sourceB = sourceB;
        context.configManager.saveSlot(context.activePot, *slot);

        context.configManager.setARGEnable(slot->arg.enabled);
        context.configManager.setARGMethod(static_cast<uint8_t>(slot->arg.method));
        context.configManager.setEnvelopePair(sourceA, sourceB);

        char buf[32];
        snprintf(buf, sizeof(buf), "Slot %d: EF%u+EF%u", context.activePot, sourceA + 1,
                 sourceB + 1);
        context.displayManager.displayStatus(buf, 1500);
        streamSlotPatch(context.configManager, context.activePot);
        streamArgPatch(context.configManager);
    }
    // (4) Ctrl3 + Ctrl4: Cycle light modes
    else if ((pressedButtons & (maskCtrl3 | maskCtrl4)) == (maskCtrl3 | maskCtrl4)) {
        static uint8_t currentLightMode = 0;
        currentLightMode = (currentLightMode + 1) % 4;
        context.ledManager.setModeDisplay(currentLightMode);
        char buf[32];
        snprintf(buf, sizeof(buf), "LightMode=%d", currentLightMode);
        context.displayManager.displayStatus(buf, 1500);
    }
    // (5) Ctrl0 + Ctrl4: Enable EF and randomize settings
    else if ((pressedButtons & (maskCtrl0 | maskCtrl4)) == (maskCtrl0 | maskCtrl4)) {
        if (!context.envelopeFollowMode) {
            context.envelopeFollowMode = true;
            context.displayManager.displayStatus("EF turned ON", 1000);
        }
        int randomEF = random(context.envelopes.size());
        MIDISlot &slotRef = context.configManager.getSlot(context.activePot);
        MIDISlot::EfSettings settings = slotRef.efSettings;
        settings.followerIndex = slotRef.getEnvelopeFollowerIndex();
        settings.followerIndex = static_cast<int8_t>(randomEF);
        commitEfSettings(context, context.activePot, settings);
        context.envelopes[randomEF].toggleActive(true);
        char buf[32];
        snprintf(buf, sizeof(buf), "Slot %d->RandomEF %d", context.activePot, randomEF);
        context.displayManager.displayStatus(buf, 1500);
        streamEnvelopeAssignment(context.activePot, randomEF);
    }
    // (6) Ctrl4 + Ctrl5: Set active slot to MIDI Note mode
    else if ((pressedButtons & (maskCtrl4 | maskCtrl5)) == (maskCtrl4 | maskCtrl5)) {
        context.configManager.setSlotType(context.activePot, MIDIMessageType::Note);
        char buf[32];
        snprintf(buf, sizeof(buf), "Slot %d => NOTE", context.activePot);
        context.displayManager.displayStatus(buf, 1500);
        streamSlotPatch(context.configManager, context.activePot);
    }
    // (7) Ctrl3 + Ctrl5: Set active slot to Program Change
    else if ((pressedButtons & (maskCtrl3 | maskCtrl5)) == (maskCtrl3 | maskCtrl5)) {
        context.configManager.setSlotType(context.activePot, MIDIMessageType::ProgramChange);
        char buf[32];
        snprintf(buf, sizeof(buf), "Slot %d => PROG", context.activePot);
        context.displayManager.displayStatus(buf, 1500);
        streamSlotPatch(context.configManager, context.activePot);
    }
    // (8) Ctrl0 + Ctrl5: Set active slot to Pitch Bend
    else if ((pressedButtons & (maskCtrl0 | maskCtrl5)) == (maskCtrl0 | maskCtrl5)) {
        context.configManager.setSlotType(context.activePot, MIDIMessageType::PitchBend);
        char buf[32];
        snprintf(buf, sizeof(buf), "Slot %d => BEND", context.activePot);
        context.displayManager.displayStatus(buf, 1500);
        streamSlotPatch(context.configManager, context.activePot);
    }
    // (9) Ctrl1 + Ctrl4: Set active slot to Aftertouch
    else if ((pressedButtons & (maskCtrl1 | maskCtrl4)) == (maskCtrl1 | maskCtrl4)) {
        context.configManager.setSlotType(context.activePot, MIDIMessageType::Aftertouch);
        char buf[32];
        snprintf(buf, sizeof(buf), "Slot %d => AFTER", context.activePot);
        context.displayManager.displayStatus(buf, 1500);
        streamSlotPatch(context.configManager, context.activePot);
    }
    // (10) Ctrl1 + Ctrl5: Toggle MIDI clock output
    else if ((pressedButtons & (maskCtrl1 | maskCtrl5)) == (maskCtrl1 | maskCtrl5)) {
        g_clockOutEnabled = !g_clockOutEnabled;
        context.displayManager.displayStatus(g_clockOutEnabled ? "CLK OUT ON" : "CLK OUT OFF",
                                             1000);
    }
    // (11) Ctrl2 + Ctrl5: Set active slot to NRPN
    else if ((pressedButtons & (maskCtrl2 | maskCtrl5)) == (maskCtrl2 | maskCtrl5)) {
        context.configManager.setSlotType(context.activePot, MIDIMessageType::NRPN);
        char buf[32];
        snprintf(buf, sizeof(buf), "Slot %d => NRPN", context.activePot);
        context.displayManager.displayStatus(buf, 1500);
        streamSlotPatch(context.configManager, context.activePot);
    }
    // (12) Ctrl1 + Ctrl3: Set active slot to RPN
    else if ((pressedButtons & (maskCtrl1 | maskCtrl3)) == (maskCtrl1 | maskCtrl3)) {
        context.configManager.setSlotType(context.activePot, MIDIMessageType::RPN);
        char buf[32];
        snprintf(buf, sizeof(buf), "Slot %d => RPN", context.activePot);
        context.displayManager.displayStatus(buf, 1500);
        streamSlotPatch(context.configManager, context.activePot);
    }
    // (13) Ctrl0 + Ctrl3: Set active slot to SysEx
    else if ((pressedButtons & (maskCtrl0 | maskCtrl3)) == (maskCtrl0 | maskCtrl3)) {
        context.configManager.setSlotType(context.activePot, MIDIMessageType::SysEx);
        char buf[32];
        snprintf(buf, sizeof(buf), "Slot %d => SYSEX", context.activePot);
        context.displayManager.displayStatus(buf, 1500);
        streamSlotPatch(context.configManager, context.activePot);
    }
    // (14) Ctrl2 + Ctrl4: Toggle arpeggiator for active slot
    else if ((pressedButtons & (maskCtrl2 | maskCtrl4)) == (maskCtrl2 | maskCtrl4)) {
        if (arpeggiator.isActive(context.activePot)) {
            arpeggiator.stop(context.activePot);
            context.displayManager.displayStatus("ARP OFF", 1000);
        } else {
            if (arpeggiator.startIfAssigned(context.activePot)) {
                context.displayManager.displayStatus("ARP ON", 1000);
            } else {
                context.displayManager.displayStatus("ARP UNASSIGNED", 1200);
            }
        }
    }
    // (15) Ctrl2 + Ctrl3: Increment arpeggiator base note
    else if ((pressedButtons & (maskCtrl2 | maskCtrl3)) == (maskCtrl2 | maskCtrl3)) {
        MIDISlot &slot = context.configManager.getSlot(context.activePot);
        slot.arpNote = (slot.arpNote + 1) % 128;
        context.configManager.saveSlot(context.activePot, slot);
        char buf[32];
        snprintf(buf, sizeof(buf), "ARP NOTE %d", slot.arpNote);
        context.displayManager.displayStatus(buf, 1000);
        streamSlotPatch(context.configManager, context.activePot);
    }
    // (16) Ctrl1 + Ctrl2: Cycle configuration profiles
    else if ((pressedButtons & (maskCtrl1 | maskCtrl2)) == (maskCtrl1 | maskCtrl2)) {
        g_activeProfile = static_cast<uint8_t>((g_activeProfile + 1) % NUM_PROFILES);
        context.configManager.setActiveProfile(g_activeProfile);
        context.configManager.loadProfile(g_activeProfile);
        context.potChannels.clear();
        for (uint8_t i = 0; i < context.configManager.getNumPots(); ++i) {
            context.potChannels.push_back(context.configManager.getPotChannel(i));
        }
        char buf[32];
        snprintf(buf, sizeof(buf), "PROFILE %c", static_cast<char>('A' + g_activeProfile));
        context.displayManager.displayStatus(buf, 1500);
        context.profileRequests.requestReload();
    }
}

void ButtonManager::scanControlInputs(ButtonManagerContext &context) {
    unsigned long now = ::now();
    _scanner.scanControlBank(now);
    for (uint8_t idx = 0; idx < NUM_CONTROL_BUTTONS; ++idx) {
        updateCtrlButton(idx, _scanner.isPressed(NUM_VIRTUAL_BUTTONS + idx), context);
    }

    // After updating each control button, check for multi-button combos
    const uint8_t mask = _scanner.controlMask();
    _controlHelpMask = mask;
    const uint8_t jitterMask = maskCtrl0 | maskCtrl3 | maskCtrl4;
    bool jitterActive = (mask == jitterMask) && !_onDeviceConfigModeActive && !_lfoTuningActive &&
                        !context.diagnosticMode;
    g_jitterTuningActive = jitterActive;
    if (jitterActive) {
        context.ledManager.setPanelModeIndicator(PanelModeIndicator::Jitter);
    } else if (!_onDeviceConfigModeActive && !_lfoTuningActive && !context.diagnosticMode) {
        context.ledManager.setPanelModeIndicator(PanelModeIndicator::None);
    }
    dispatchGestureEvents(
        _gesture.updateControlMask(mask, now, !_onDeviceConfigModeActive && !_lfoTuningActive),
        context);

    for (uint8_t i = 0; i < 3; ++i) {
        _ctrlPotValues[i] =
            Utility::exponentialMovingAverage(_scanner.controlPotRaw(i), _ctrlPotValues[i], 0.1f);
    }

    if (_onDeviceConfigModeActive) {
        int16_t bucket = static_cast<int16_t>(map(_ctrlPotValues[0], 0, 1023, 0, 127));
        bucket = constrain(bucket, static_cast<int16_t>(0), static_cast<int16_t>(127));
        if (_lastConfigFloorPotBucket < 0) {
            _lastConfigFloorPotBucket = bucket;
        } else {
            int16_t delta = bucket - _lastConfigFloorPotBucket;
            if (abs(delta) >= 2) {
                int floor = constrain(static_cast<int>(context.configManager.getEfIdleFloor()) +
                                          static_cast<int>(delta),
                                      0, 127);
                context.configManager.setEfIdleFloor(static_cast<uint8_t>(floor));
                _lastConfigFloorPotBucket = bucket;
                char buf[24];
                snprintf(buf, sizeof(buf), "EF Floor=%d", floor);
                context.displayManager.displayStatus(buf, kTuningStatusMs);
            }
        }
    }

    if (jitterActive) {
        float depth =
            Utility::scale(static_cast<float>(_ctrlPotValues[0]), 0.0f, 1023.0f, 0.0f, 1.0f);
        float smooth =
            Utility::scale(static_cast<float>(_ctrlPotValues[1]), 0.0f, 1023.0f, 0.0f, 1.0f);
        depth = constrain(depth, 0.0f, 1.0f);
        smooth = constrain(smooth, 0.0f, 1.0f);

        if (g_jitterRemoteControlActive) {
            if (!g_jitterDepthLatched && fabsf(depth - g_jitterSettings.depth) <= 0.02f) {
                g_jitterDepthLatched = true;
            }
            if (!g_jitterSmoothnessLatched &&
                fabsf(smooth - g_jitterSettings.smoothness) <= 0.02f) {
                g_jitterSmoothnessLatched = true;
            }
            if (!(g_jitterDepthLatched && g_jitterSmoothnessLatched)) {
                return;
            }
            g_jitterRemoteControlActive = false;
        }

        bool depthChanged = (_lastJitterDepth < 0.0f) || (fabsf(depth - _lastJitterDepth) >= 0.01f);
        bool smoothChanged =
            (_lastJitterSmoothness < 0.0f) || (fabsf(smooth - _lastJitterSmoothness) >= 0.01f);

        g_jitterSettings.depth = depth;
        g_jitterSettings.smoothness = smooth;

        if (depthChanged) {
            char buf[32];
            snprintf(buf, sizeof(buf), "Jitter: %.2f", depth);
            context.displayManager.displayStatus(buf, kTuningStatusMs);
            _lastJitterDepth = depth;
        } else if (smoothChanged) {
            char buf[32];
            snprintf(buf, sizeof(buf), "Smooth: %.2f", smooth);
            context.displayManager.displayStatus(buf, kTuningStatusMs);
            _lastJitterSmoothness = smooth;
        }
    }

    if (_lfoTuningActive) {
        const uint8_t index = _lfoTuningIndex % LFOManager::kMaxLFOs;
        LFO &lfo = lfoManager.lfo(index);
        float freqHz =
            Utility::scale(static_cast<float>(_ctrlPotValues[0]), 0.0f, 1023.0f, 0.05f, 12.0f);
        float depth =
            Utility::scale(static_cast<float>(_ctrlPotValues[1]), 0.0f, 1023.0f, 0.0f, 1.0f);
        const int modeRaw = _ctrlPotValues[2];
        freqHz = constrain(freqHz, 0.05f, 12.0f);
        depth = constrain(depth, 0.0f, 1.0f);
        lfo.setFrequencyHz(freqHz);
        lfo.setDepth(depth);

        bool freqChanged =
            (_lastLfoTuneFreqHz < 0.0f) || (fabsf(freqHz - _lastLfoTuneFreqHz) >= 0.05f);
        bool depthChanged =
            (_lastLfoTuneDepth < 0.0f) || (fabsf(depth - _lastLfoTuneDepth) >= 0.02f);
        if (freqChanged) {
            char buf[32];
            snprintf(buf, sizeof(buf), "LFO%u Hz %.2f", static_cast<unsigned>(index + 1), freqHz);
            context.displayManager.displayStatus(buf, kTuningStatusMs);
            _lastLfoTuneFreqHz = freqHz;
        } else if (depthChanged) {
            char buf[32];
            snprintf(buf, sizeof(buf), "LFO%u D %.2f", static_cast<unsigned>(index + 1), depth);
            context.displayManager.displayStatus(buf, kTuningStatusMs);
            _lastLfoTuneDepth = depth;
        }

        if (lfo.isSyncEnabled()) {
            uint8_t ratioIndex = static_cast<uint8_t>(map(modeRaw, 0, 1023, 0, 7));
            ratioIndex = constrain(ratioIndex, static_cast<uint8_t>(0), static_cast<uint8_t>(7));
            lfo.setSyncRatio(static_cast<LFOSyncRatio>(ratioIndex));
            if (_lastLfoTuneRatioIndex != static_cast<int8_t>(ratioIndex)) {
                char buf[32];
                snprintf(buf, sizeof(buf), "LFO%u Sync %s", static_cast<unsigned>(index + 1),
                         lfoSyncRatioLabel(static_cast<LFOSyncRatio>(ratioIndex)));
                context.displayManager.displayStatus(buf, kTuningStatusMs);
                _lastLfoTuneRatioIndex = static_cast<int8_t>(ratioIndex);
                _lastLfoTuneBipolarState = -1;
            }
        } else {
            bool bipolar = (modeRaw >= 512);
            lfo.setBipolar(bipolar);
            int8_t bipolarState = bipolar ? 1 : 0;
            if (_lastLfoTuneBipolarState != bipolarState) {
                char buf[24];
                snprintf(buf, sizeof(buf), "LFO%u %s", static_cast<unsigned>(index + 1),
                         bipolar ? "Bipolar" : "Unipolar");
                context.displayManager.displayStatus(buf, kTuningStatusMs);
                _lastLfoTuneBipolarState = bipolarState;
                _lastLfoTuneRatioIndex = -1;
            }
        }
    }
}

void ButtonManager::updateCtrlButton(uint8_t index, bool pressed, ButtonManagerContext &context) {
    updateButtonStateMachine(NUM_VIRTUAL_BUTTONS + index, pressed, context);
}

void ButtonManager::cancelPendingConfirm(ButtonManagerContext &context) {
    _gesture.cancelConfirmation();
    if (context.ledManager.isWarningActive()) {
        context.ledManager.clearWarningAnimation();
    }
}

void ButtonManager::startWarningForIndex(uint8_t index, ButtonManagerContext &context) {
    if (index < NUM_VIRTUAL_BUTTONS) {
        if (context.ledManager.isWarningActive()) {
            context.ledManager.clearWarningAnimation();
        }
        return;
    }

    uint8_t ctrlIdx = index - NUM_VIRTUAL_BUTTONS;
    switch (ctrlIdx) {
    case 3:
        context.ledManager.beginWarningAnimation(LEDWarning::Destructive);
        break;
    case 5:
        context.ledManager.beginWarningAnimation(LEDWarning::Diagnostic);
        break;
    default:
        if (context.ledManager.isWarningActive()) {
            context.ledManager.clearWarningAnimation();
        }
        break;
    }
}

bool ButtonManager::isMuxButtonPressed(uint8_t index) const {
    return _scanner.readMatrixButton(index) == HIGH;
}
