bseverns/MOARkNOBS-42/firmware/include/MIDITypes.h

// include/MidiTypes.h
#ifndef MIDI_TYPES_H
#define MIDI_TYPES_H

#include <array>
#include <cstdint>

#include "SysExTemplateTypes.h"
#include "protocol/ManifestContract.h"

// Supported MIDI message types for a slot.
enum class MIDIMessageType : uint8_t {
    OFF = 0, // Slot disabled
    CC,      // Control Change
    Note,    // Note on/off
    PitchBend,
    ProgramChange,
    Aftertouch,
    ModWheel, // Modulation wheel (CC1)
    NRPN,     // Non-Registered Parameter Number send
    RPN,      // Registered Parameter Number send
    SysEx     // System Exclusive thrasher
};

// Classification for the most recent SysEx packet.
enum class SysExType : uint8_t {
    ManufacturerSpecific = 0, // Vendor IDs other than 7E/7F
    UniversalNonRealTime,     // 0x7E per the MIDI spec
    UniversalRealTime         // 0x7F per the MIDI spec
};

// Enumerates how the per-slot ARG mixer should blend its envelope pair.
enum class ARGMethod : uint8_t {
    PLUS = 0,
    MIN,
    PECK,
    SHAV,
    SQAR,
    BABS,
    TABS,
    MULT,
    DIVI,
    AVG,
    XABS,
    MAXX,
    MINN,
    XORR,
};

// How a slot-local EF contribution is folded into the outgoing MIDI value.
enum class EfDestinationMode : uint8_t {
    AddClamp = 0, // Current default: base pot value + EF contribution, clamped 0..127
    Subtract,     // Base pot value - EF contribution, clamped 0..127
    Replace,      // EF contribution replaces the base pot value
    Scale,        // EF contribution scales the base pot value
    Centered,     // EF contribution is treated as a centered bipolar offset
};

// How one fixed per-slot LFO lane composes with the value produced before it.
enum class ModCombineMode : uint8_t {
    AddClamp = 0, // Add a unipolar 0..127 contribution, then clamp
    Subtract,     // Subtract a unipolar 0..127 contribution, then clamp
    Replace,      // Replace with a bipolar value centered at 64
    Scale,        // Scale the preceding value with a bipolar factor
    Centered,     // Add a bipolar -64..+63 offset
};

struct __attribute__((packed)) SlotLfoLane {
    static constexpr uint8_t kEnabledMask = 0x01;
    static constexpr uint8_t kModeMask = 0x0E;
    static constexpr uint8_t kModeShift = 1;

    // Disabled by default, with Centered selected for the first enable.
    uint8_t flags = static_cast<uint8_t>(ModCombineMode::Centered) << kModeShift;
    int8_t amount = 0; // Signed modulation depth (-100..100 percent)

    bool enabled() const { return (flags & kEnabledMask) != 0; }
    ModCombineMode mode() const {
        return static_cast<ModCombineMode>((flags & kModeMask) >> kModeShift);
    }
    void setEnabled(bool value) {
        flags = value ? static_cast<uint8_t>(flags | kEnabledMask)
                      : static_cast<uint8_t>(flags & ~kEnabledMask);
    }
    void setMode(ModCombineMode value) {
        flags = static_cast<uint8_t>((flags & ~kModeMask) |
                                     (static_cast<uint8_t>(value) << kModeShift));
    }
};

// std::array is not a POD type under GCC 15, so applying `packed` to this
// wrapper is rejected. Its packed two-byte lane elements already give the
// wrapper the required four-byte persistence layout without that attribute.
struct SlotLfoConfig {
    std::array<SlotLfoLane, 2> lfo{};
};

static_assert(sizeof(SlotLfoConfig) == 4, "Slot LFO configuration layout drifted");

inline SlotLfoLane sanitizeSlotLfoLane(const SlotLfoLane &candidate) {
    SlotLfoLane lane = candidate;
    lane.flags &= static_cast<uint8_t>(SlotLfoLane::kEnabledMask | SlotLfoLane::kModeMask);
    if (static_cast<uint8_t>(lane.mode()) > static_cast<uint8_t>(ModCombineMode::Centered)) {
        lane.setMode(ModCombineMode::Centered);
    }
    if (lane.amount < -100) lane.amount = -100;
    if (lane.amount > 100) lane.amount = 100;
    return lane;
}

inline SlotLfoConfig sanitizeSlotLfoConfig(const SlotLfoConfig &candidate) {
    SlotLfoConfig config = candidate;
    for (SlotLfoLane &lane : config.lfo) {
        lane = sanitizeSlotLfoLane(lane);
    }
    return config;
}

// Envelope follower payload persisted alongside the slot definition.
struct SlotEnvelopePayload {
    uint8_t filterType = 0; // EnvelopeFollower::FilterType value
    float frequency = 0.0f; // Stored cutoff/shape frequency (Hz or scalar)
    float q = 0.0f;         // Stored resonance/Q for biquad-driven modes
};

// Slot-local configuration for the ARG combiner.
struct SlotARGConfig {
    uint8_t enabled = 0;                // Non-zero enables ARG processing for this slot
    ARGMethod method = ARGMethod::PLUS; // Mixer math to apply when ARG is on
    uint8_t sourceA = 0;                // Primary envelope index
    uint8_t sourceB = 1;                // Secondary envelope index
};

inline constexpr uint8_t SLOT_ARG_SOURCE_COUNT = 6;

inline SlotARGConfig sanitizeSlotArg(const SlotARGConfig &candidate) {
    SlotARGConfig sanitized = candidate;
    sanitized.enabled = candidate.enabled ? 1 : 0;
    if (static_cast<uint8_t>(sanitized.method) > static_cast<uint8_t>(ARGMethod::XORR)) {
        sanitized.method = ARGMethod::PLUS;
    }
    if (sanitized.sourceA >= SLOT_ARG_SOURCE_COUNT) sanitized.sourceA = 0;
    if (sanitized.sourceB >= SLOT_ARG_SOURCE_COUNT) {
        sanitized.sourceB = static_cast<uint8_t>((sanitized.sourceA + 1U) %
                                                 SLOT_ARG_SOURCE_COUNT);
    }
    if (sanitized.sourceA == sanitized.sourceB) {
        sanitized.sourceB = static_cast<uint8_t>((sanitized.sourceA + 1U) %
                                                 SLOT_ARG_SOURCE_COUNT);
    }
    return sanitized;
}

struct MIDISlot {
    // Envelope follower configuration scoped to this slot.
    struct EfSettings {
        // Filter shapes mirrored from EnvelopeFollower::FilterType.
        enum class FilterType : uint8_t {
            Linear = 0,
            OppositeLinear,
            Exponential,
            Random,
            Lowpass,
            Highpass,
            Bandpass
        };

        int8_t followerIndex = -1; // Assigned hardware follower (-1 when unbound)
        uint8_t oversample = 4;    // ADC oversample count (1 == disabled)
        FilterType filterType = FilterType::Linear;
        uint8_t efMode = 0;            // EnvelopeFollower::EFMode value
        uint8_t autoBaseline = 1;      // Enable auto-baseline tracking
        uint8_t autoGain = 1;          // Enable auto-gain tracking
        uint8_t gateThreshold = 16;    // Gate threshold (0-127)
        uint8_t gateHysteresis = 4;    // Gate hysteresis (0-127)
        uint8_t activityThreshold = 4; // Activity threshold (0-127)
        uint8_t gainTarget = 102;      // Auto-gain target (0-127)
        uint8_t destinationMode =
            static_cast<uint8_t>(EfDestinationMode::AddClamp); // EfDestinationMode value
        uint16_t attackMs = 5;         // Attack time for Peak/Follower modes
        uint16_t releaseMs = 20;       // Release time for Peak/Follower modes
        uint16_t rmsWindowMs = 50;     // RMS integration window
        uint16_t baselineTauMs = 2000; // Auto-baseline time constant
        uint16_t gainTauMs = 3000;     // Auto-gain time constant
        float frequency = 1000.0f;     // Cutoff/shape frequency in Hz
        float q = 0.707f;              // Resonance / secondary filter parameter
        float smoothing = 0.2f;        // EWMA smoothing factor (0..1)
        float baseline = 0.0f;         // Noise floor offset after calibration
        float gain = 1.0f;             // Output gain applied post-baseline
    };

    MIDIMessageType type = MIDIMessageType::OFF;
    uint8_t midiChannel = 1;
    uint8_t data1 = 0;
    bool active = false;
    uint8_t arpNote = 0; // Base note for arpeggiator
    uint8_t sysexLength = 0;
    EfSettings efSettings{}; // Slot-specific envelope follower settings
    std::array<uint8_t, SysExTemplate::kMaxLength> sysexTemplate{};
    struct EfRuntime {
        int8_t followerIndex = -1; // Currently assigned hardware follower (-1 when unbound)
    };
    EfRuntime ef{};      // Live envelope follower assignment metadata
    SlotARGConfig arg{}; // Slot-local ARG mixer settings
    SlotLfoConfig lfo{}; // Fixed slot-local lanes for LFO 1 and LFO 2

    // Update both persistent and runtime follower assignments in lockstep.
    void setEnvelopeFollowerIndex(int8_t index) {
        ef.followerIndex = index;
        efSettings.followerIndex = index;
    }

    // Convenience accessor mirroring the currently assigned follower index.
    int8_t getEnvelopeFollowerIndex() const { return ef.followerIndex; }
};

constexpr uint8_t NUM_SLOTS = ManifestContract::kSlotCount;
inline constexpr uint8_t EF_OVERSAMPLE_MIN = 1;
inline constexpr uint8_t EF_OVERSAMPLE_MAX = 32;
inline constexpr uint16_t EF_TIME_MIN_MS = 1;
inline constexpr uint16_t EF_TIME_MAX_MS = 60000;
inline constexpr float EF_FILTER_FREQ_MIN_HZ = 20.0f;
inline constexpr float EF_FILTER_FREQ_MAX_HZ = 5000.0f;
inline constexpr float EF_FILTER_Q_MIN = 0.5f;
inline constexpr float EF_FILTER_Q_MAX = 4.0f;

// The slot struct picked up a richer envelope follower payload which nudged it
// past the original 64-byte budget. We still guard the footprint, but give it a
// little more breathing room so the build doesn't implode every time we add a
// tuning parameter.
static_assert(sizeof(MIDISlot) <= 80, "MIDISlot exploded past the expected 80 bytes");

#endif // MIDI_TYPES_H
