bseverns/MOARkNOBS-42/firmware/include/DisplayManager.h

// Provides simple wrappers around the OLED display for status output.
// Updated by ButtonManager, MIDIHandler and the main loop.
// Manages startup animation and idle screensaver.
#ifndef DISPLAYMANAGER_H
#define DISPLAYMANAGER_H

#include <Arduino.h>
#include <Adafruit_GFX.h>
#include <Adafruit_SSD1306.h>
#include <array>
#include <cstddef>
#include "Globals.h" // for OLED_WIDTH, OLED_HEIGHT

struct ButtonManagerContext;
class ButtonManager;
class MIDIHandler;
struct SystemDiagnostics;

/*
Animation & Timing 101
----------------------
`Animation` is a tiny state machine that handles brightness fades. Call
`triggerFade()` to kick it awake and `updateFadeAnimation()` each loop to
march through `FADE_IN`, `HOLD`, and `FADE_OUT` states based on `lastTime`
and `duration`. Once the party hits `DONE`, the screen stays put until the
next trigger.

`updateFromContext()` is the high‑level refresh that keeps the UI snappy
without frying the MCU. It bails out early unless at least `_updateIntervalMs`
milliseconds have passed since the last update. Tweak that interval with
`setUpdateInterval()` to get your preferred balance of responsiveness and
chill.

Example mash‑up: fade into the screensaver when the user ghosts you:
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
